ShenYuan-sean/Underwater-AprilTag-Board/check/0.png

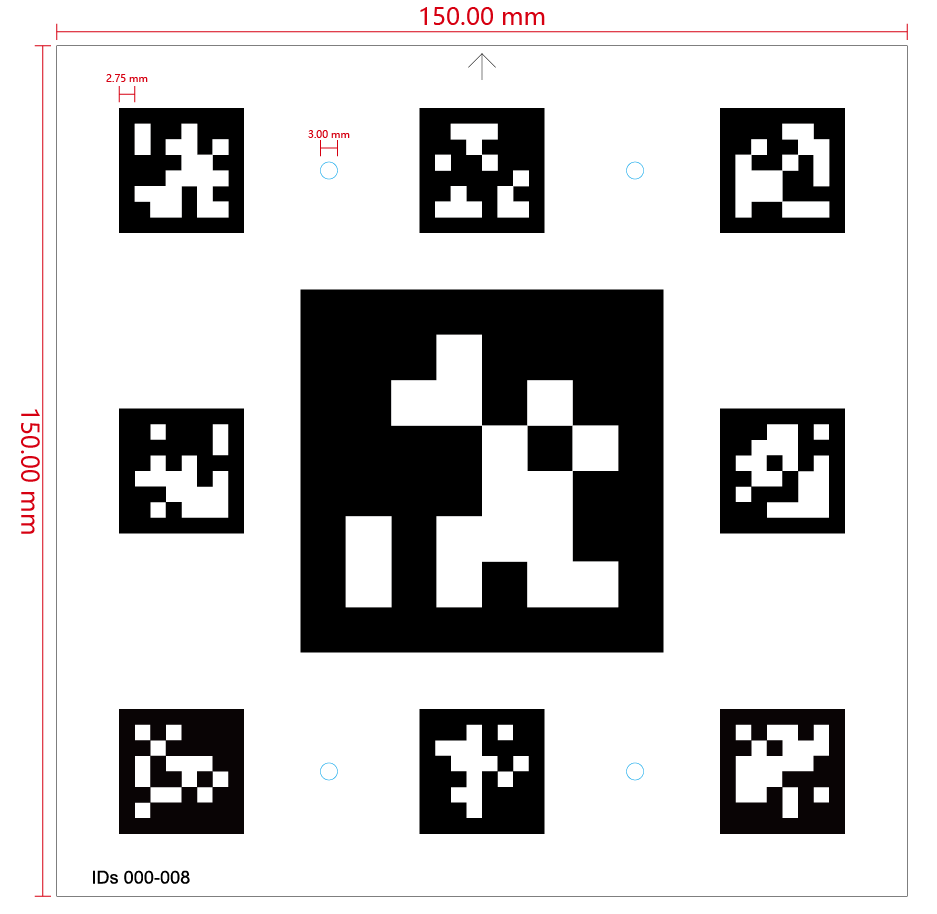
check/0.png
