ShenYuan-sean/Underwater-AprilTag-Board/check/1.png

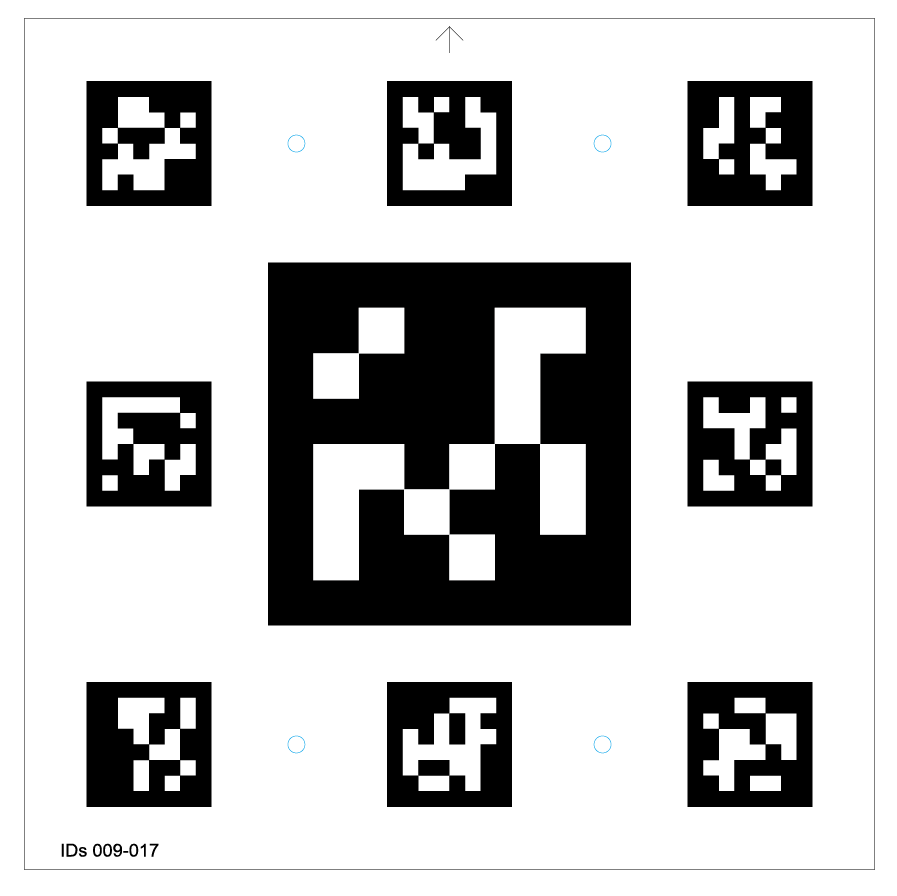
check/1.png
