ShenYuan-sean/Underwater-AprilTag-Board/check/2.png

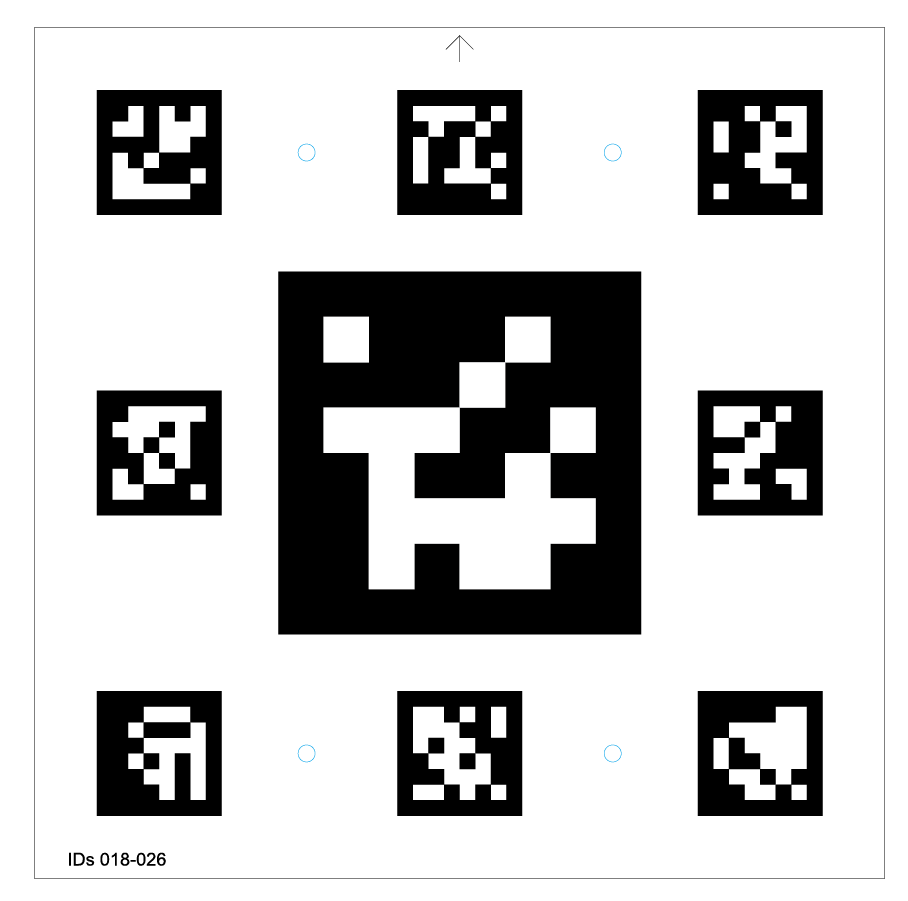
check/2.png
