ShenYuan-sean/Underwater-AprilTag-Board/check/3.png

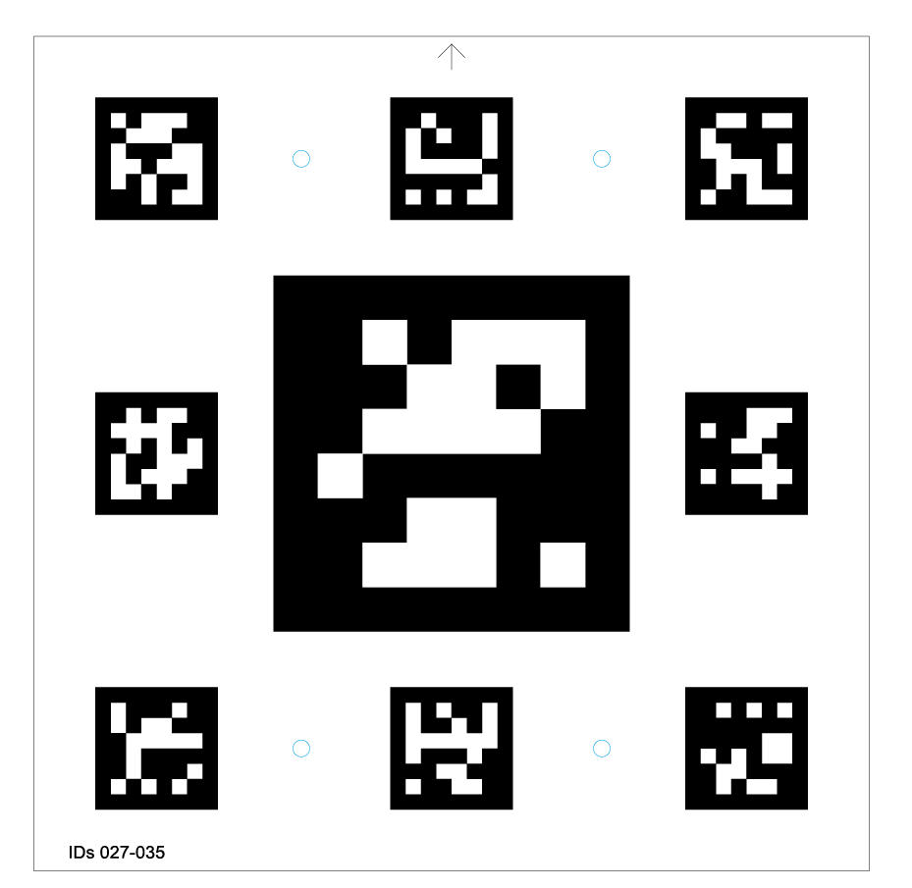
check/3.png
