ShenYuan-sean/Underwater-AprilTag-Board/check/4.png

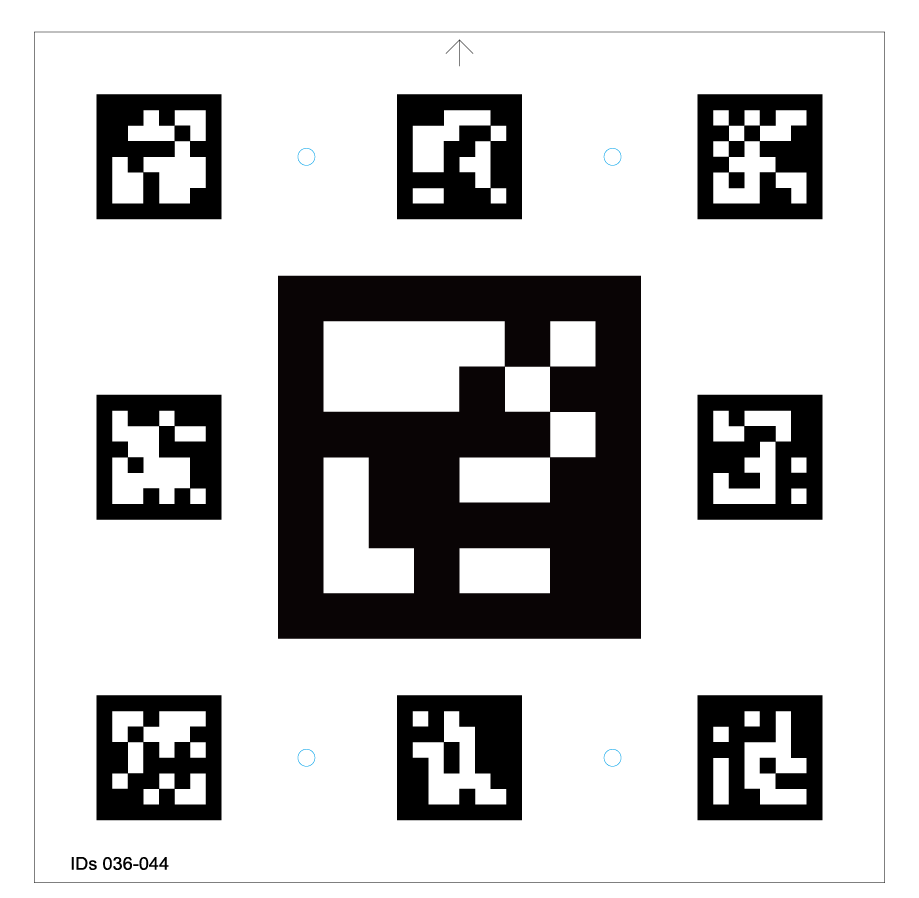
check/4.png
