ShenYuan-sean/Underwater-AprilTag-Board/check/5.png

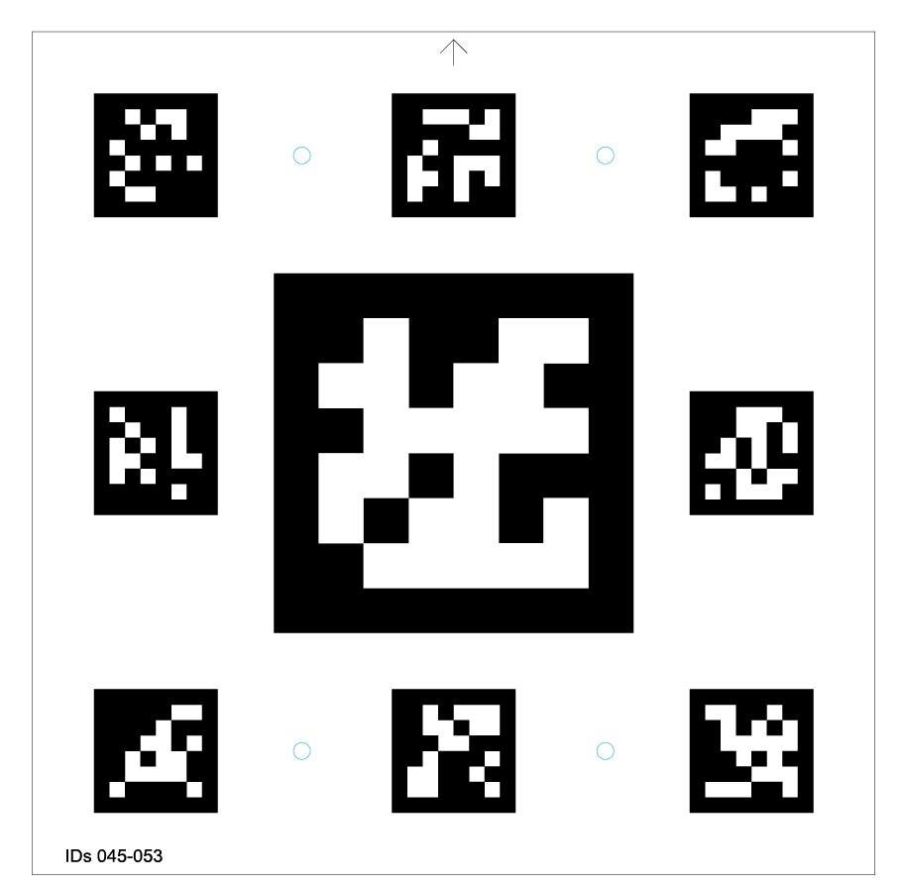
check/5.png
