ShenYuan-sean/Underwater-AprilTag-Board/Reservoir-AprilTag-Boards-20/加工厂复核/微信图片_20260824111517_369_489.png

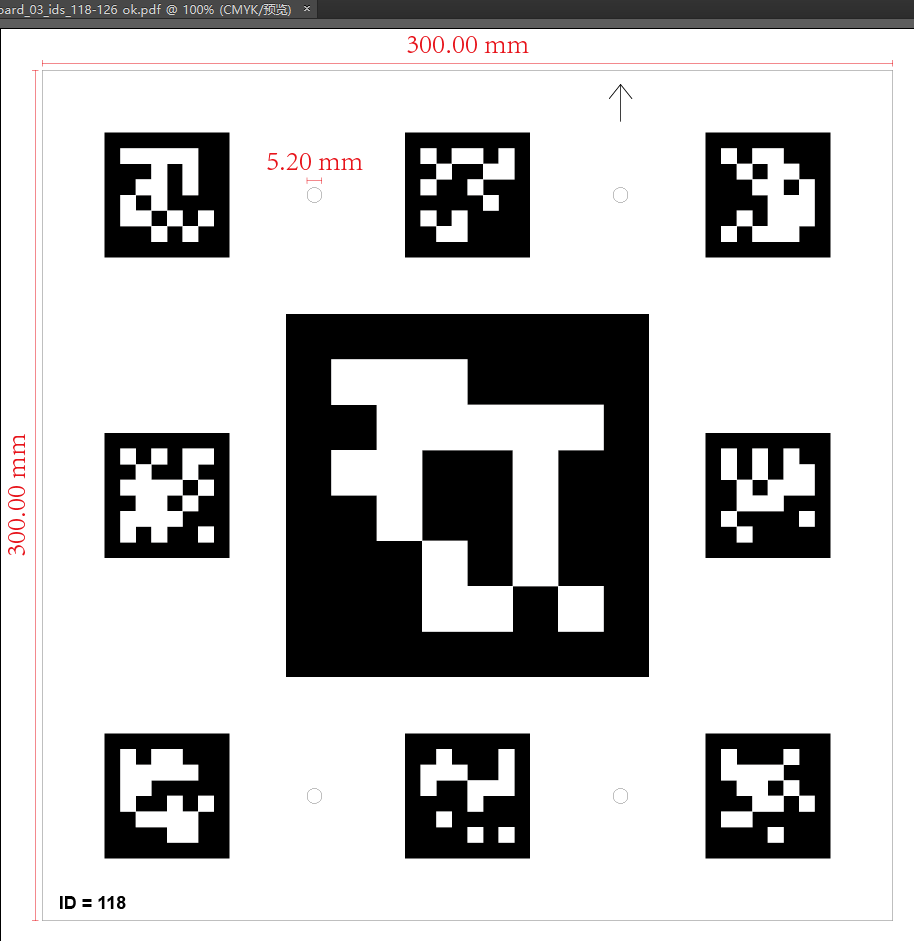
Reservoir-AprilTag-Boards-20/加工厂复核/微信图片_20260824111517_369_489.png
