ShenYuan-sean/Underwater-AprilTag-Board/Reservoir-AprilTag-Boards-20/加工厂复核/微信图片_20260824111823_383_489.png

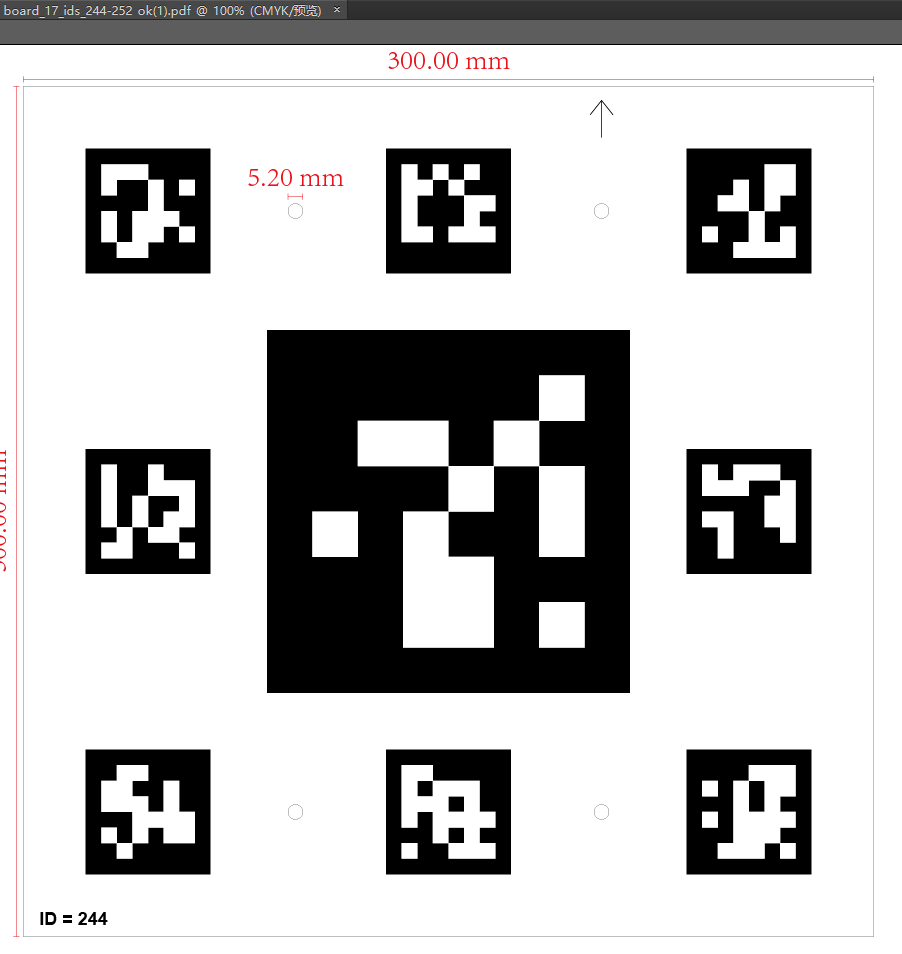
Reservoir-AprilTag-Boards-20/加工厂复核/微信图片_20260824111823_383_489.png
