ShenYuan-sean/Underwater-AprilTag-Board/Reservoir-AprilTag-Boards-20/generated/boards/board_13_ids_208-216.dxf

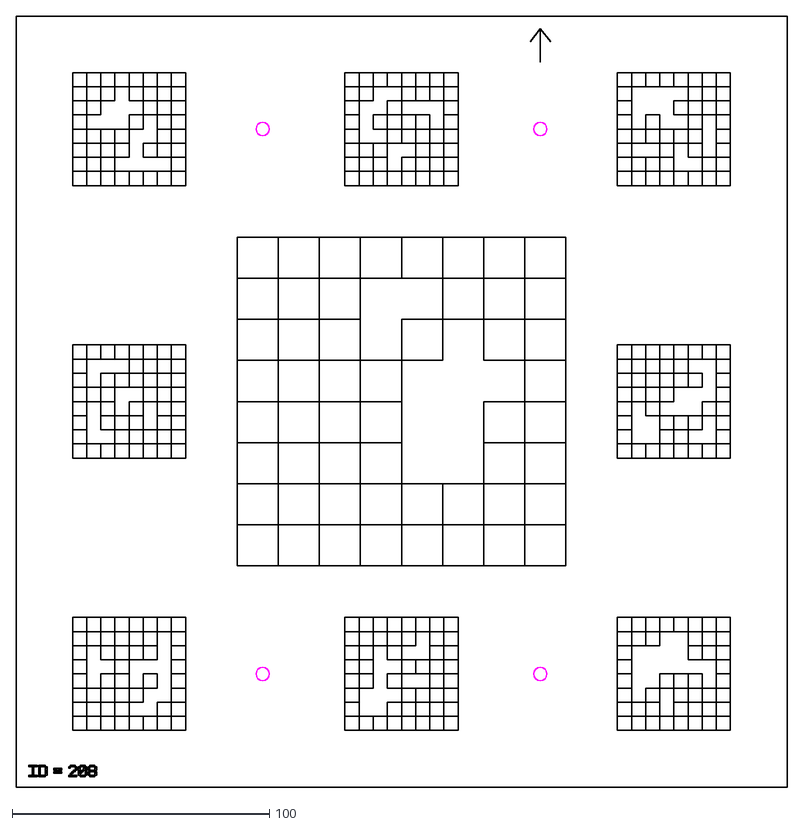
[picture p74: CAD file, 2026-08-25]
Reservoir-AprilTag-Boards-20/generated/boards/board_13_ids_208-216.dxf
300.0 x 300.0
