ShenYuan-sean/Underwater-AprilTag-Board/generated/face_02_guide.dxf

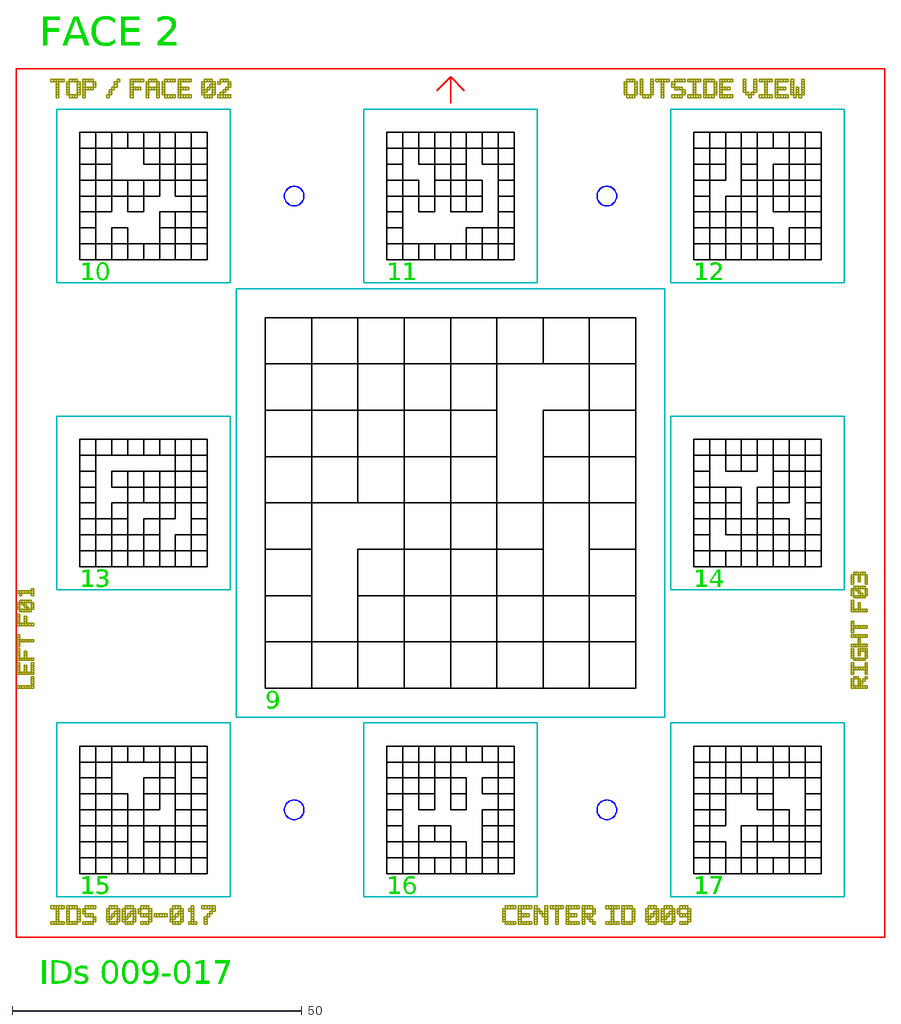
[picture p75: CAD file, 2026-08-11]
generated/face_02_guide.dxf
FACE 2
IDs 009-017
9
10
11
12
13
14
15
16
17
