ShenYuan-sean/Underwater-AprilTag-Board/Reservoir-AprilTag-Boards-20/batch_02/manufacturing/board_26_ids_325-333.dxf

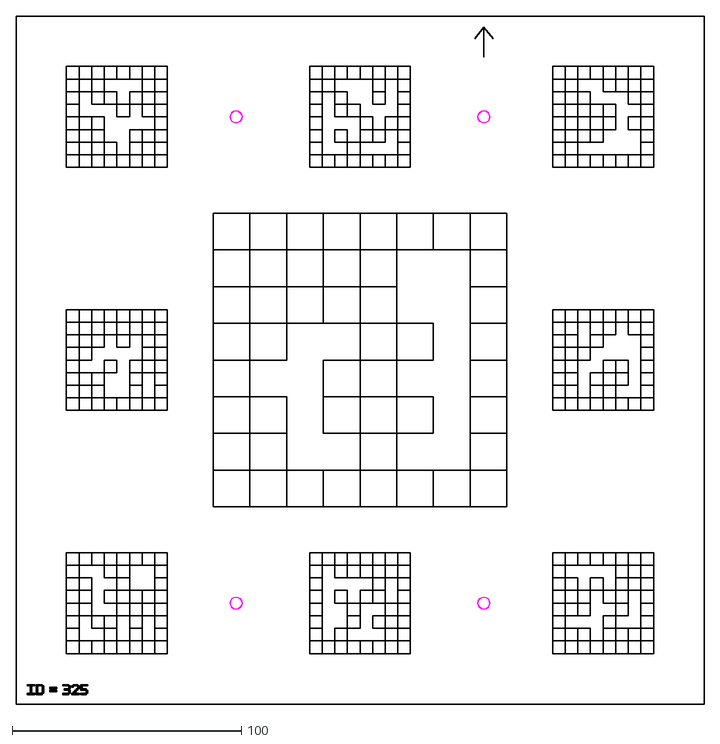
[picture p76: CAD file, 2026-10-02]
Reservoir-AprilTag-Boards-20/batch_02/manufacturing/board_26_ids_325-333.dxf
300.0 x 300.0
