ShenYuan-sean/Underwater-AprilTag-Board/Reservoir-AprilTag-Boards-20/generated/board_11_ids_190-198_guide.dxf

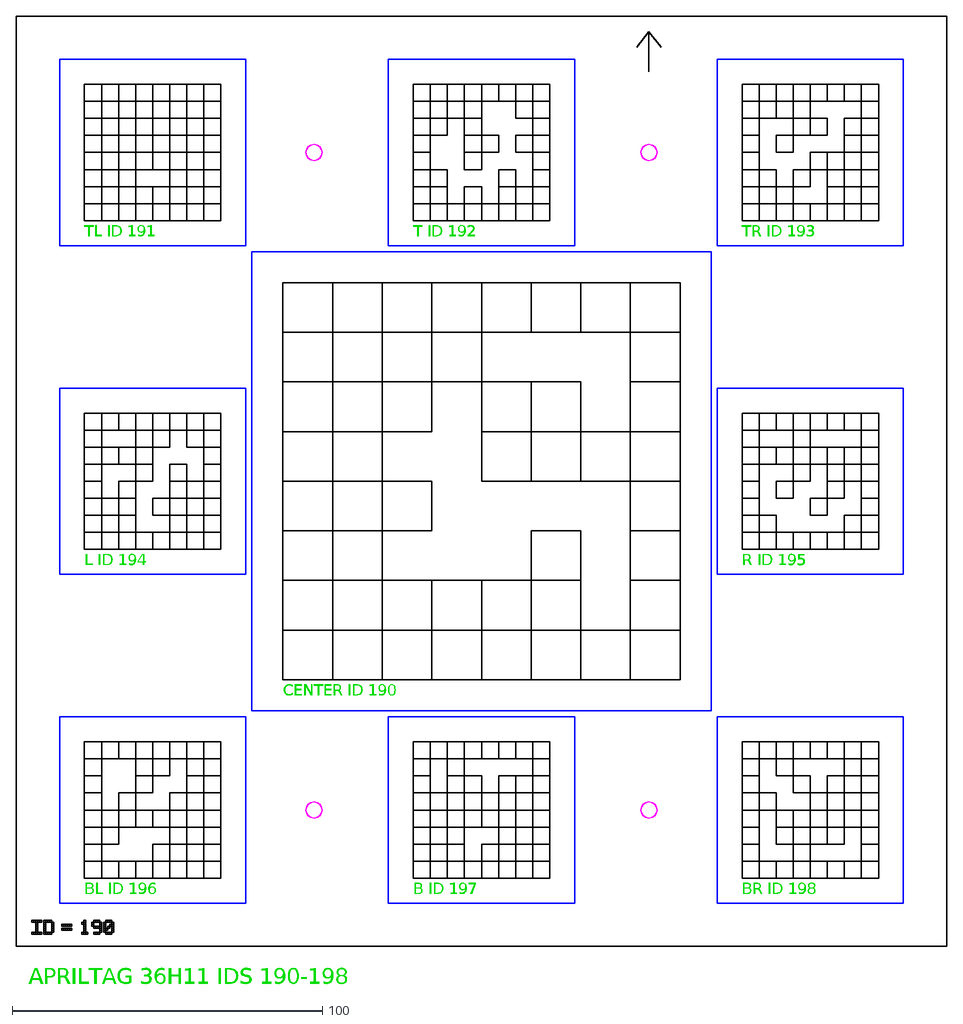
[picture p77: CAD file, 2026-08-25]
Reservoir-AprilTag-Boards-20/generated/board_11_ids_190-198_guide.dxf
CENTER ID 190
TL ID 191
T ID 192
TR ID 193
L ID 194
R ID 195
BL ID 196
B ID 197
BR ID 198
APRILTAG 36H11 IDS 190-198
