ShenYuan-sean/Underwater-AprilTag-Board/Reservoir-AprilTag-Boards-20/generated/boards/board_11_ids_190-198.dxf

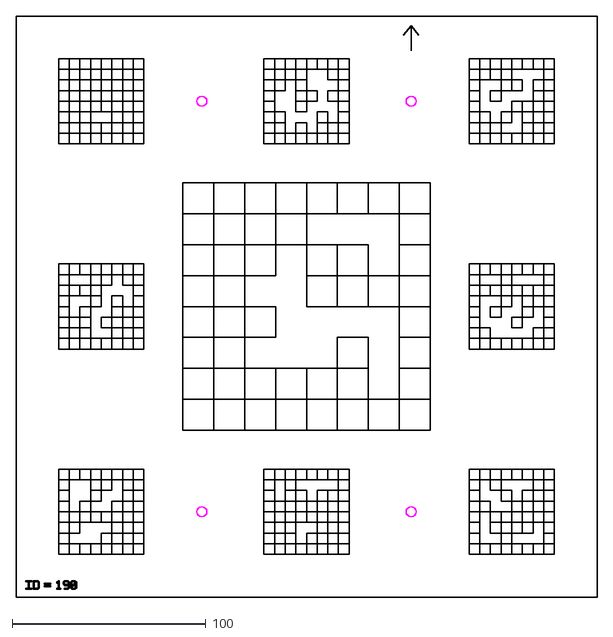
[picture p78: CAD file, 2026-08-25]
Reservoir-AprilTag-Boards-20/generated/boards/board_11_ids_190-198.dxf
300.0 x 300.0
