ShenYuan-sean/Underwater-AprilTag-Board/generated/hex_fixture_top_view.dxf

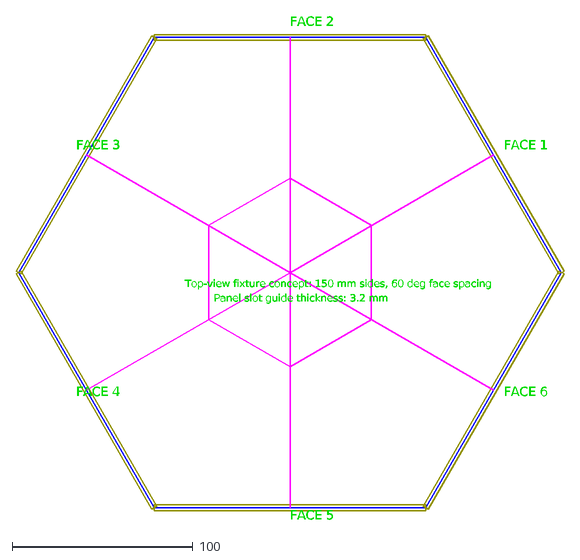
[picture p79: CAD file, 2026-08-11]
generated/hex_fixture_top_view.dxf
FACE 1
FACE 2
FACE 3
FACE 4
FACE 5
FACE 6
Top-view fixture concept: 150 mm sides, 60 deg face spacing
Panel slot guide thickness: 3.2 mm
