ShenYuan-sean/Underwater-AprilTag-Board/Reservoir-AprilTag-Boards-20/batch_02/generated/board_34_ids_397-405_guide.dxf

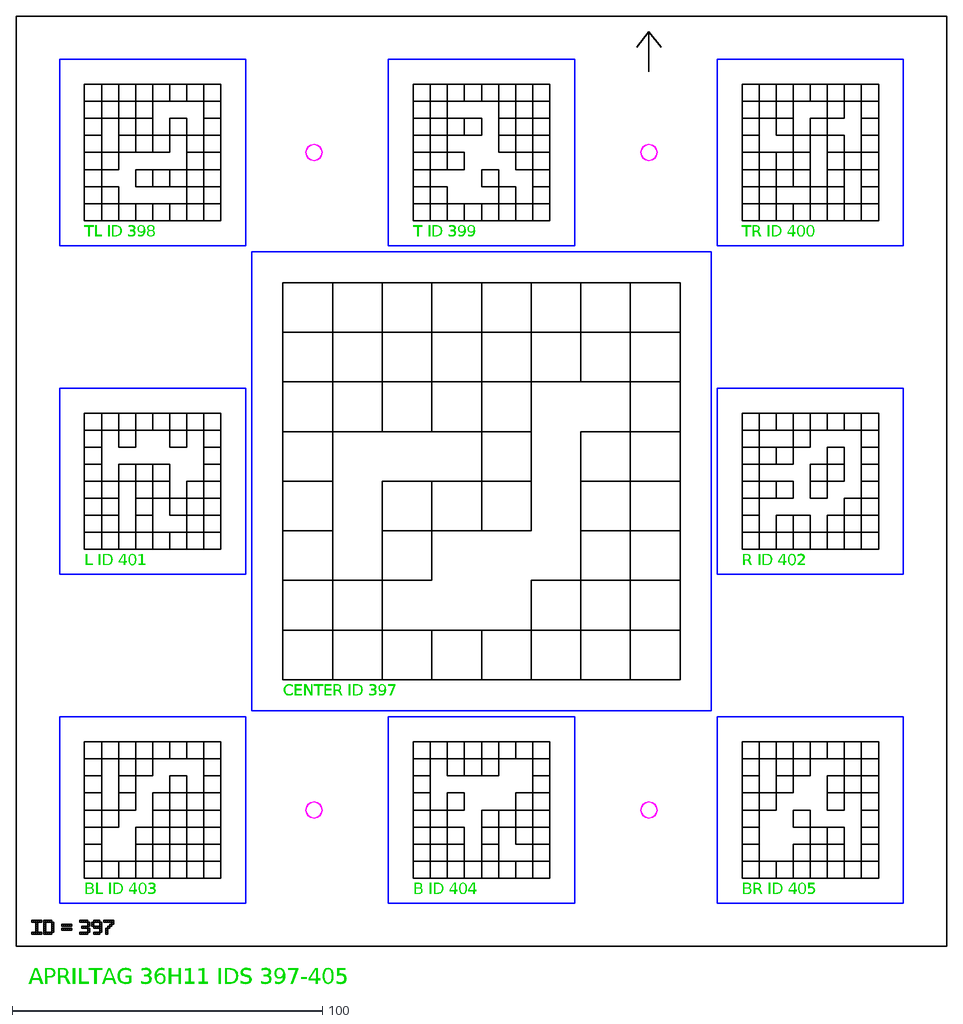
[picture p80: CAD file, 2026-10-02]
Reservoir-AprilTag-Boards-20/batch_02/generated/board_34_ids_397-405_guide.dxf
CENTER ID 397
TL ID 398
T ID 399
TR ID 400
L ID 401
R ID 402
BL ID 403
B ID 404
BR ID 405
APRILTAG 36H11 IDS 397-405
