ShenYuan-sean/Underwater-AprilTag-Board/Reservoir-AprilTag-Boards-20/batch_02/manufacturing/board_40_ids_451-459.dxf

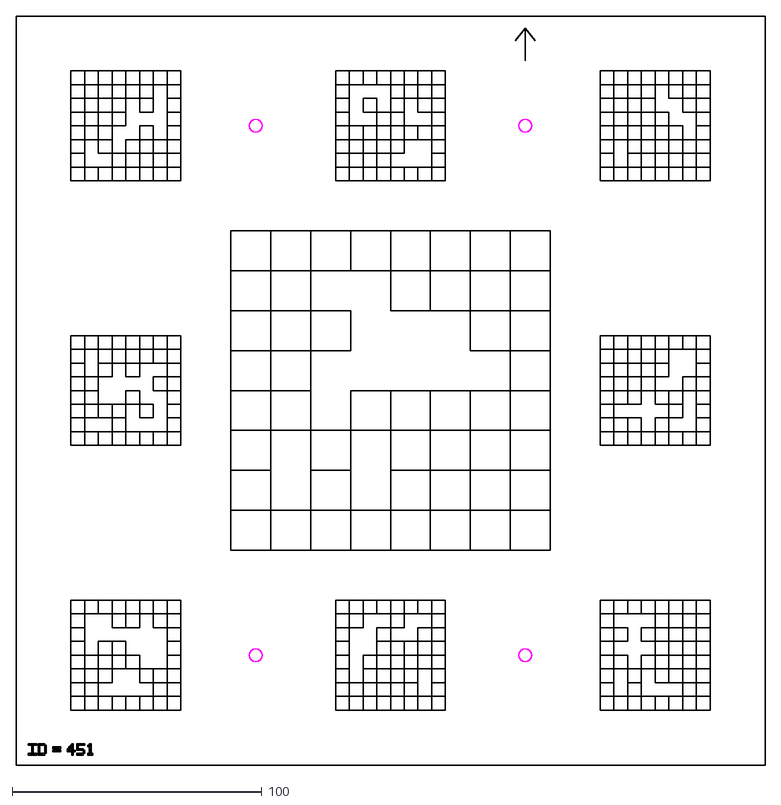
[picture p81: CAD file, 2026-10-02]
Reservoir-AprilTag-Boards-20/batch_02/manufacturing/board_40_ids_451-459.dxf
300.0 x 300.0
