ShenYuan-sean/Underwater-AprilTag-Board/Reservoir-AprilTag-Boards-20/generated/board_20_ids_271-279_guide.dxf

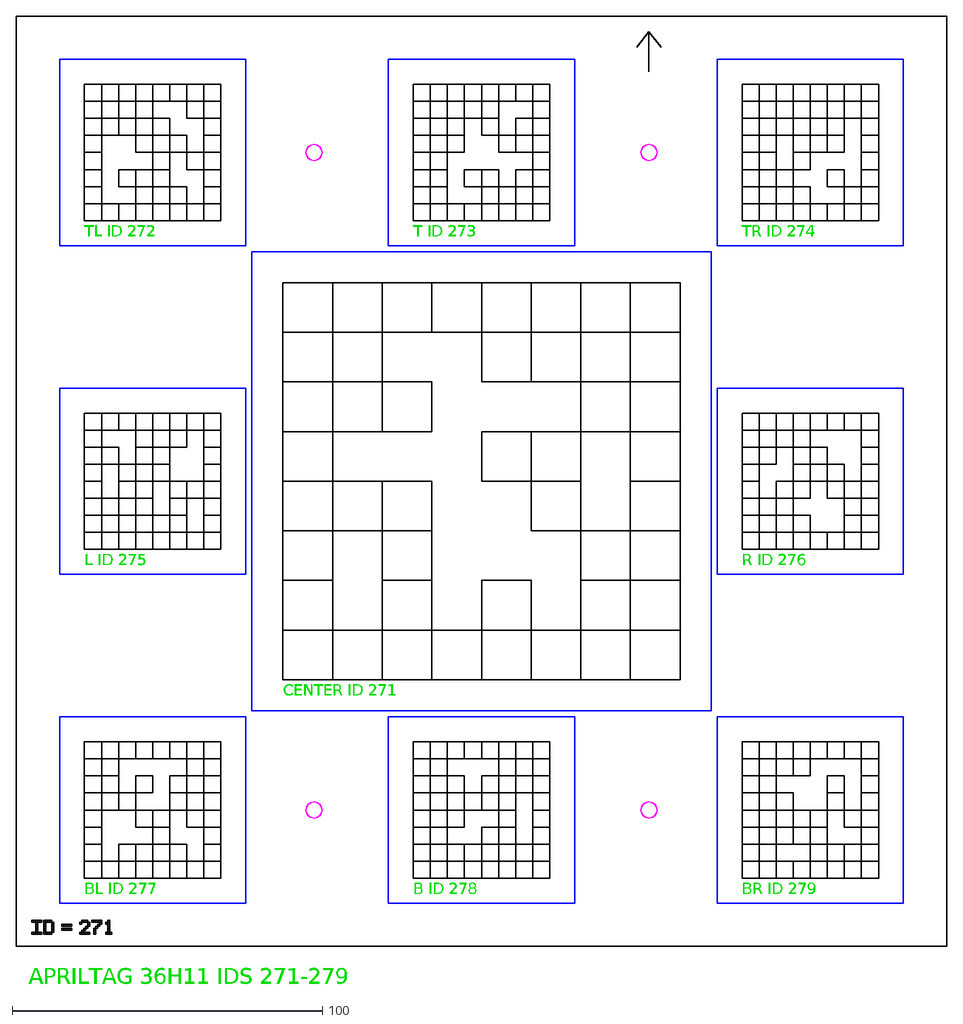
[picture p82: CAD file, 2026-08-25]
Reservoir-AprilTag-Boards-20/generated/board_20_ids_271-279_guide.dxf
CENTER ID 271
TL ID 272
T ID 273
TR ID 274
L ID 275
R ID 276
BL ID 277
B ID 278
BR ID 279
APRILTAG 36H11 IDS 271-279
