ShenYuan-sean/Underwater-AprilTag-Board/Reservoir-AprilTag-Boards-20/generated/boards/board_16_ids_235-243.dxf

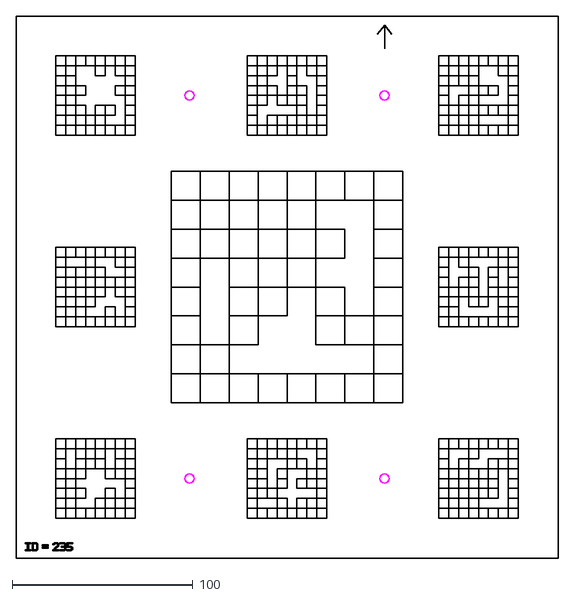
[picture p83: CAD file, 2026-08-25]
Reservoir-AprilTag-Boards-20/generated/boards/board_16_ids_235-243.dxf
300.0 x 300.0
