ShenYuan-sean/Underwater-AprilTag-Board/generated/all_faces_sheet_guide.dxf

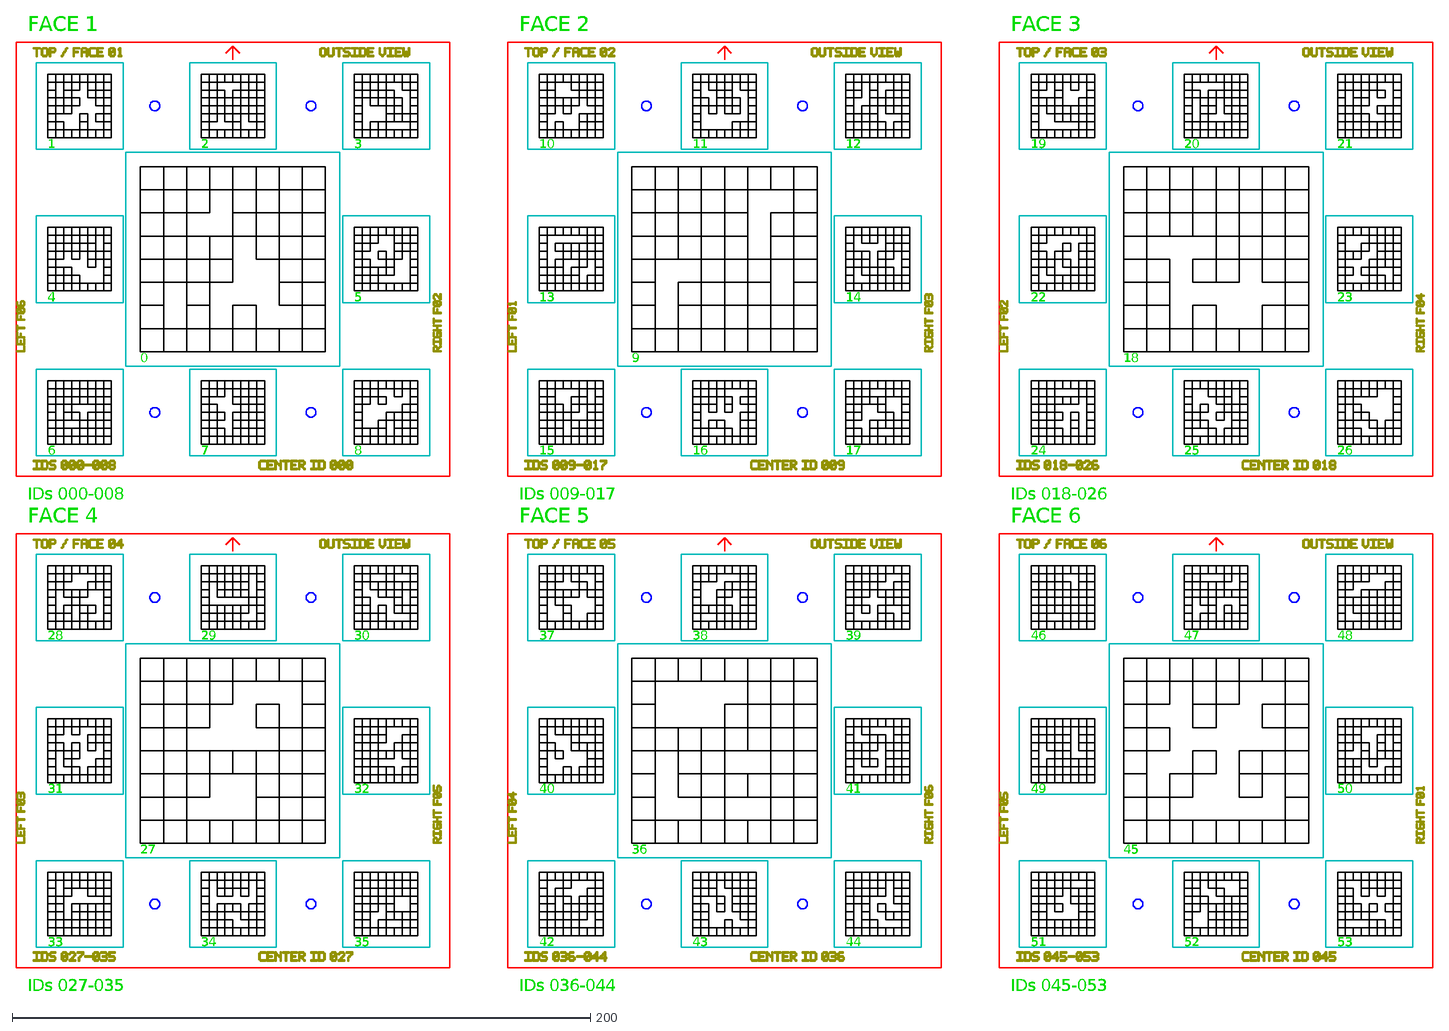
[picture p84: CAD file, 2026-08-11]
generated/all_faces_sheet_guide.dxf
FACE 1
IDs 000-008
0
1
2
3
4
5
6
7
8
FACE 2
IDs 009-017
9
10
11
12
13
14
15
16
17
FACE 3
IDs 018-026
18
19
20
21
22
23
24
25
26
FACE 4
IDs 027-035
27
28
29
30
31
32
33
34
35
FACE 5
IDs 036-044
36
37
38
39
40
41
42
43
44
FACE 6
IDs 045-053
45
46
47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
