ShenYuan-sean/Underwater-AprilTag-Board/Reservoir-AprilTag-Boards-20/batch_02/generated/board_36_ids_415-423.dxf

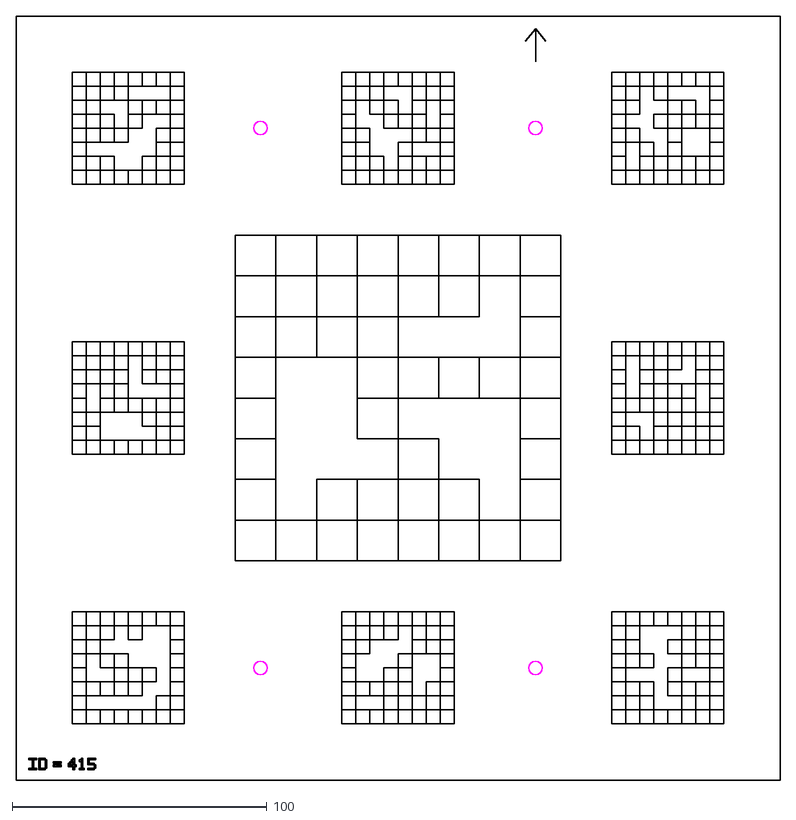
[picture p85: CAD file, 2026-10-02]
Reservoir-AprilTag-Boards-20/batch_02/generated/board_36_ids_415-423.dxf
300.0 x 300.0
