ShenYuan-sean/Underwater-AprilTag-Board/Reservoir-AprilTag-Boards-20/generated/board_05_ids_136-144.dxf

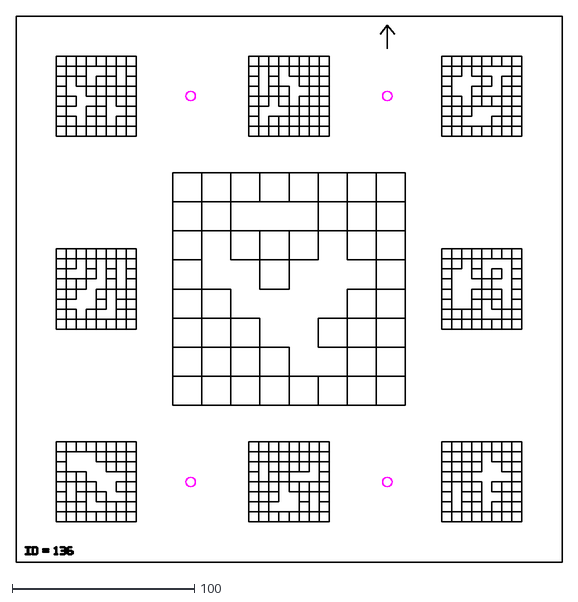
[picture p86: CAD file, 2026-08-25]
Reservoir-AprilTag-Boards-20/generated/board_05_ids_136-144.dxf
300.0 x 300.0
