ShenYuan-sean/Underwater-AprilTag-Board/Reservoir-AprilTag-Boards-20/generated/boards/board_20_ids_271-279.dxf

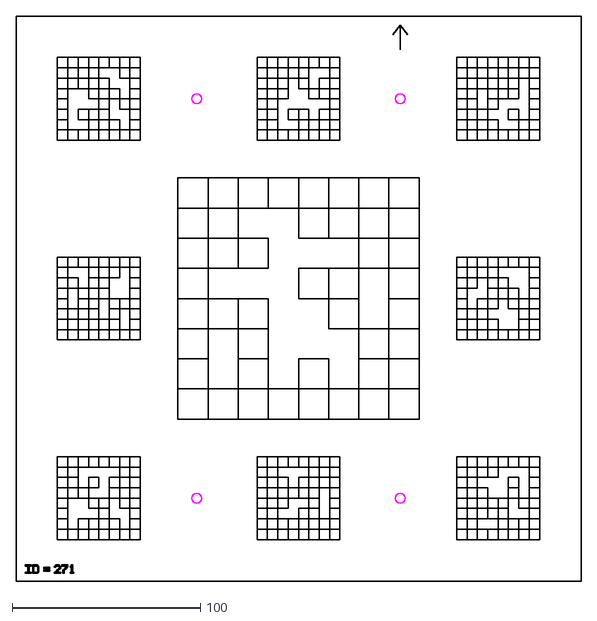
[picture p87: CAD file, 2026-08-25]
Reservoir-AprilTag-Boards-20/generated/boards/board_20_ids_271-279.dxf
300.0 x 300.0
