ShenYuan-sean/Underwater-AprilTag-Board/generated/face_04_guide.dxf

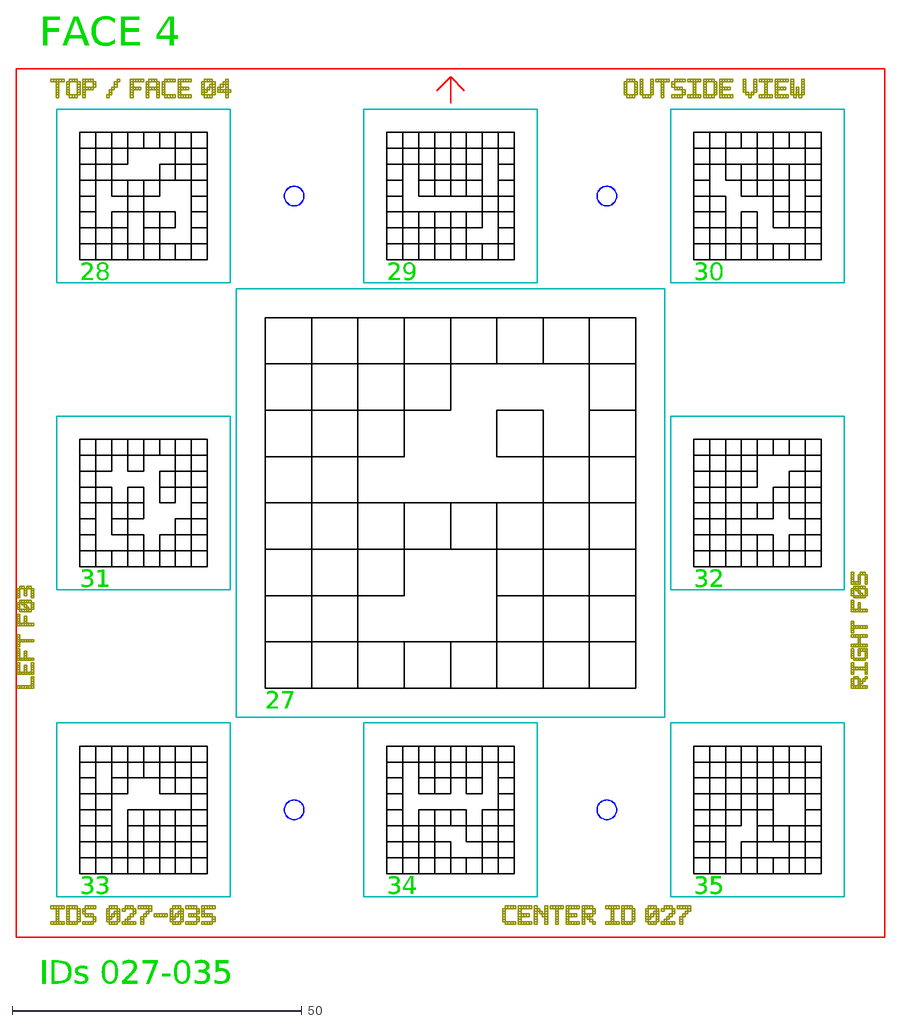
[picture p88: CAD file, 2026-08-11]
generated/face_04_guide.dxf
FACE 4
IDs 027-035
27
28
29
30
31
32
33
34
35
