ShenYuan-sean/Underwater-AprilTag-Board/Reservoir-AprilTag-Boards-20/batch_02/manufacturing/board_38_ids_433-441.dxf

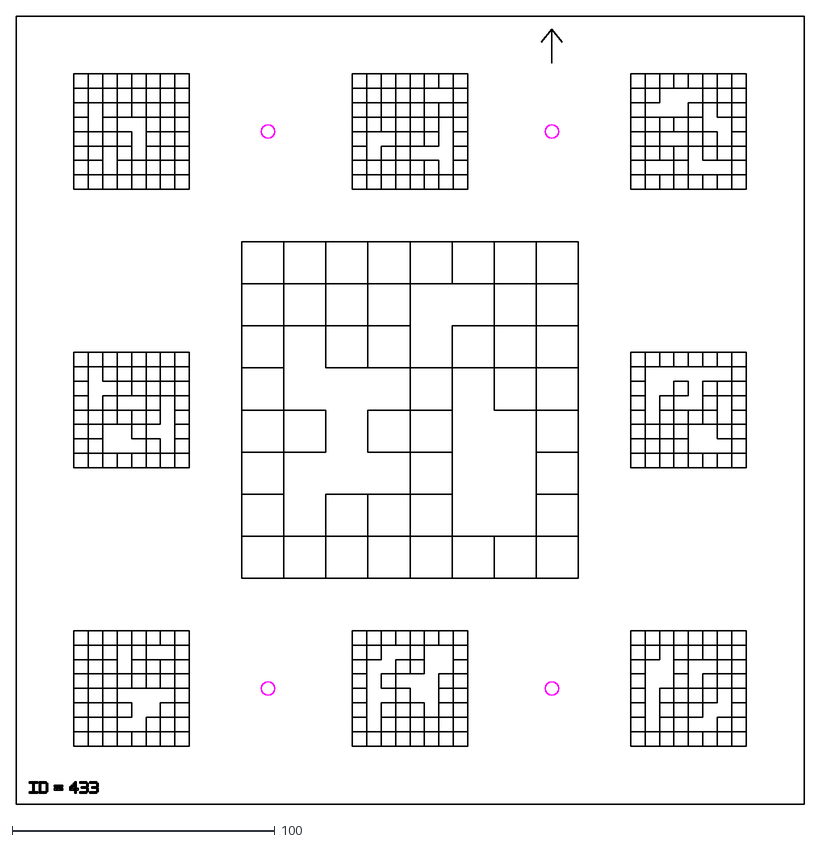
[picture p89: CAD file, 2026-10-02]
Reservoir-AprilTag-Boards-20/batch_02/manufacturing/board_38_ids_433-441.dxf
300.0 x 300.0
