ShenYuan-sean/Underwater-AprilTag-Board/Reservoir-AprilTag-Boards-20/generated/board_15_ids_226-234.dxf

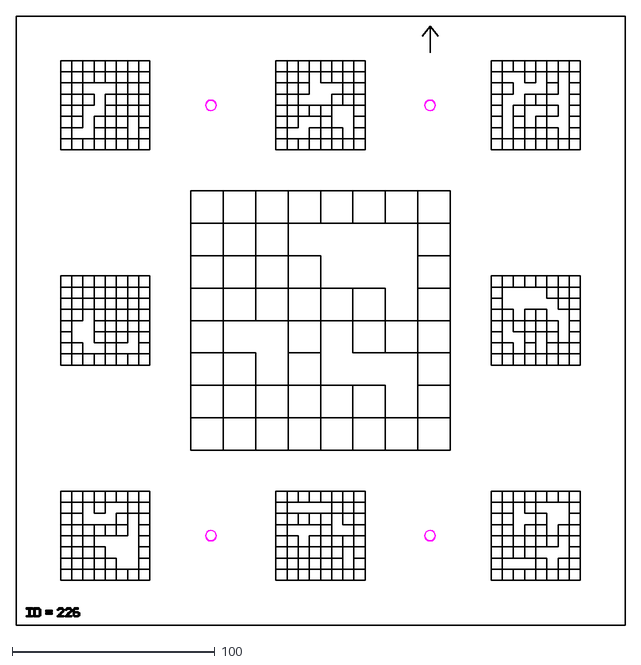
[picture p90: CAD file, 2026-08-25]
Reservoir-AprilTag-Boards-20/generated/board_15_ids_226-234.dxf
300.0 x 300.0
