ShenYuan-sean/Underwater-AprilTag-Board/generated/face_06.dxf

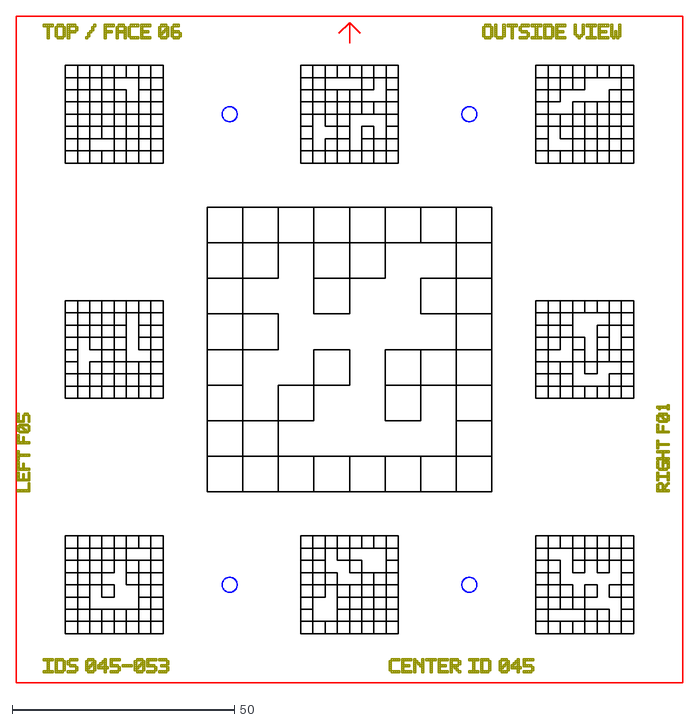
[picture p91: CAD file, 2026-08-11]
generated/face_06.dxf
150.0 x 150.0
