ShenYuan-sean/Underwater-AprilTag-Board/Reservoir-AprilTag-Boards-20/batch_02/generated/board_21_ids_280-288_guide.dxf

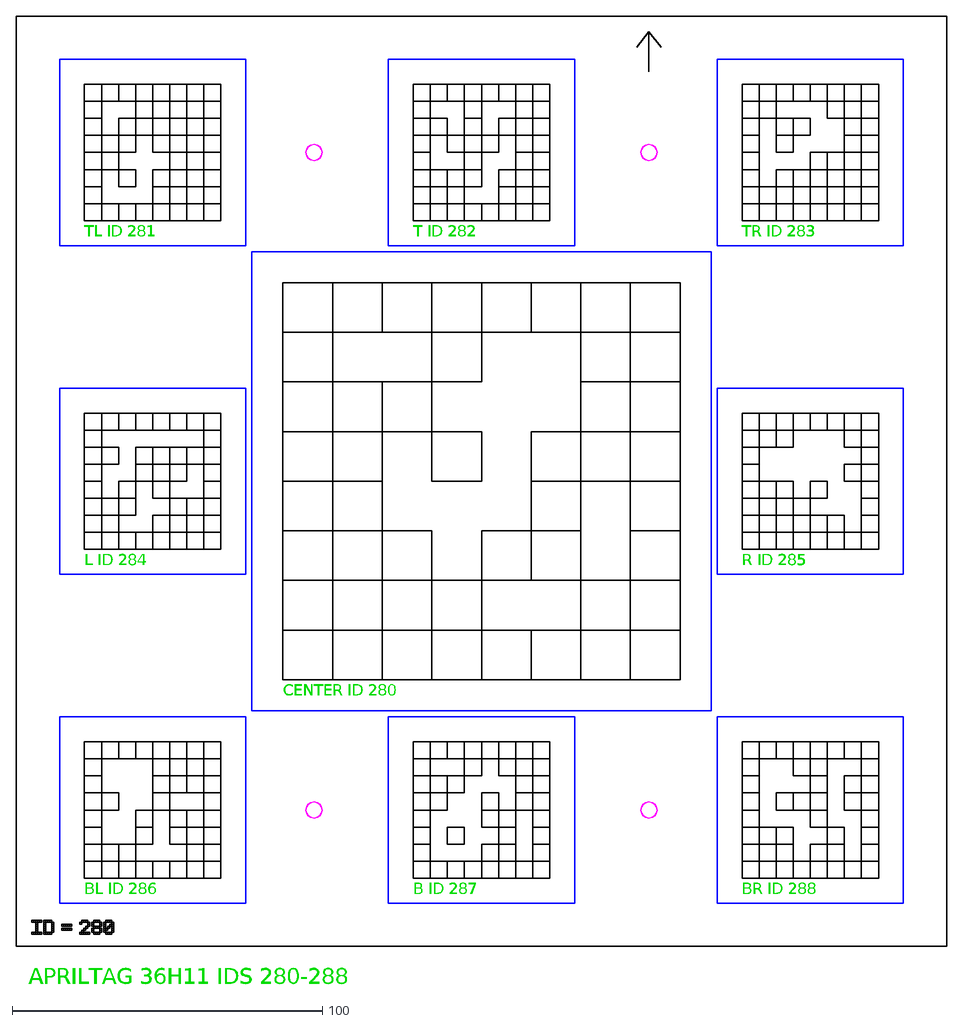
[picture p92: CAD file, 2026-10-02]
Reservoir-AprilTag-Boards-20/batch_02/generated/board_21_ids_280-288_guide.dxf
CENTER ID 280
TL ID 281
T ID 282
TR ID 283
L ID 284
R ID 285
BL ID 286
B ID 287
BR ID 288
APRILTAG 36H11 IDS 280-288
