ShenYuan-sean/Underwater-AprilTag-Board/Reservoir-AprilTag-Boards-20/batch_02/manufacturing/board_37_ids_424-432.dxf

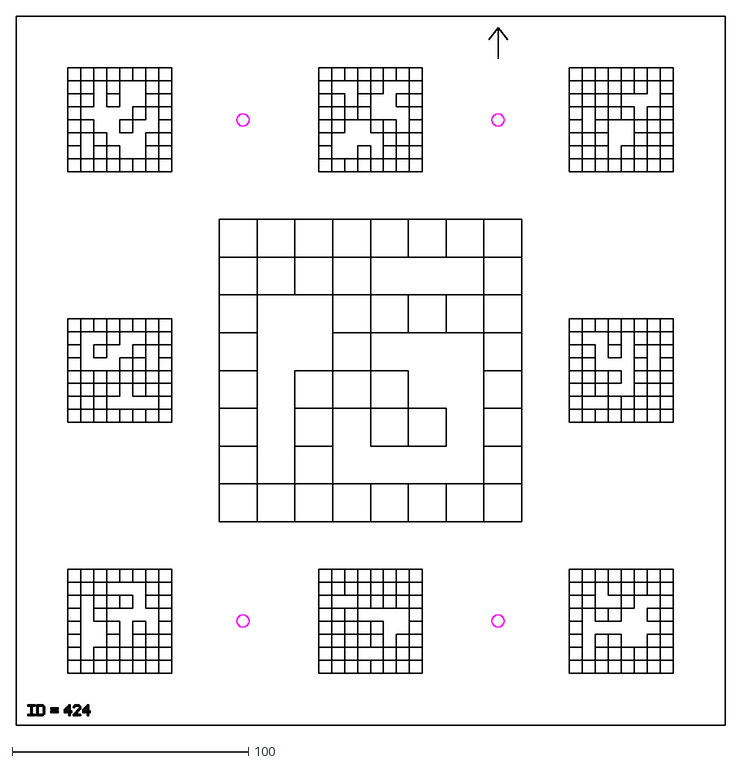
[picture p93: CAD file, 2026-10-02]
Reservoir-AprilTag-Boards-20/batch_02/manufacturing/board_37_ids_424-432.dxf
300.0 x 300.0
