ShenYuan-sean/Underwater-AprilTag-Board/Reservoir-AprilTag-Boards-20/generated/board_05_ids_136-144_guide.dxf

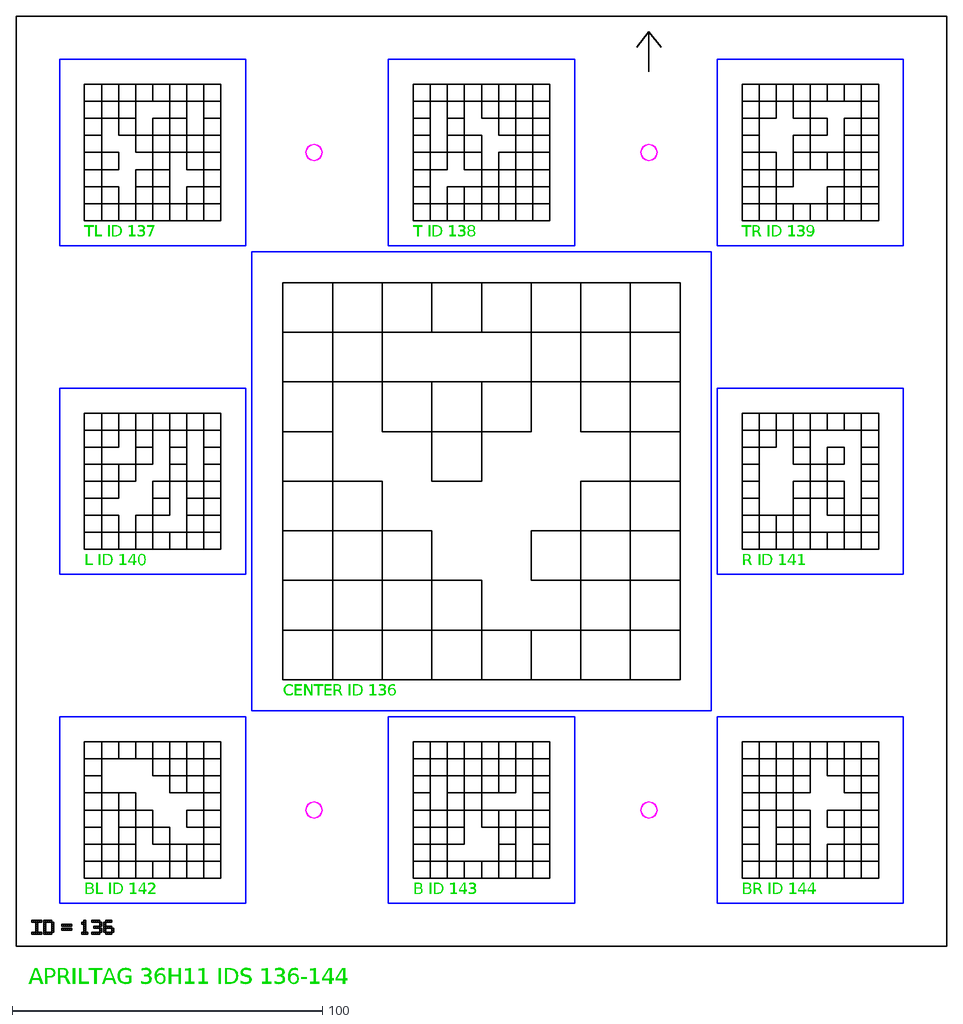
[picture p94: CAD file, 2026-08-25]
Reservoir-AprilTag-Boards-20/generated/board_05_ids_136-144_guide.dxf
CENTER ID 136
TL ID 137
T ID 138
TR ID 139
L ID 140
R ID 141
BL ID 142
B ID 143
BR ID 144
APRILTAG 36H11 IDS 136-144
