ShenYuan-sean/Underwater-AprilTag-Board/Reservoir-AprilTag-Boards-20/generated/boards/board_01_ids_100-108.dxf

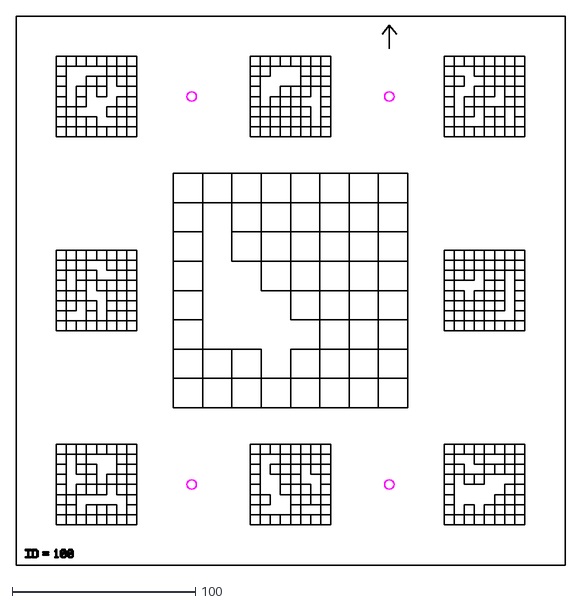
[picture p95: CAD file, 2026-08-25]
Reservoir-AprilTag-Boards-20/generated/boards/board_01_ids_100-108.dxf
300.0 x 300.0
