ShenYuan-sean/Underwater-AprilTag-Board/generated/all_faces_sheet.dxf

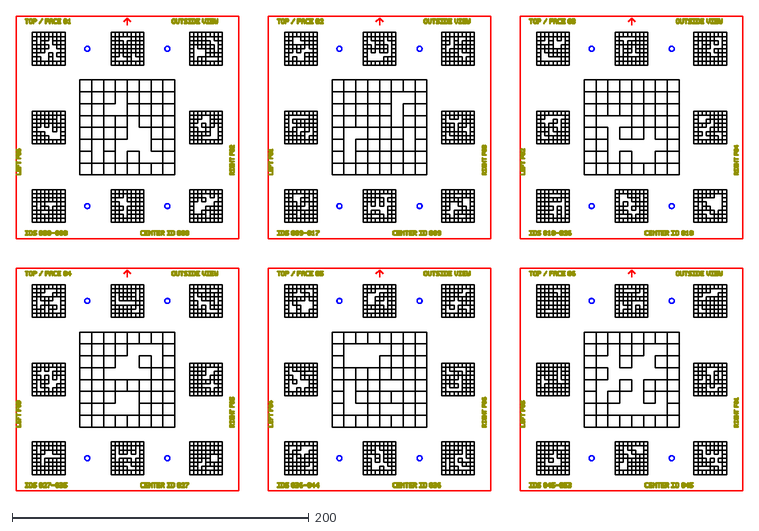
[picture p96: CAD file, 2026-08-11]
generated/all_faces_sheet.dxf
490.0 x 320.0
