ShenYuan-sean/Underwater-AprilTag-Board/Reservoir-AprilTag-Boards-20/batch_02/generated/board_24_ids_307-315_guide.dxf

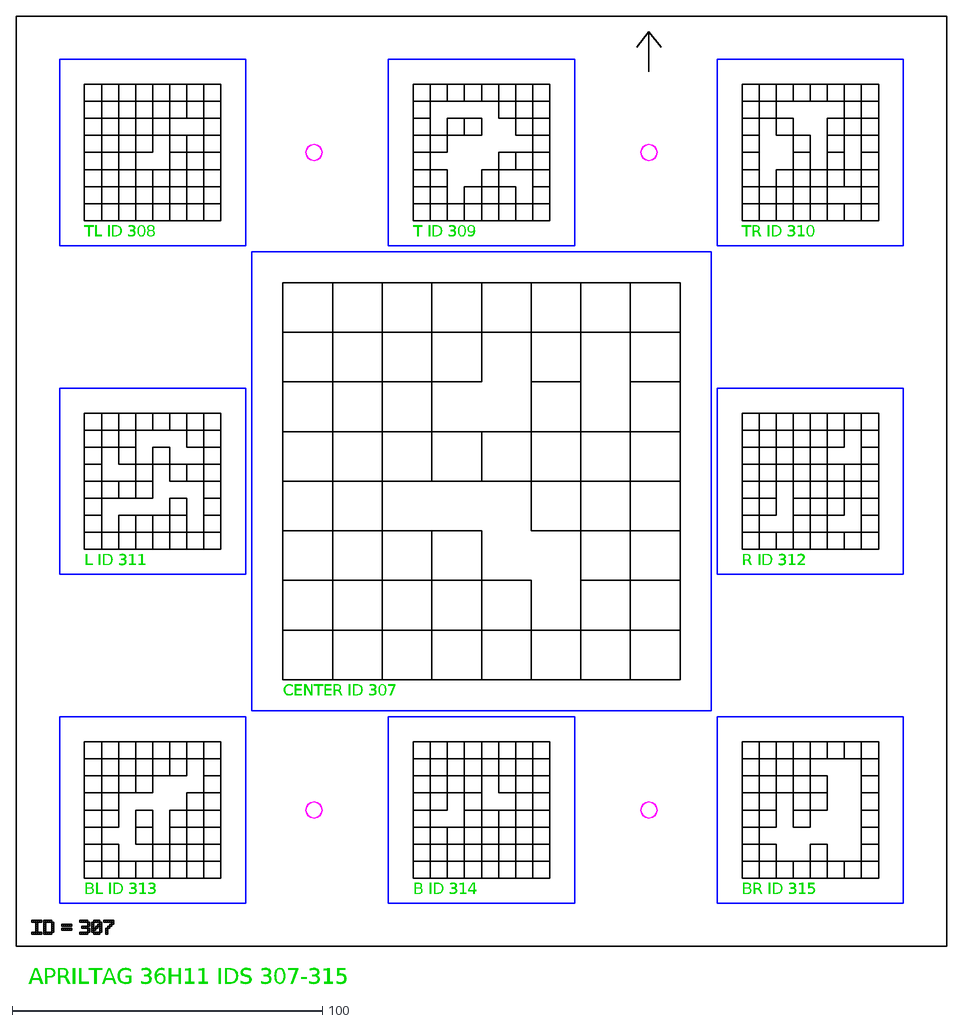
[picture p97: CAD file, 2026-10-02]
Reservoir-AprilTag-Boards-20/batch_02/generated/board_24_ids_307-315_guide.dxf
CENTER ID 307
TL ID 308
T ID 309
TR ID 310
L ID 311
R ID 312
BL ID 313
B ID 314
BR ID 315
APRILTAG 36H11 IDS 307-315
