ShenYuan-sean/Underwater-AprilTag-Board/Reservoir-AprilTag-Boards-20/batch_02/manufacturing/board_25_ids_316-324.dxf

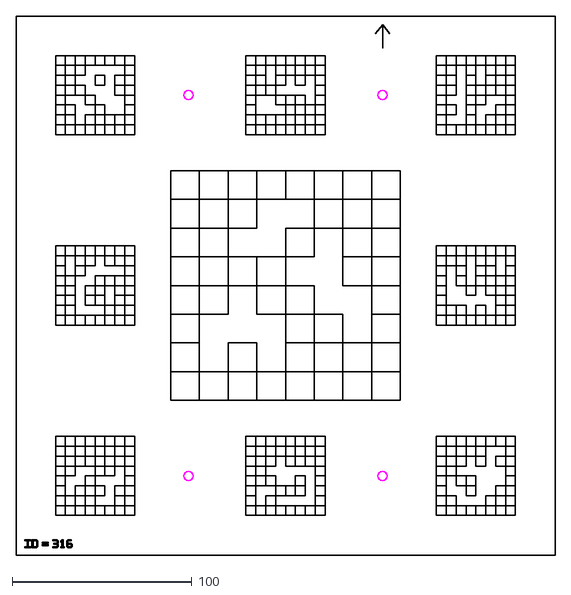
[picture p98: CAD file, 2026-10-02]
Reservoir-AprilTag-Boards-20/batch_02/manufacturing/board_25_ids_316-324.dxf
300.0 x 300.0
