ShenYuan-sean/Underwater-AprilTag-Board/Reservoir-AprilTag-Boards-20/generated/boards/board_04_ids_127-135.dxf

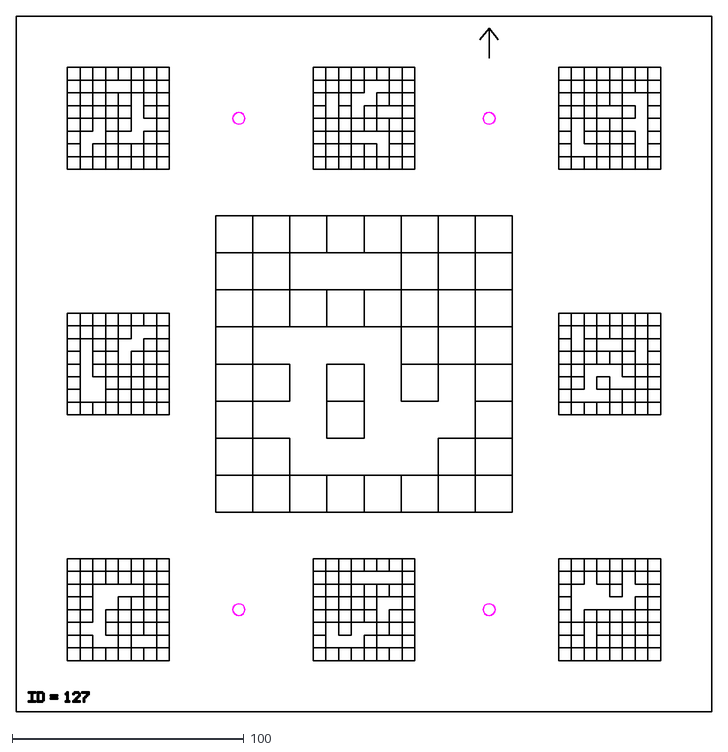
[picture p99: CAD file, 2026-08-25]
Reservoir-AprilTag-Boards-20/generated/boards/board_04_ids_127-135.dxf
300.0 x 300.0
