ShenYuan-sean/Underwater-AprilTag-Board/generated/face_04.dxf

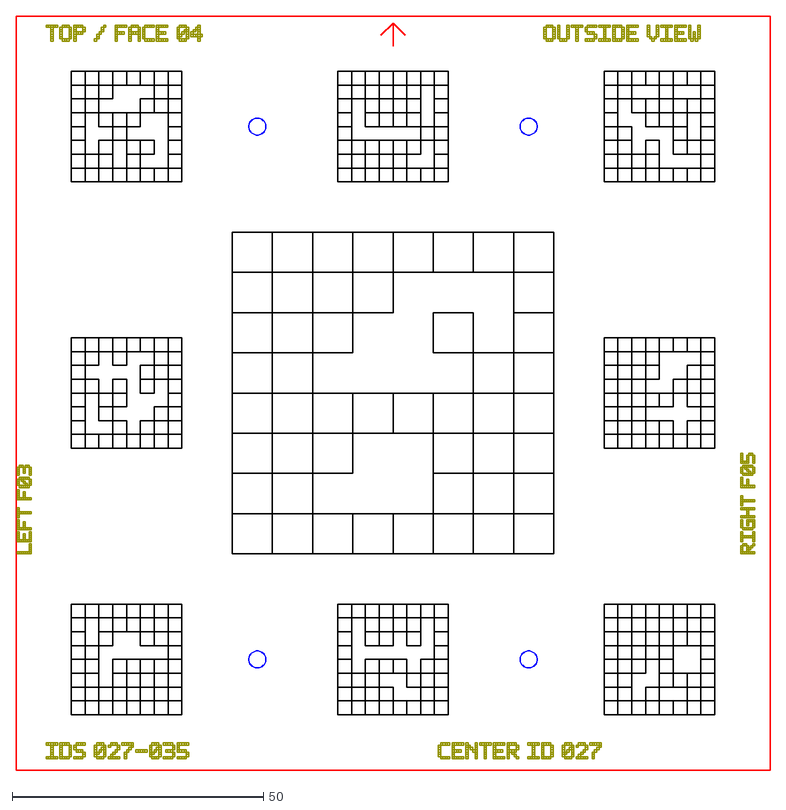
[picture p100: CAD file, 2026-08-11]
generated/face_04.dxf
150.0 x 150.0
