ShenYuan-sean/Underwater-AprilTag-Board/Reservoir-AprilTag-Boards-20/generated/board_06_ids_145-153_guide.dxf

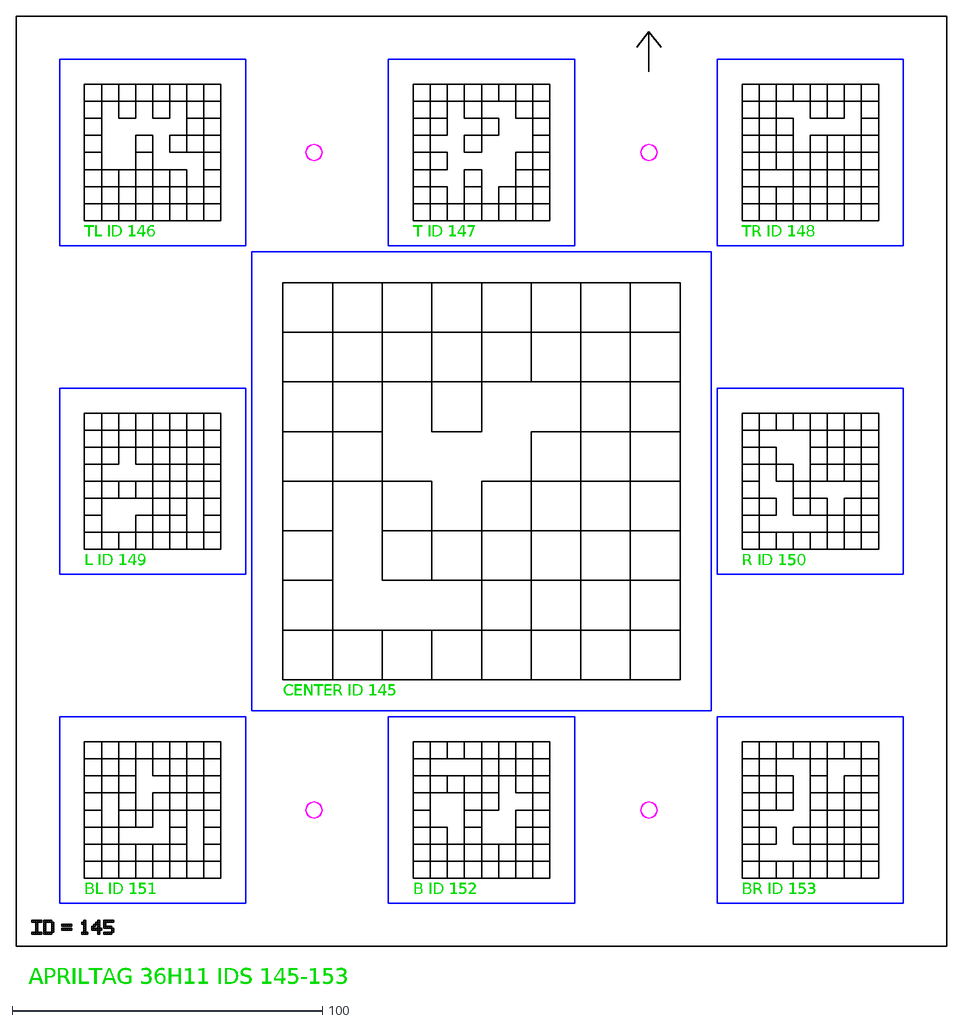
[picture p102: CAD file, 2026-08-25]
Reservoir-AprilTag-Boards-20/generated/board_06_ids_145-153_guide.dxf
CENTER ID 145
TL ID 146
T ID 147
TR ID 148
L ID 149
R ID 150
BL ID 151
B ID 152
BR ID 153
APRILTAG 36H11 IDS 145-153
