ShenYuan-sean/Underwater-AprilTag-Board/generated/face_01_guide.dxf

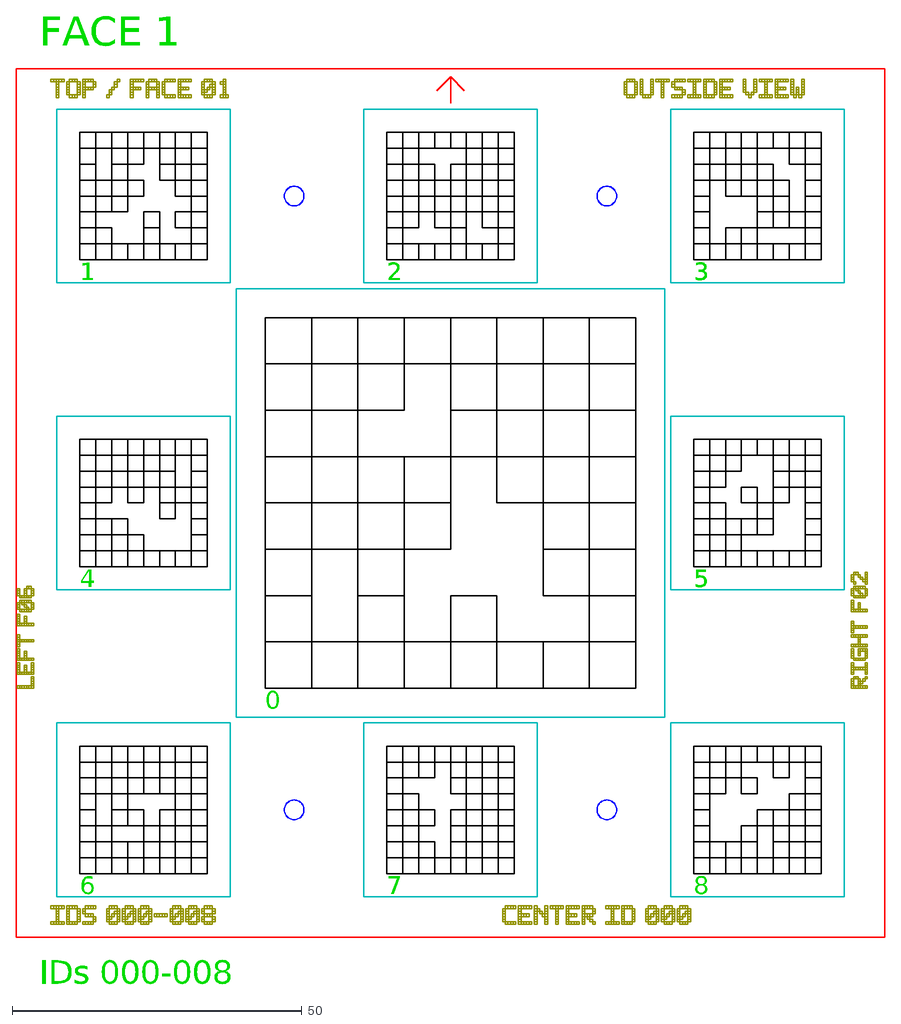
[picture p103: CAD file, 2026-08-11]
generated/face_01_guide.dxf
FACE 1
IDs 000-008
0
1
2
3
4
5
6
7
8
