ShenYuan-sean/Underwater-AprilTag-Board/Reservoir-AprilTag-Boards-20/batch_02/generated/board_32_ids_379-387.dxf

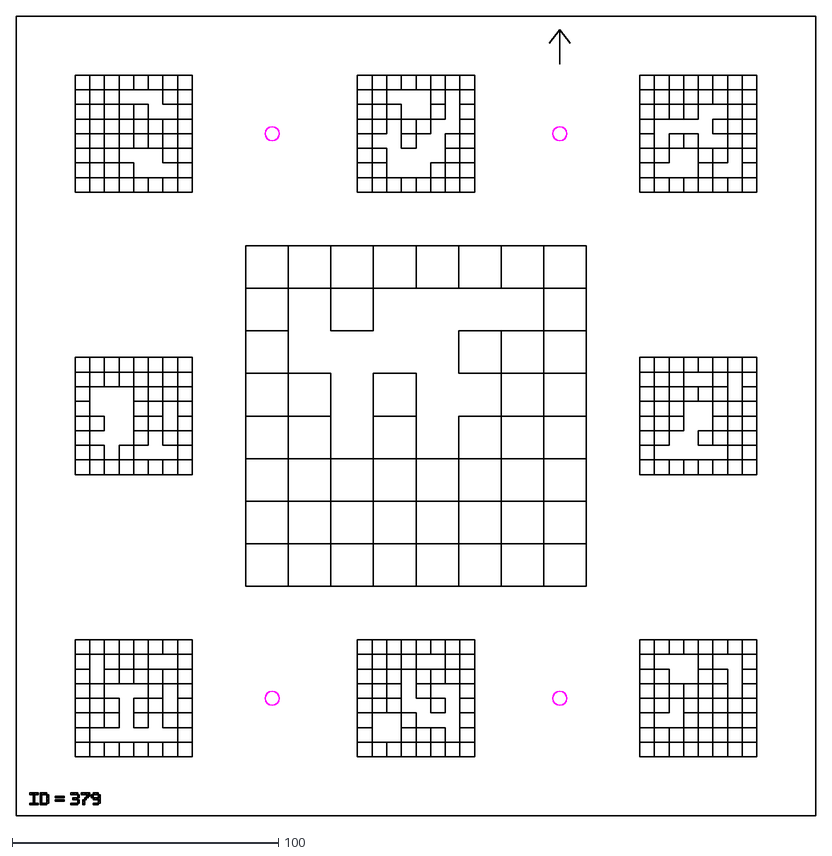
[picture p104: CAD file, 2026-10-02]
Reservoir-AprilTag-Boards-20/batch_02/generated/board_32_ids_379-387.dxf
300.0 x 300.0
