ShenYuan-sean/Underwater-AprilTag-Board/Reservoir-AprilTag-Boards-20/generated/board_08_ids_163-171_guide.dxf

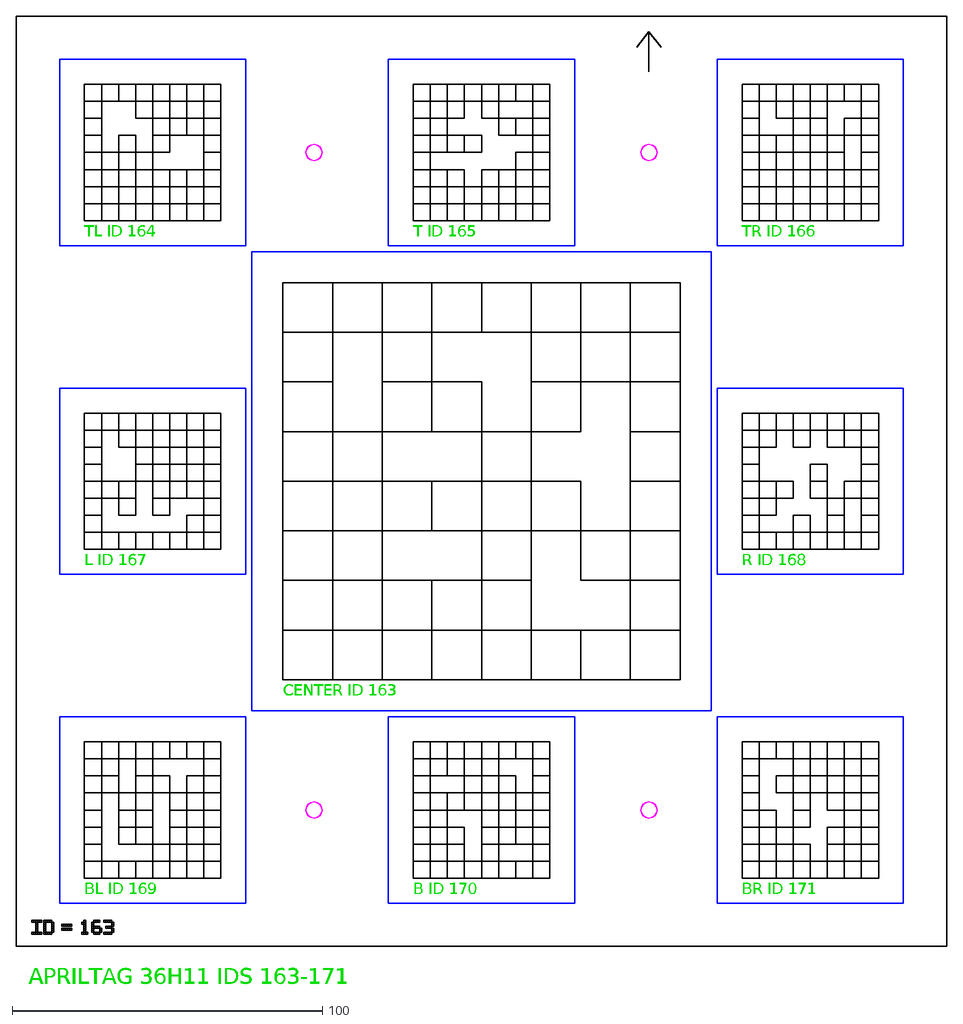
[picture p105: CAD file, 2026-08-25]
Reservoir-AprilTag-Boards-20/generated/board_08_ids_163-171_guide.dxf
CENTER ID 163
TL ID 164
T ID 165
TR ID 166
L ID 167
R ID 168
BL ID 169
B ID 170
BR ID 171
APRILTAG 36H11 IDS 163-171
