ShenYuan-sean/Underwater-AprilTag-Board/Reservoir-AprilTag-Boards-20/generated/boards/board_07_ids_154-162.dxf

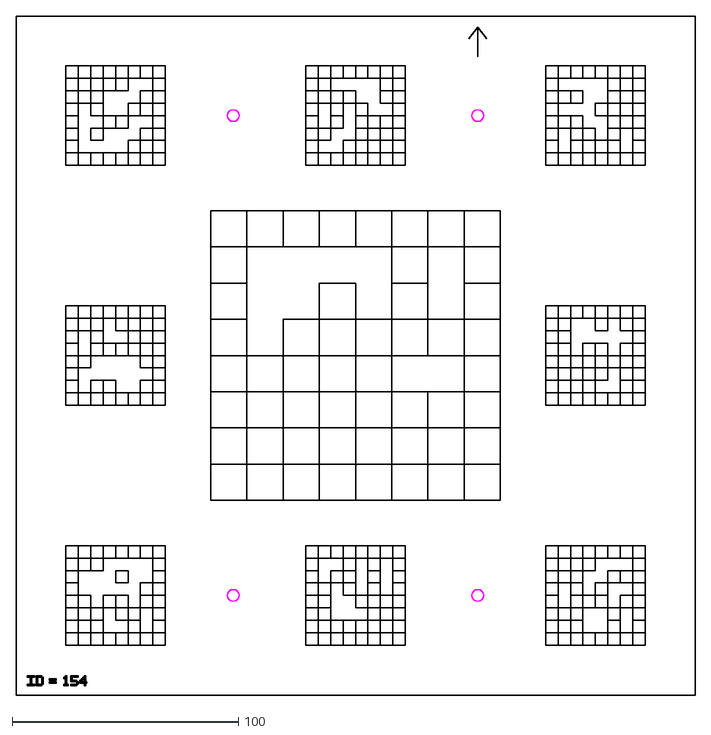
[picture p106: CAD file, 2026-08-25]
Reservoir-AprilTag-Boards-20/generated/boards/board_07_ids_154-162.dxf
300.0 x 300.0
