ShenYuan-sean/Underwater-AprilTag-Board/generated/face_06_guide.dxf

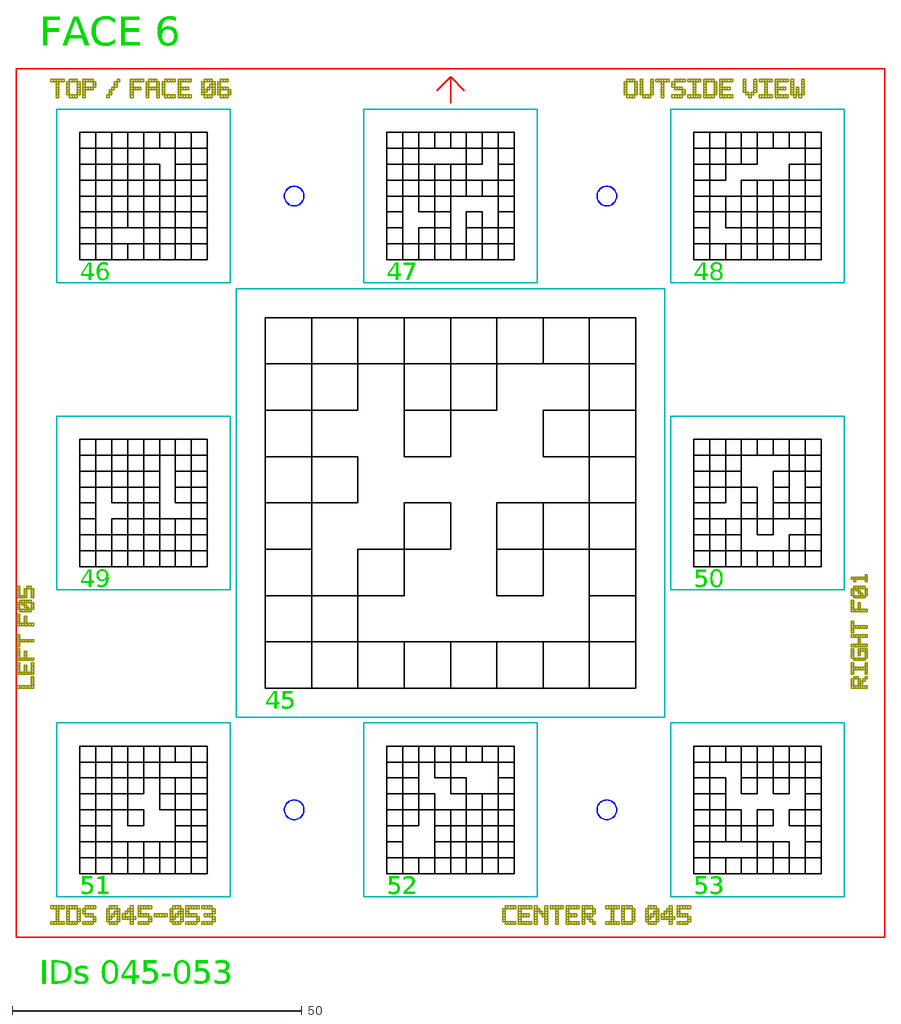
[picture p107: CAD file, 2026-08-11]
generated/face_06_guide.dxf
FACE 6
IDs 045-053
45
46
47
48
49
50
51
52
53
