ShenYuan-sean/Underwater-AprilTag-Board/Reservoir-AprilTag-Boards-20/batch_02/generated/board_33_ids_388-396.dxf

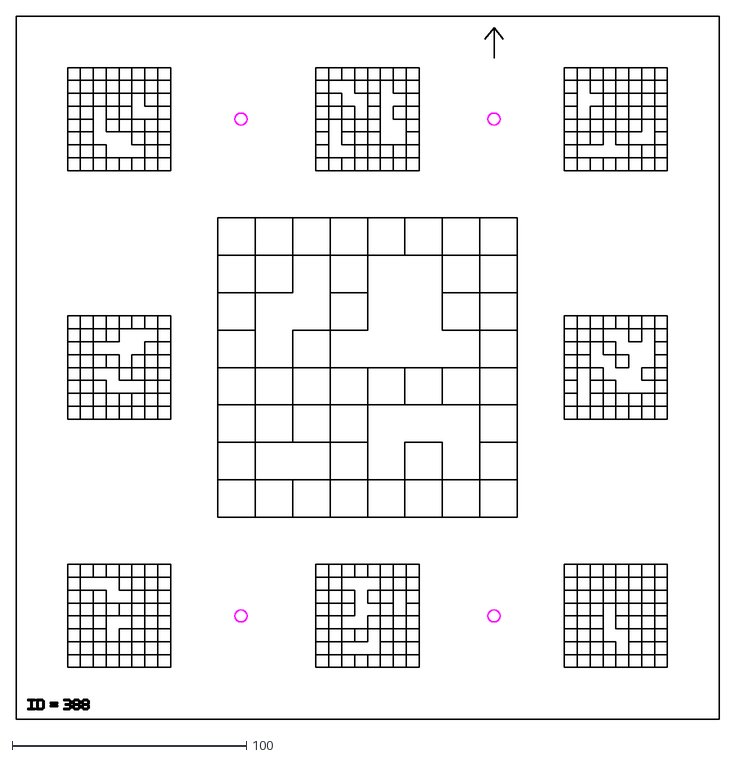
[picture p108: CAD file, 2026-10-02]
Reservoir-AprilTag-Boards-20/batch_02/generated/board_33_ids_388-396.dxf
300.0 x 300.0
