ShenYuan-sean/Underwater-AprilTag-Board/Reservoir-AprilTag-Boards-20/generated/board_16_ids_235-243_guide.dxf

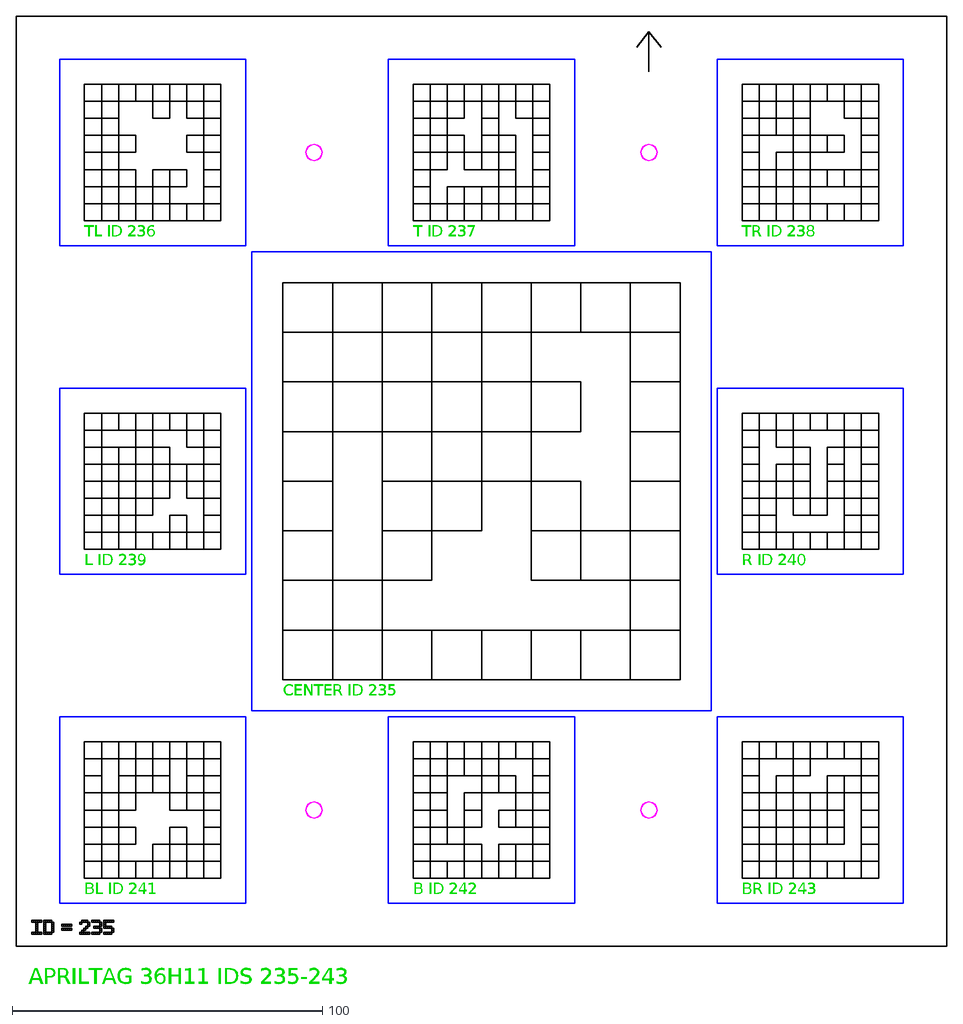
[picture p110: CAD file, 2026-08-25]
Reservoir-AprilTag-Boards-20/generated/board_16_ids_235-243_guide.dxf
CENTER ID 235
TL ID 236
T ID 237
TR ID 238
L ID 239
R ID 240
BL ID 241
B ID 242
BR ID 243
APRILTAG 36H11 IDS 235-243
