ShenYuan-sean/Underwater-AprilTag-Board/generated/face_03.dxf

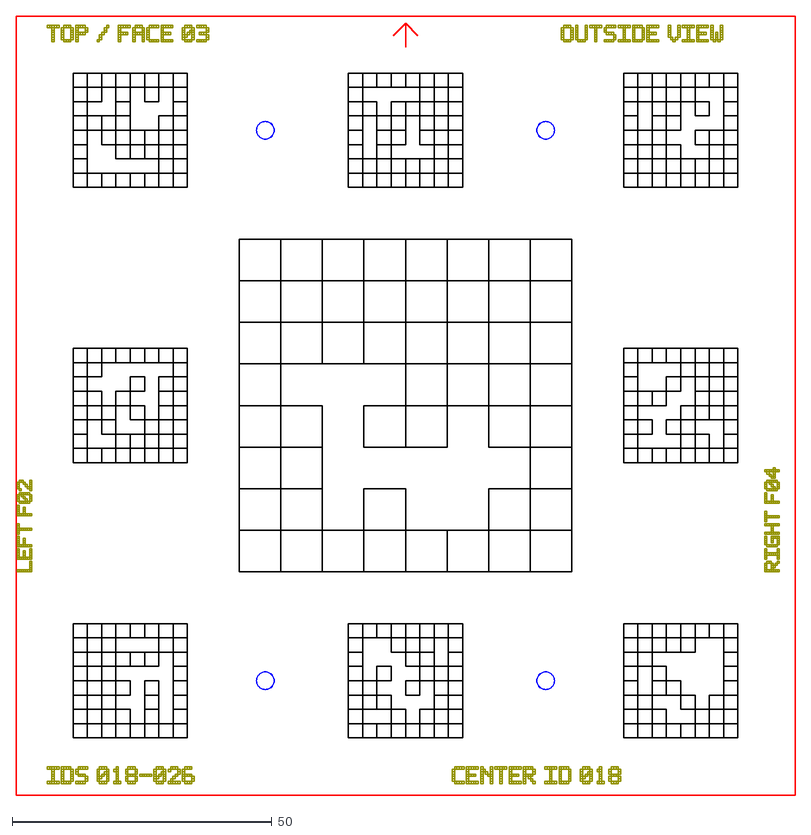
[picture p111: CAD file, 2026-08-11]
generated/face_03.dxf
150.0 x 150.0
