ShenYuan-sean/Underwater-AprilTag-Board/Reservoir-AprilTag-Boards-20/batch_02/generated/board_33_ids_388-396_guide.dxf

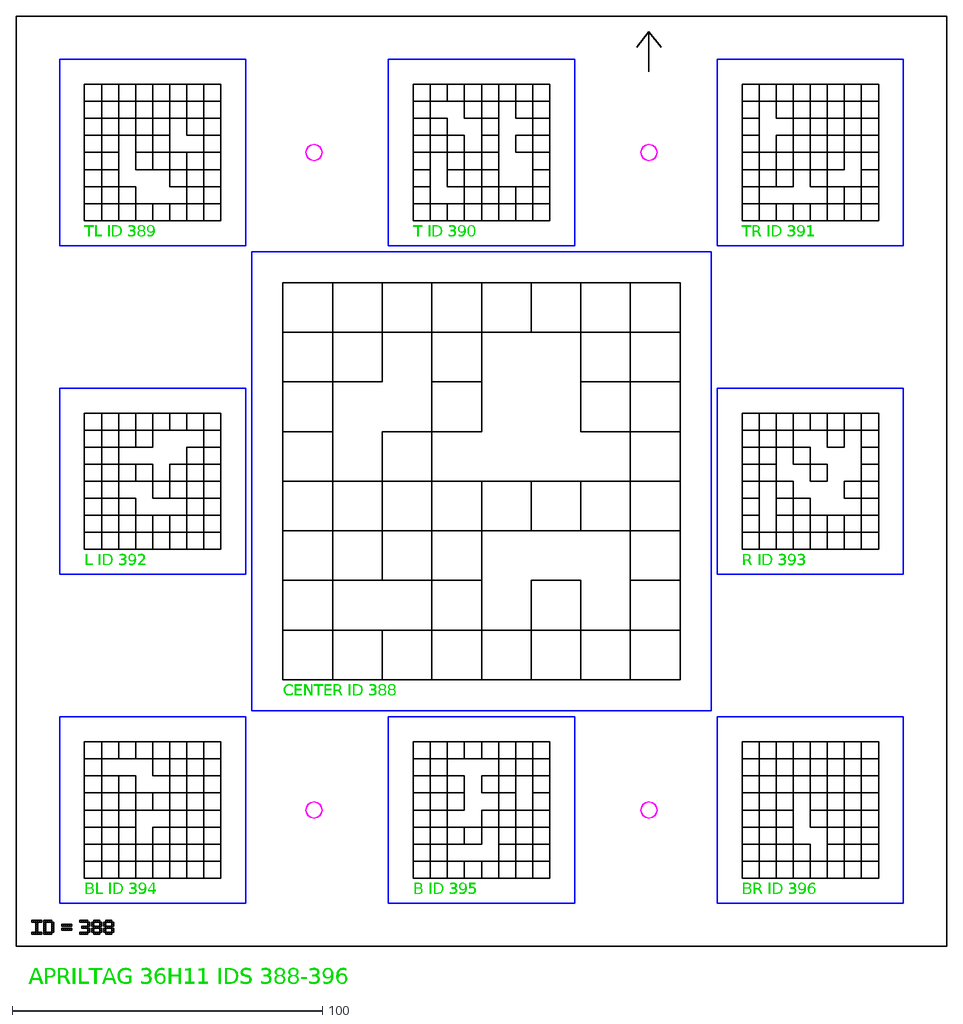
[picture p112: CAD file, 2026-10-02]
Reservoir-AprilTag-Boards-20/batch_02/generated/board_33_ids_388-396_guide.dxf
CENTER ID 388
TL ID 389
T ID 390
TR ID 391
L ID 392
R ID 393
BL ID 394
B ID 395
BR ID 396
APRILTAG 36H11 IDS 388-396
