ShenYuan-sean/Underwater-AprilTag-Board/Reservoir-AprilTag-Boards-20/generated/board_02_ids_109-117_guide.dxf

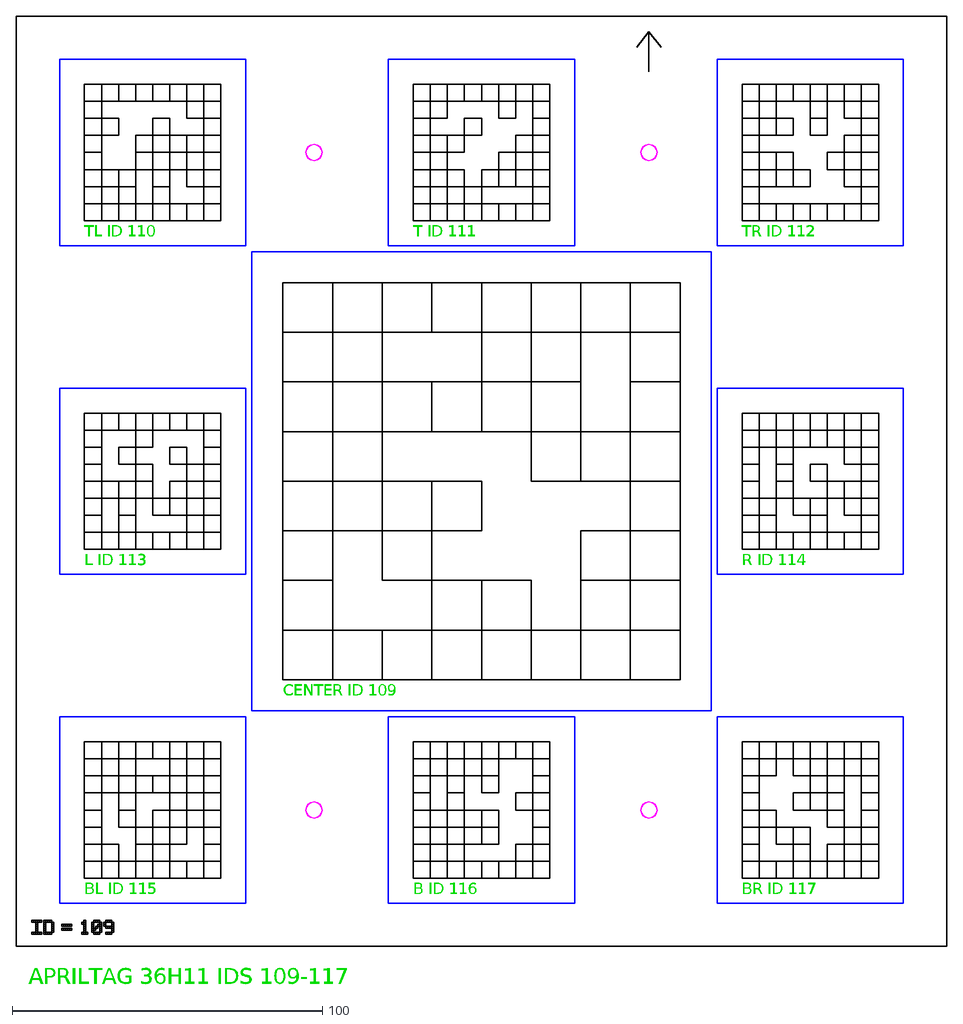
[picture p114: CAD file, 2026-08-25]
Reservoir-AprilTag-Boards-20/generated/board_02_ids_109-117_guide.dxf
CENTER ID 109
TL ID 110
T ID 111
TR ID 112
L ID 113
R ID 114
BL ID 115
B ID 116
BR ID 117
APRILTAG 36H11 IDS 109-117
