ShenYuan-sean/Underwater-AprilTag-Board/Reservoir-AprilTag-Boards-20/generated/boards/board_09_ids_172-180.dxf

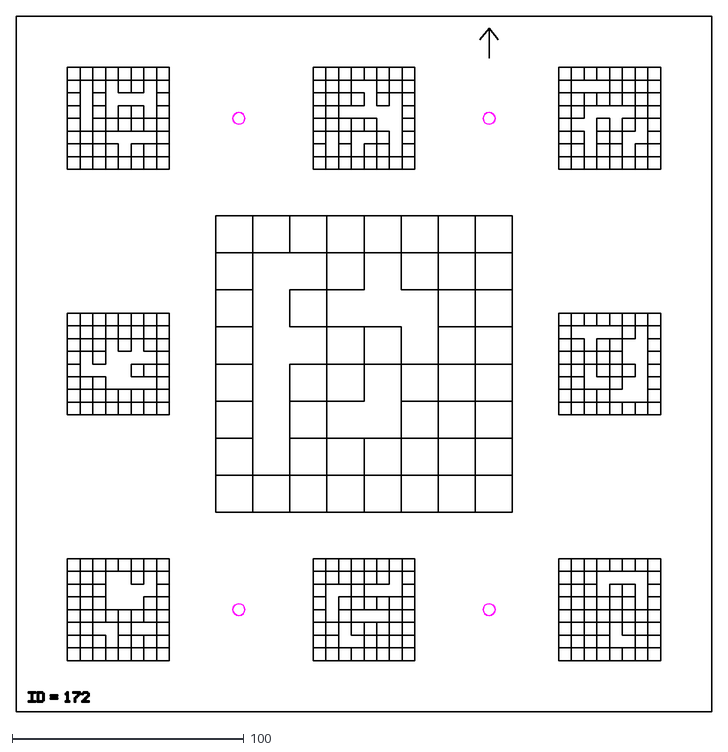
[picture p115: CAD file, 2026-08-25]
Reservoir-AprilTag-Boards-20/generated/boards/board_09_ids_172-180.dxf
300.0 x 300.0
