ShenYuan-sean/Underwater-AprilTag-Board/generated/face_05.dxf

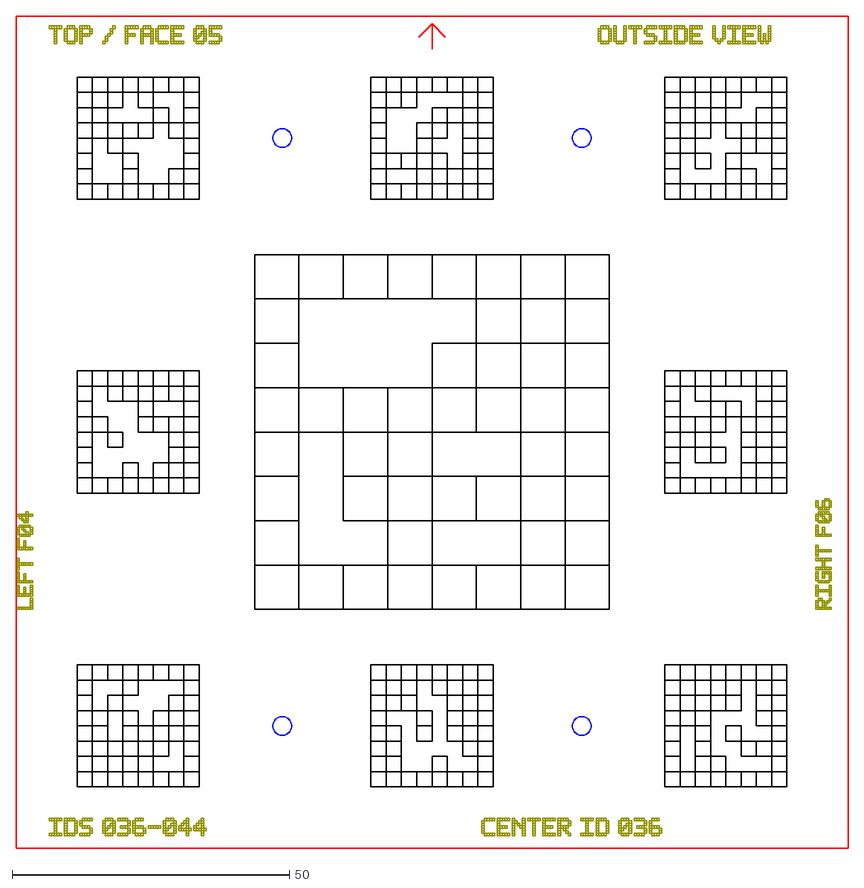
[picture p116: CAD file, 2026-08-11]
generated/face_05.dxf
150.0 x 150.0
