ShenYuan-sean/Underwater-AprilTag-Board/Reservoir-AprilTag-Boards-20/batch_02/generated/board_28_ids_343-351_guide.dxf

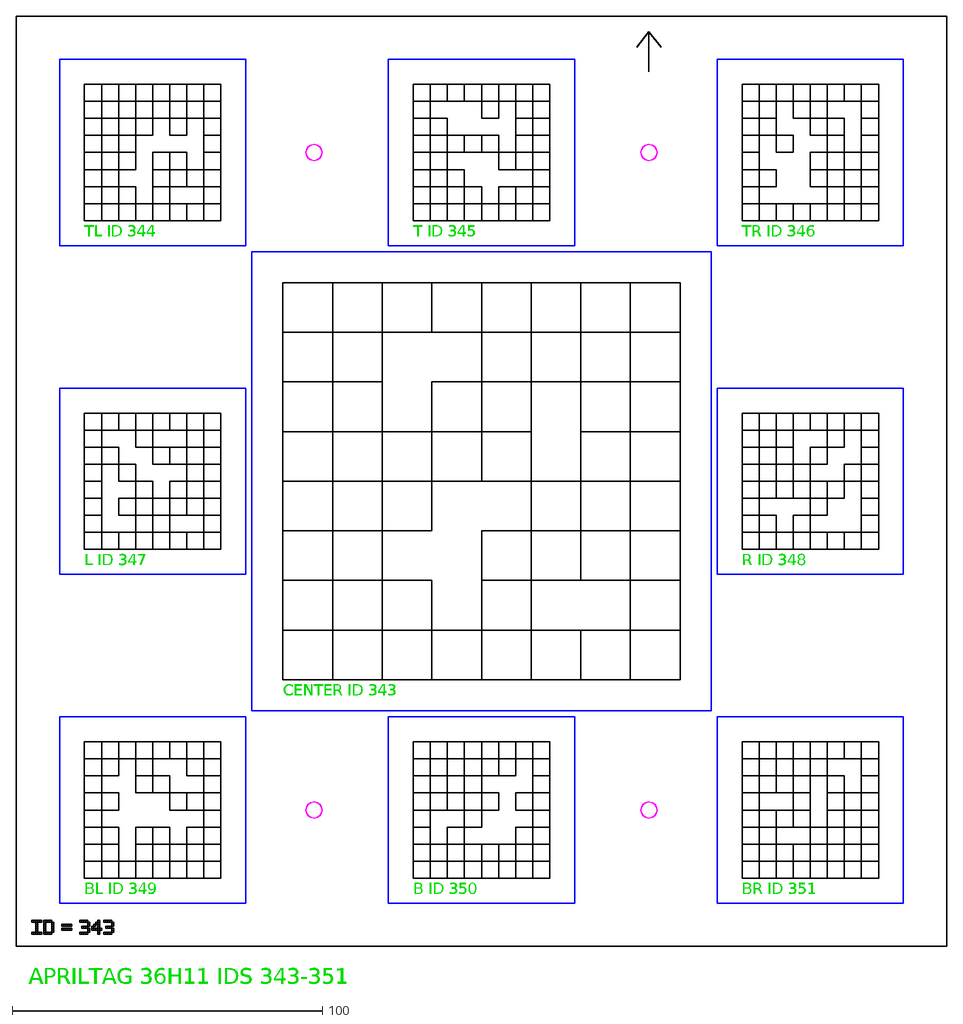
[picture p117: CAD file, 2026-10-02]
Reservoir-AprilTag-Boards-20/batch_02/generated/board_28_ids_343-351_guide.dxf
CENTER ID 343
TL ID 344
T ID 345
TR ID 346
L ID 347
R ID 348
BL ID 349
B ID 350
BR ID 351
APRILTAG 36H11 IDS 343-351
