ShenYuan-sean/Underwater-AprilTag-Board/Reservoir-AprilTag-Boards-20/generated/boards/board_14_ids_217-225.dxf

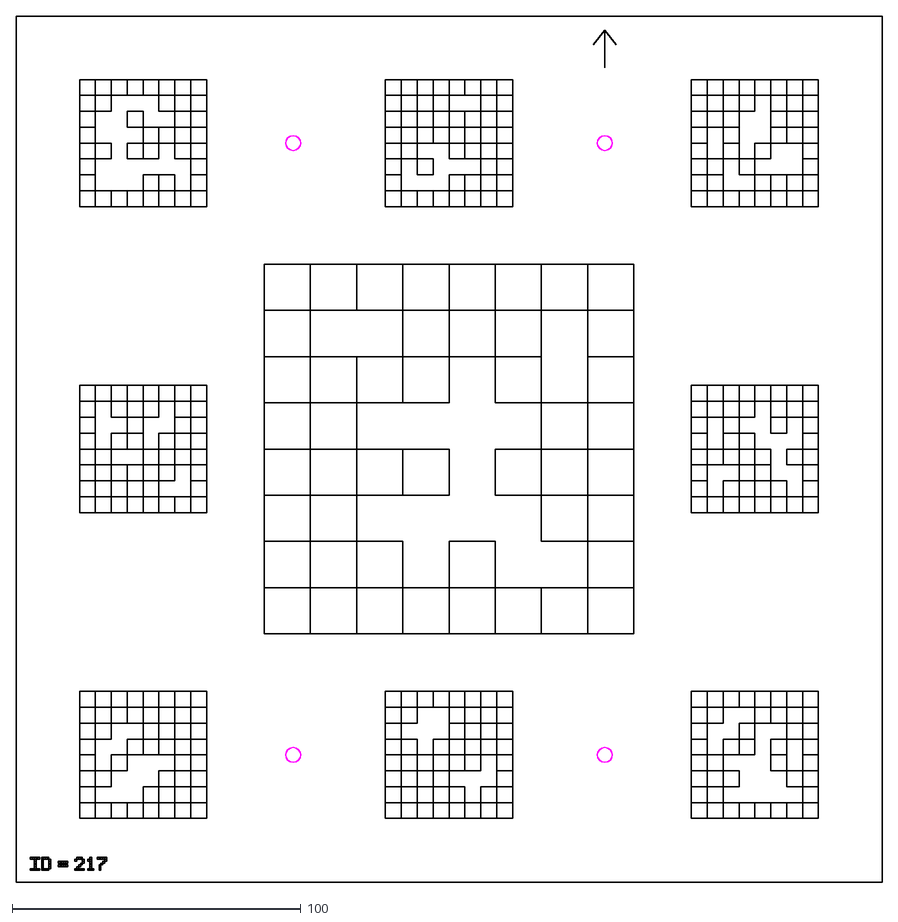
[picture p119: CAD file, 2026-08-25]
Reservoir-AprilTag-Boards-20/generated/boards/board_14_ids_217-225.dxf
300.0 x 300.0
