ShenYuan-sean/Underwater-AprilTag-Board/generated/face_02.dxf

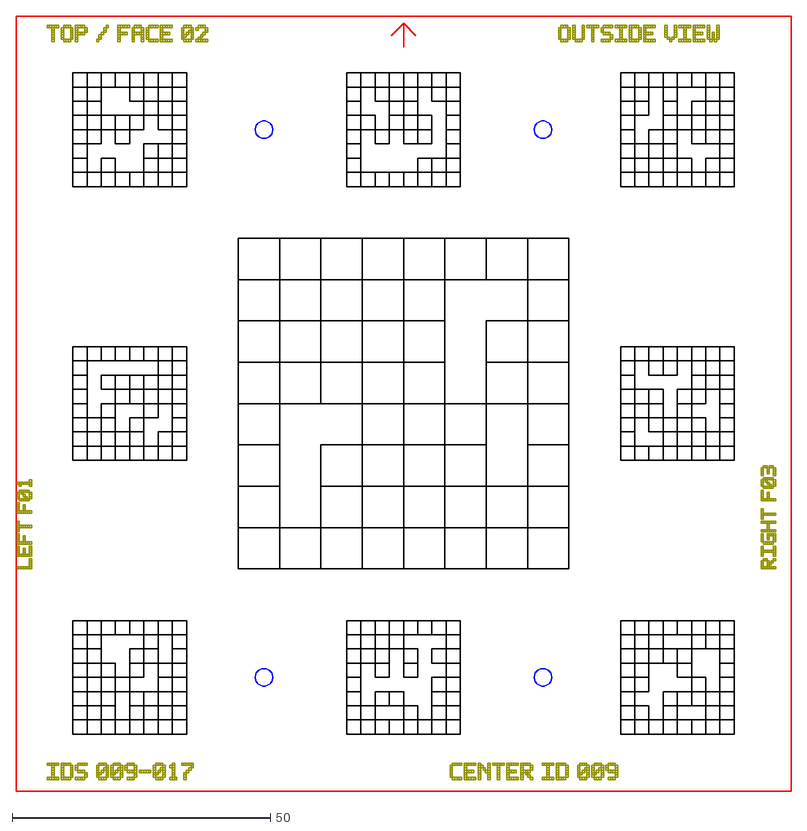
[picture p120: CAD file, 2026-08-11]
generated/face_02.dxf
150.0 x 150.0
