ShenYuan-sean/Underwater-AprilTag-Board/Reservoir-AprilTag-Boards-20/batch_02/generated/board_25_ids_316-324_guide.dxf

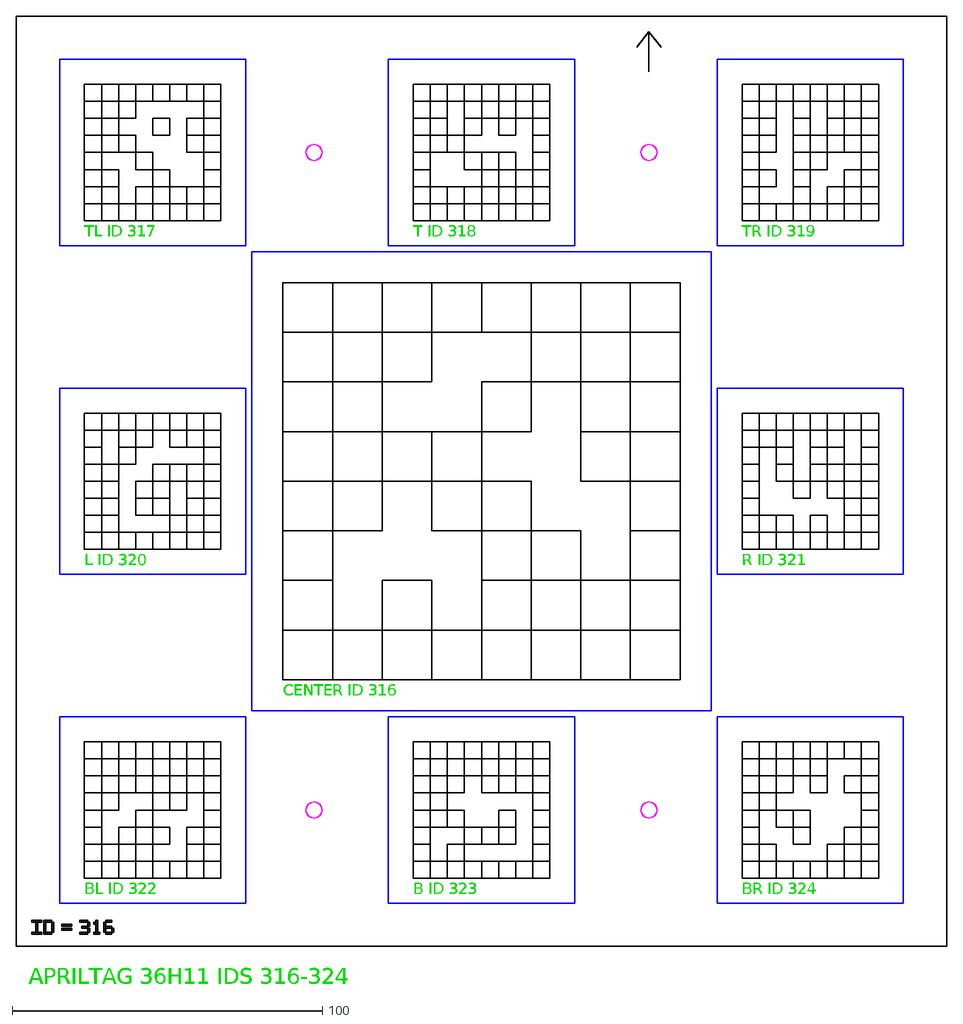
[picture p121: CAD file, 2026-10-02]
Reservoir-AprilTag-Boards-20/batch_02/generated/board_25_ids_316-324_guide.dxf
CENTER ID 316
TL ID 317
T ID 318
TR ID 319
L ID 320
R ID 321
BL ID 322
B ID 323
BR ID 324
APRILTAG 36H11 IDS 316-324
