ShenYuan-sean/Underwater-AprilTag-Board/Reservoir-AprilTag-Boards-20/generated/board_15_ids_226-234_guide.dxf

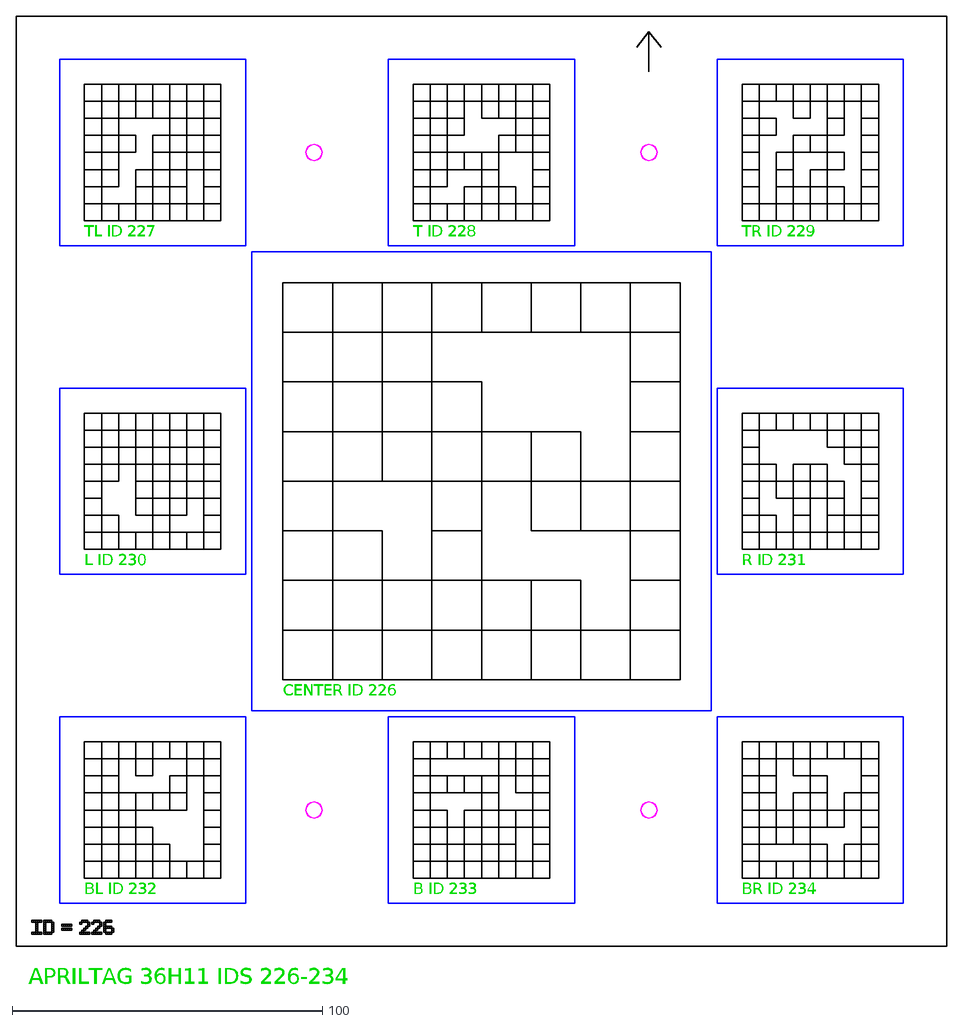
[picture p122: CAD file, 2026-08-25]
Reservoir-AprilTag-Boards-20/generated/board_15_ids_226-234_guide.dxf
CENTER ID 226
TL ID 227
T ID 228
TR ID 229
L ID 230
R ID 231
BL ID 232
B ID 233
BR ID 234
APRILTAG 36H11 IDS 226-234
