ShenYuan-sean/Underwater-AprilTag-Board/Reservoir-AprilTag-Boards-20/generated/boards/board_08_ids_163-171.dxf

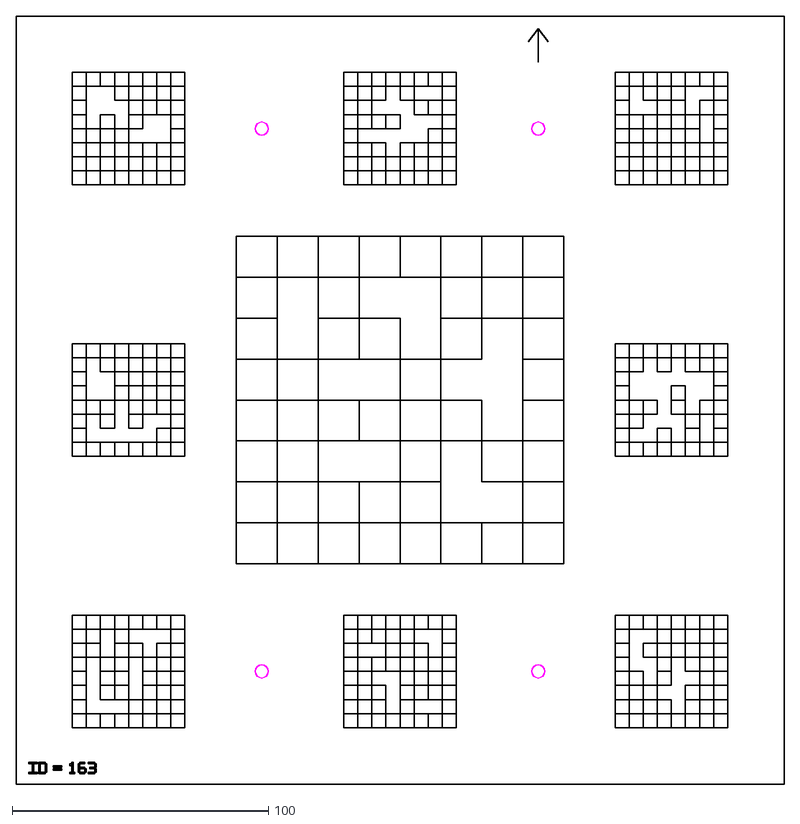
[picture p123: CAD file, 2026-08-25]
Reservoir-AprilTag-Boards-20/generated/boards/board_08_ids_163-171.dxf
300.0 x 300.0
