ShenYuan-sean/Underwater-AprilTag-Board/Reservoir-AprilTag-Boards-20/batch_02/generated/board_29_ids_352-360_guide.dxf

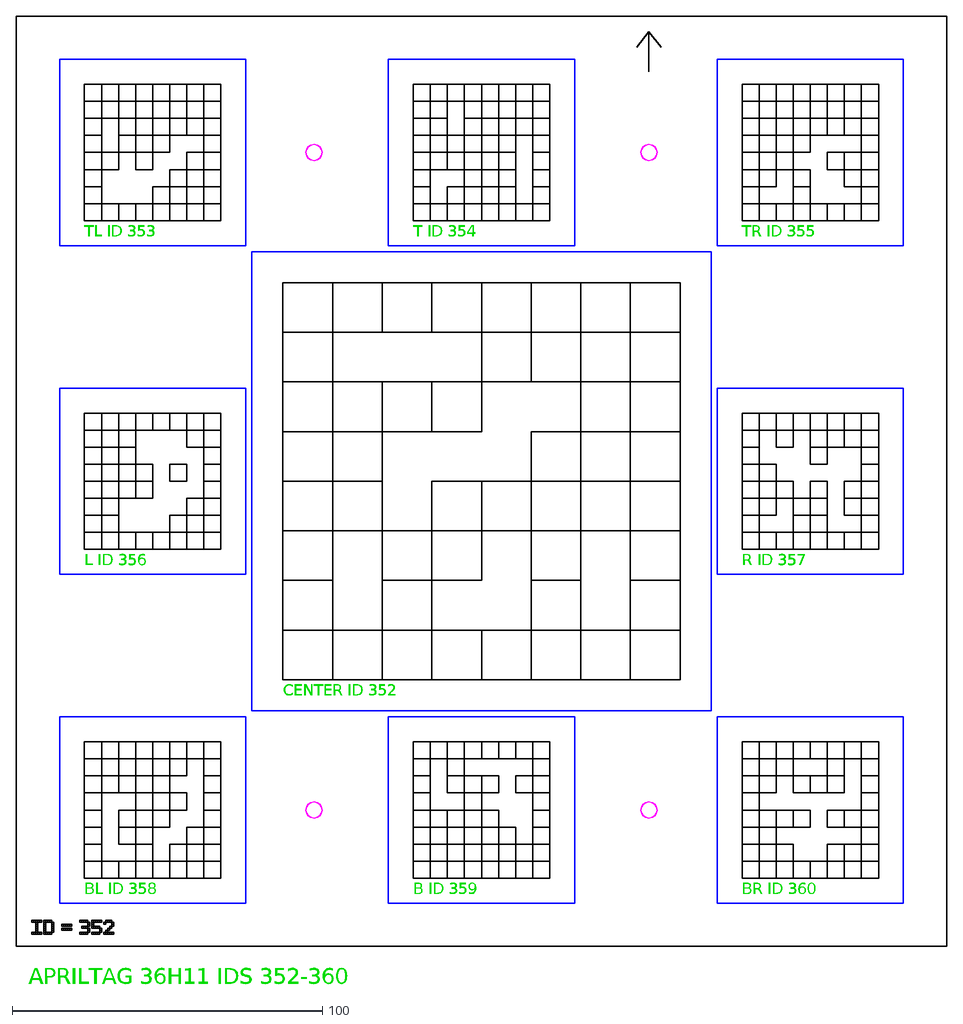
[picture p124: CAD file, 2026-10-02]
Reservoir-AprilTag-Boards-20/batch_02/generated/board_29_ids_352-360_guide.dxf
CENTER ID 352
TL ID 353
T ID 354
TR ID 355
L ID 356
R ID 357
BL ID 358
B ID 359
BR ID 360
APRILTAG 36H11 IDS 352-360
