ShenYuan-sean/Underwater-AprilTag-Board/Reservoir-AprilTag-Boards-20/generated/board_01_ids_100-108_guide.dxf

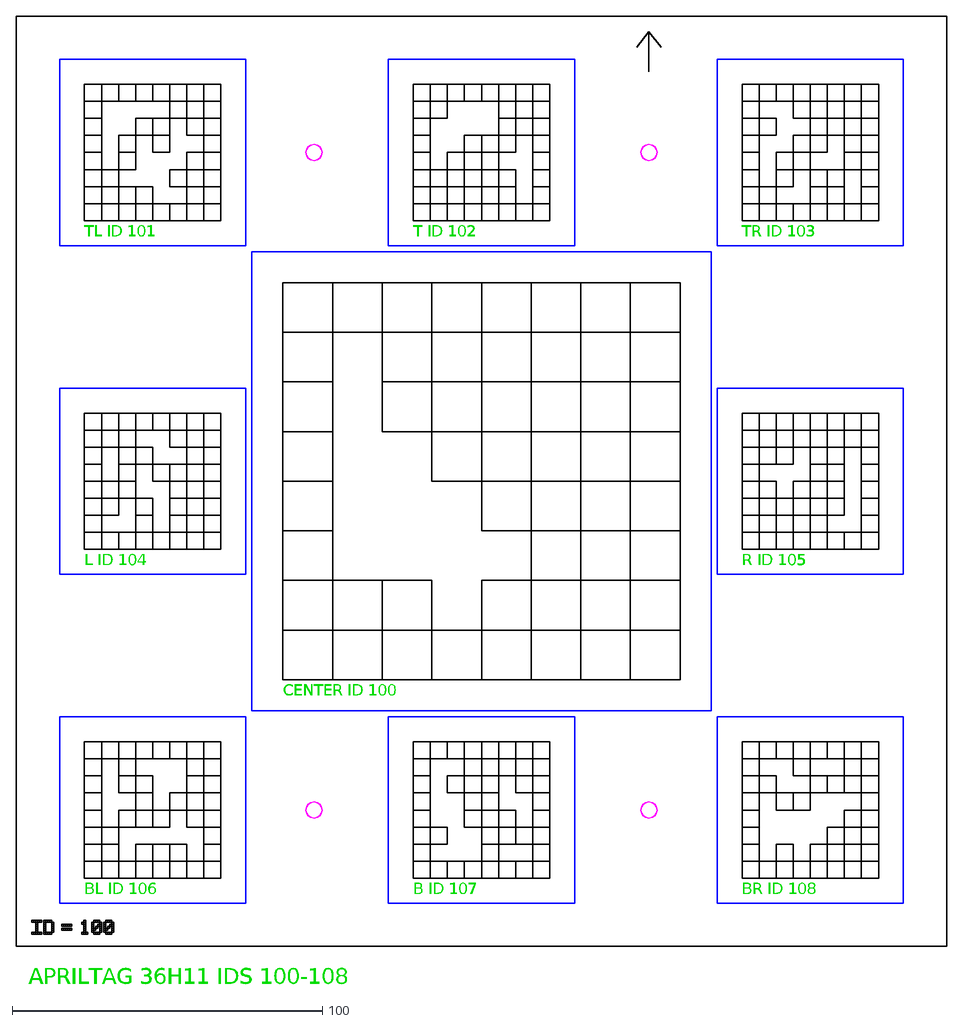
[picture p126: CAD file, 2026-08-25]
Reservoir-AprilTag-Boards-20/generated/board_01_ids_100-108_guide.dxf
CENTER ID 100
TL ID 101
T ID 102
TR ID 103
L ID 104
R ID 105
BL ID 106
B ID 107
BR ID 108
APRILTAG 36H11 IDS 100-108
