ShenYuan-sean/Underwater-AprilTag-Board/Reservoir-AprilTag-Boards-20/generated/boards/board_10_ids_181-189.dxf

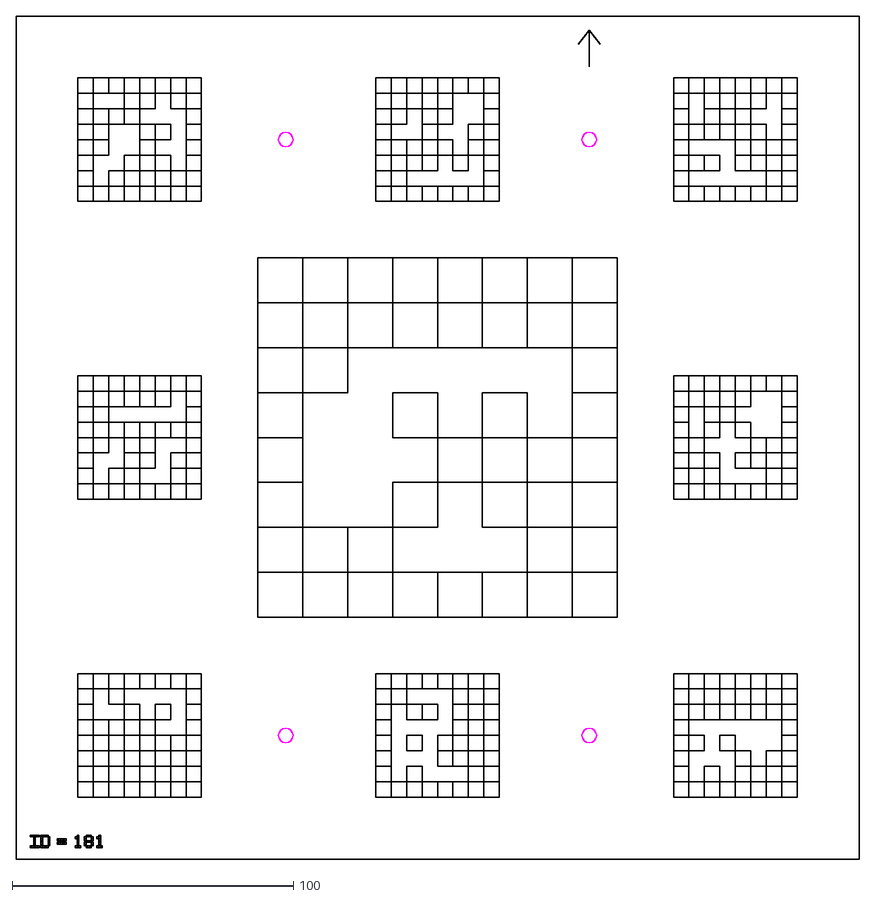
[picture p127: CAD file, 2026-08-25]
Reservoir-AprilTag-Boards-20/generated/boards/board_10_ids_181-189.dxf
300.0 x 300.0
