ShenYuan-sean/Underwater-AprilTag-Board/Reservoir-AprilTag-Boards-20/batch_02/generated/board_37_ids_424-432_guide.dxf

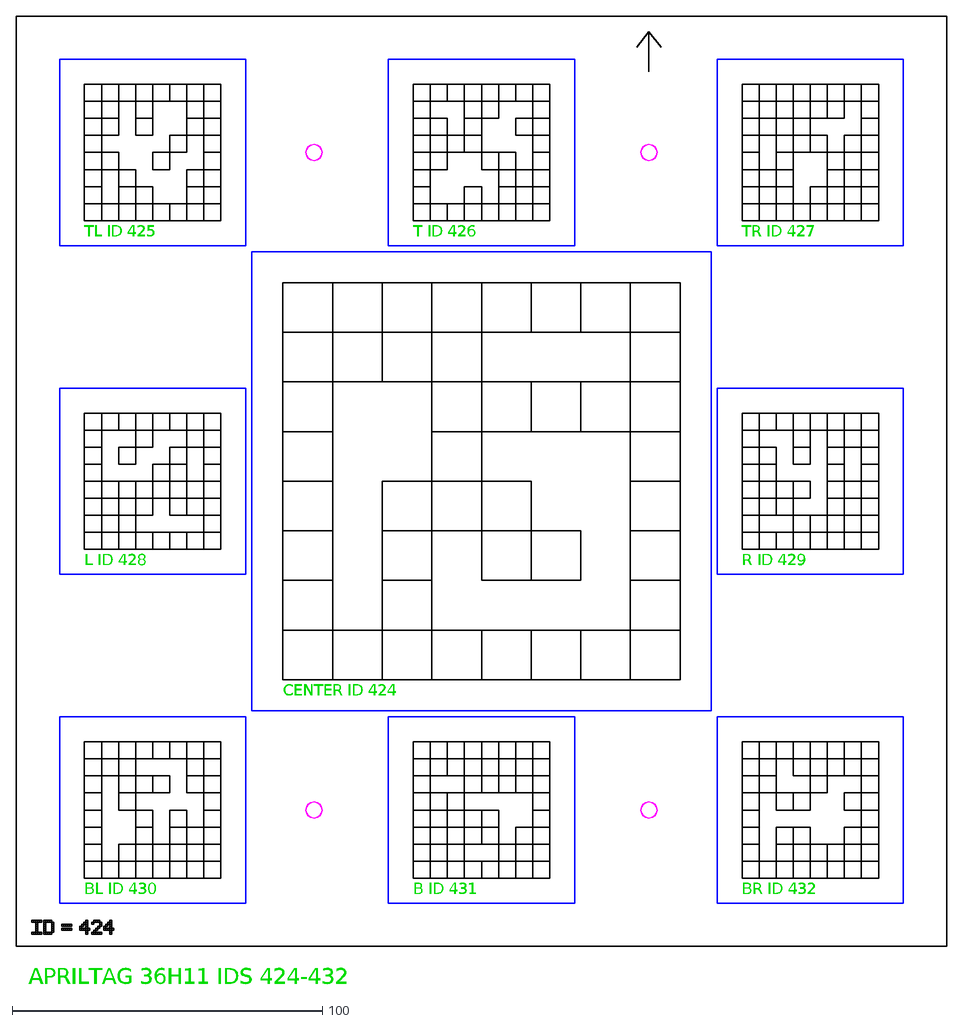
[picture p128: CAD file, 2026-10-02]
Reservoir-AprilTag-Boards-20/batch_02/generated/board_37_ids_424-432_guide.dxf
CENTER ID 424
TL ID 425
T ID 426
TR ID 427
L ID 428
R ID 429
BL ID 430
B ID 431
BR ID 432
APRILTAG 36H11 IDS 424-432
