ShenYuan-sean/Underwater-AprilTag-Board/Reservoir-AprilTag-Boards-20/generated/board_17_ids_244-252.dxf

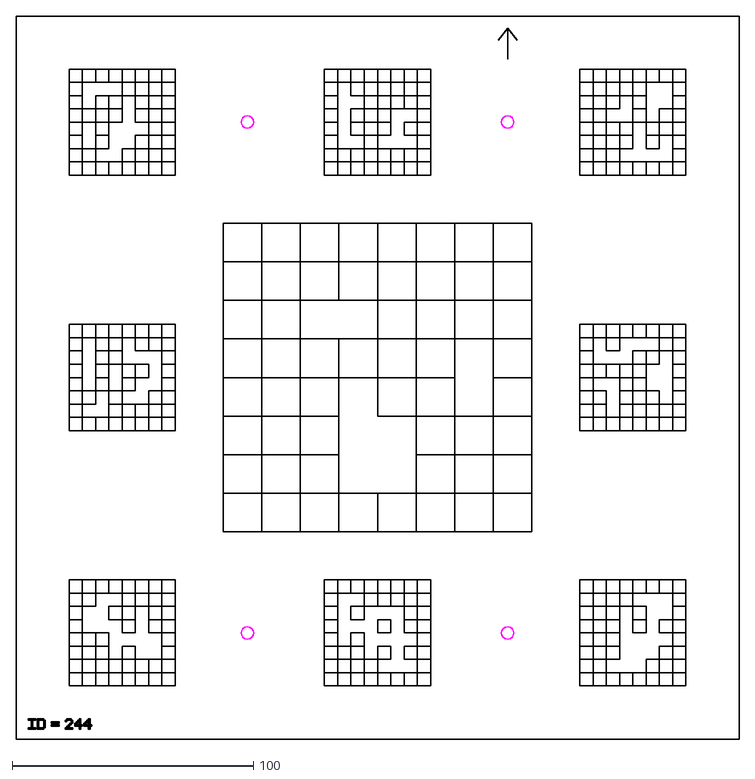
[picture p130: CAD file, 2026-08-25]
Reservoir-AprilTag-Boards-20/generated/board_17_ids_244-252.dxf
300.0 x 300.0
