ShenYuan-sean/Underwater-AprilTag-Board/Reservoir-AprilTag-Boards-20/generated/boards/board_02_ids_109-117.dxf

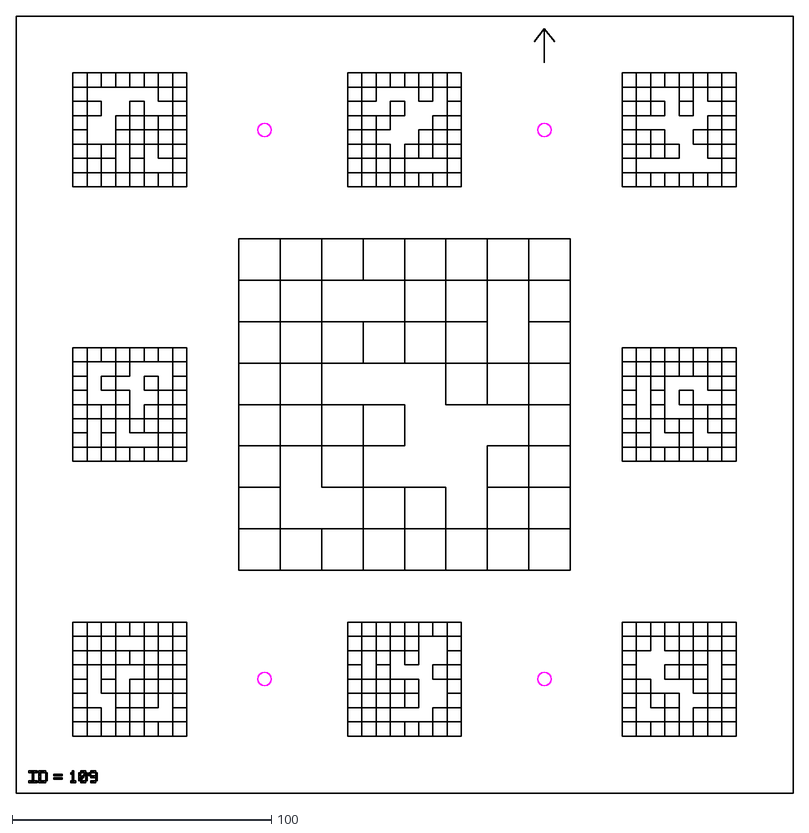
[picture p131: CAD file, 2026-08-25]
Reservoir-AprilTag-Boards-20/generated/boards/board_02_ids_109-117.dxf
300.0 x 300.0
