ShenYuan-sean/Underwater-AprilTag-Board/Reservoir-AprilTag-Boards-20/generated/board_03_ids_118-126_guide.dxf

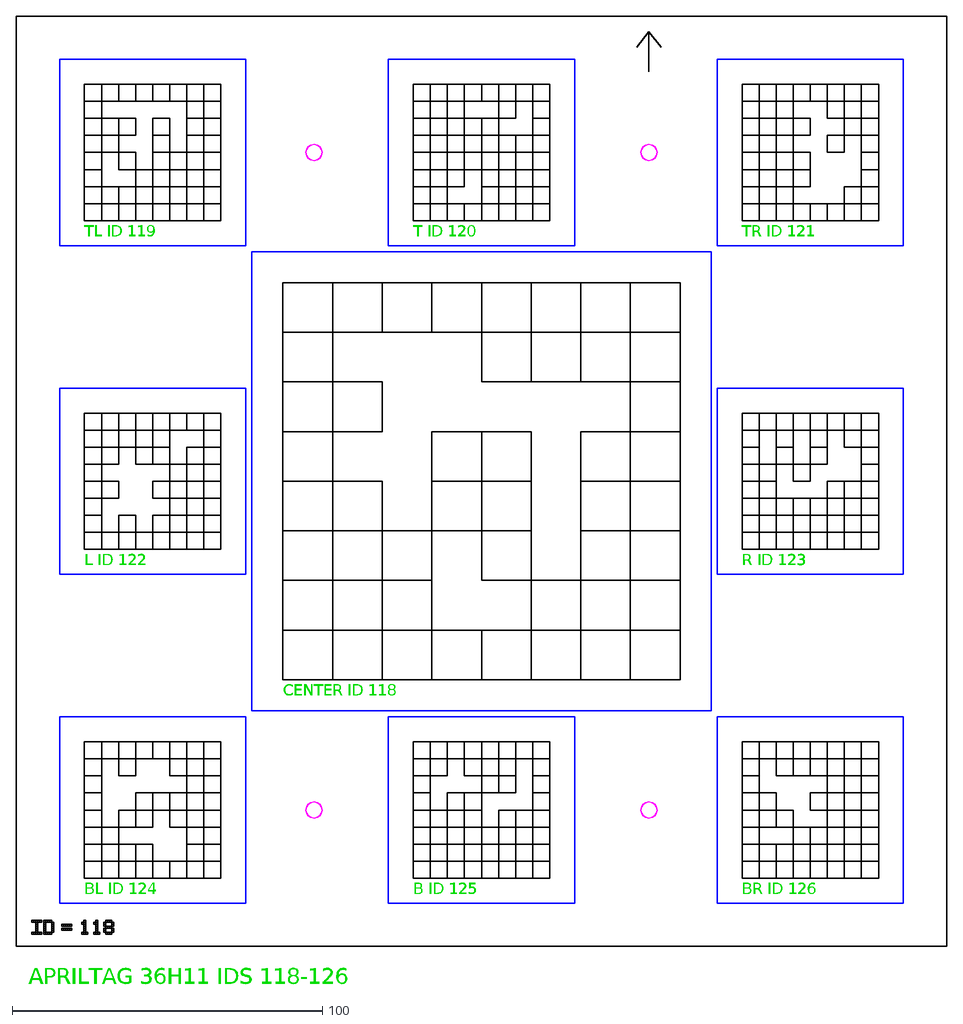
[picture p132: CAD file, 2026-08-25]
Reservoir-AprilTag-Boards-20/generated/board_03_ids_118-126_guide.dxf
CENTER ID 118
TL ID 119
T ID 120
TR ID 121
L ID 122
R ID 123
BL ID 124
B ID 125
BR ID 126
APRILTAG 36H11 IDS 118-126
