ShenYuan-sean/Underwater-AprilTag-Board/Reservoir-AprilTag-Boards-20/batch_02/generated/board_27_ids_334-342_guide.dxf

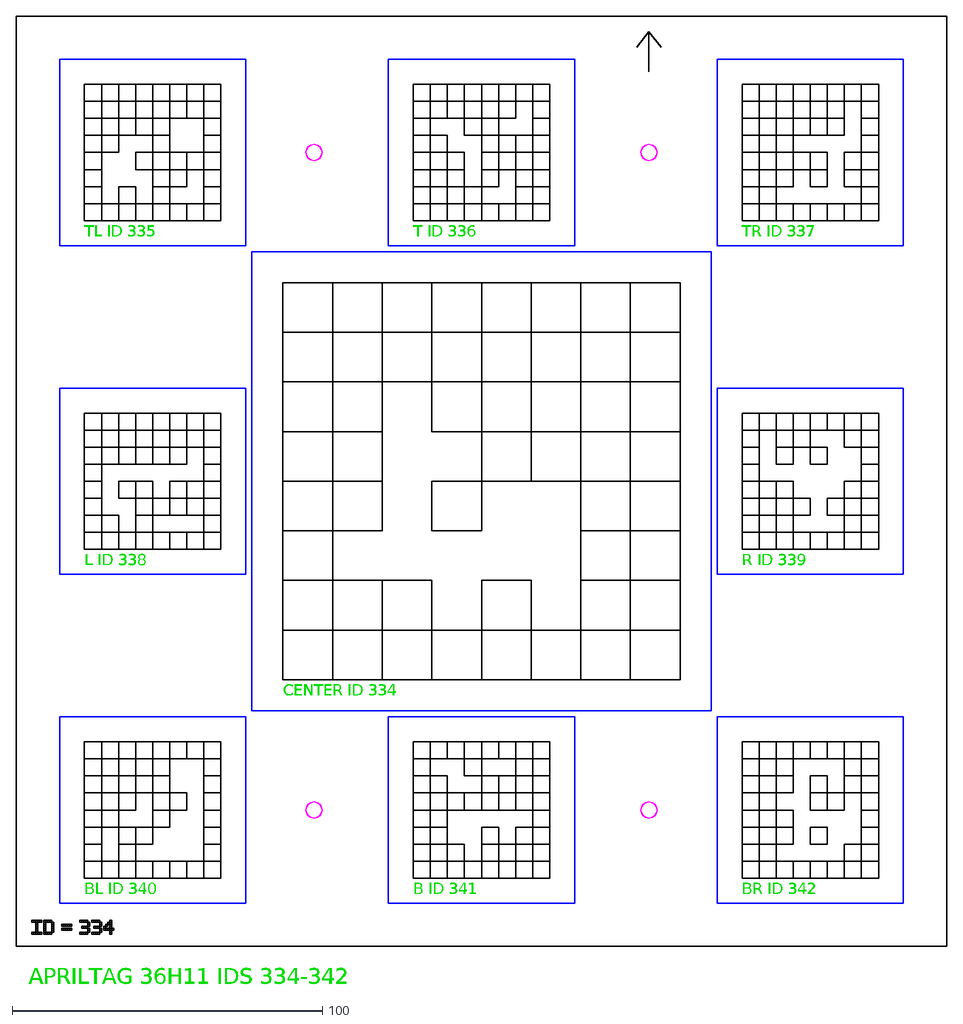
[picture p133: CAD file, 2026-10-02]
Reservoir-AprilTag-Boards-20/batch_02/generated/board_27_ids_334-342_guide.dxf
CENTER ID 334
TL ID 335
T ID 336
TR ID 337
L ID 338
R ID 339
BL ID 340
B ID 341
BR ID 342
APRILTAG 36H11 IDS 334-342
