ShenYuan-sean/Underwater-AprilTag-Board/Reservoir-AprilTag-Boards-20/generated/board_13_ids_208-216_guide.dxf

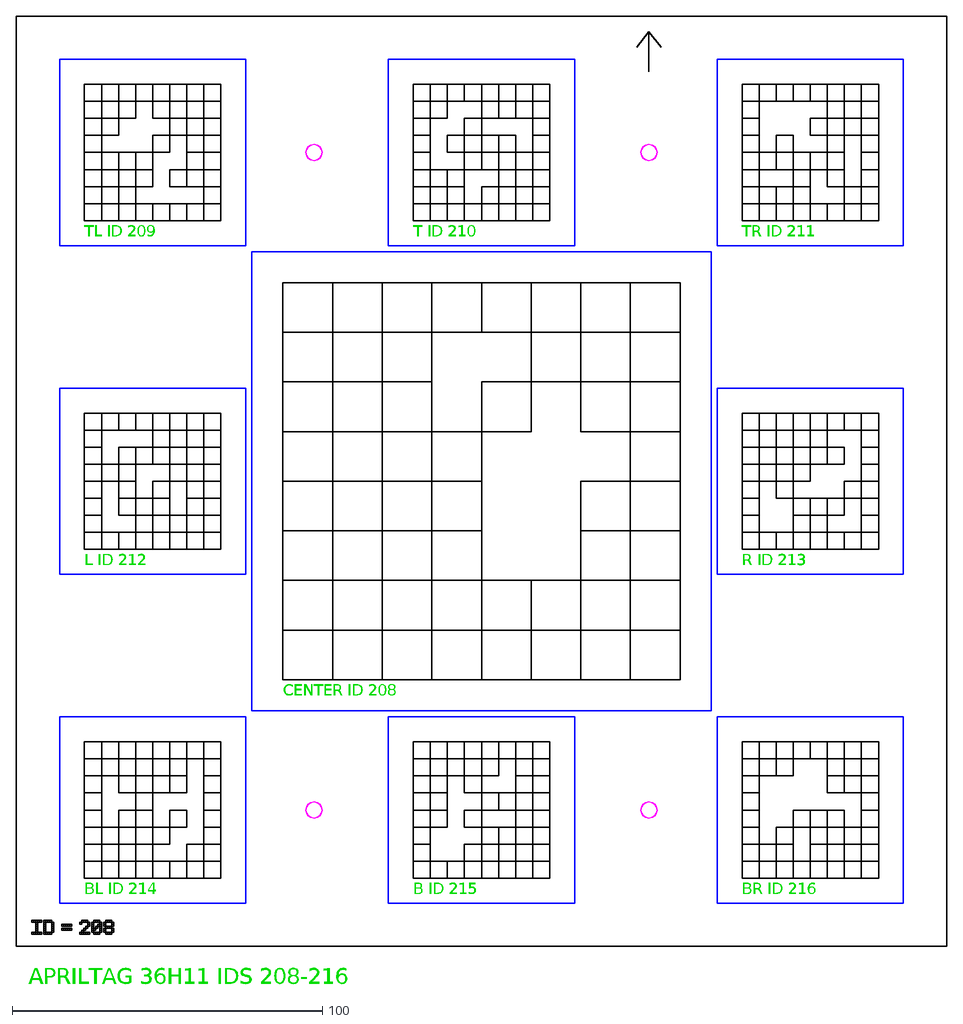
[picture p135: CAD file, 2026-08-25]
Reservoir-AprilTag-Boards-20/generated/board_13_ids_208-216_guide.dxf
CENTER ID 208
TL ID 209
T ID 210
TR ID 211
L ID 212
R ID 213
BL ID 214
B ID 215
BR ID 216
APRILTAG 36H11 IDS 208-216
