ShenYuan-sean/Underwater-AprilTag-Board/Reservoir-AprilTag-Boards-20/generated/boards/board_03_ids_118-126.dxf

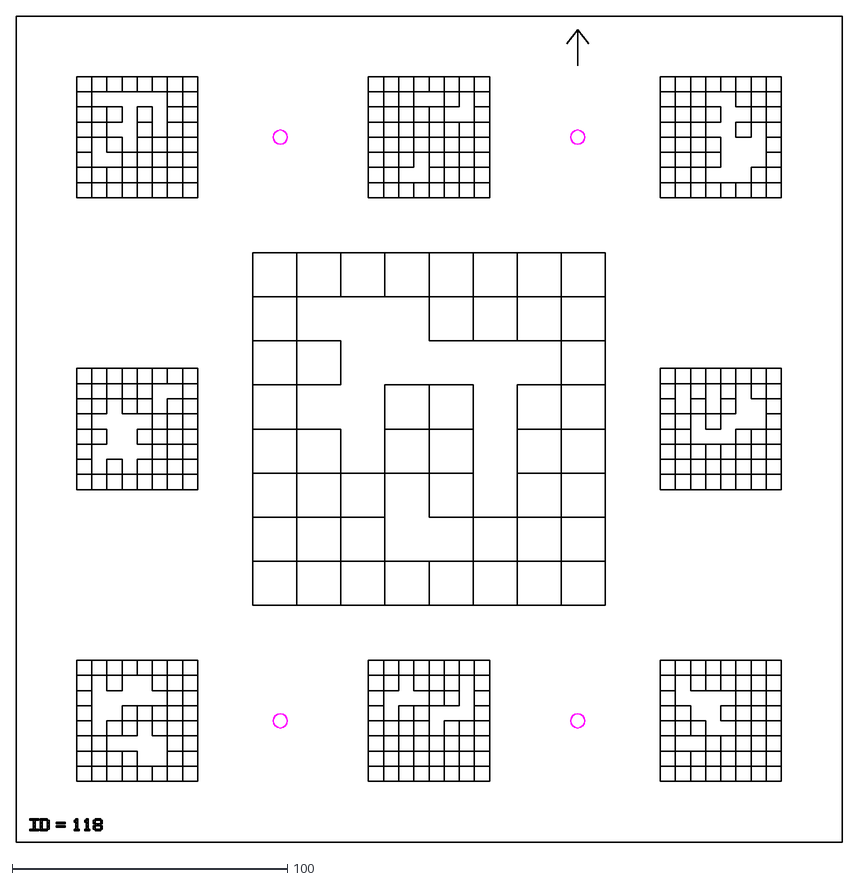
[picture p136: CAD file, 2026-08-25]
Reservoir-AprilTag-Boards-20/generated/boards/board_03_ids_118-126.dxf
300.0 x 300.0
