ShenYuan-sean/Underwater-AprilTag-Board/Reservoir-AprilTag-Boards-20/batch_02/generated/board_35_ids_406-414_guide.dxf

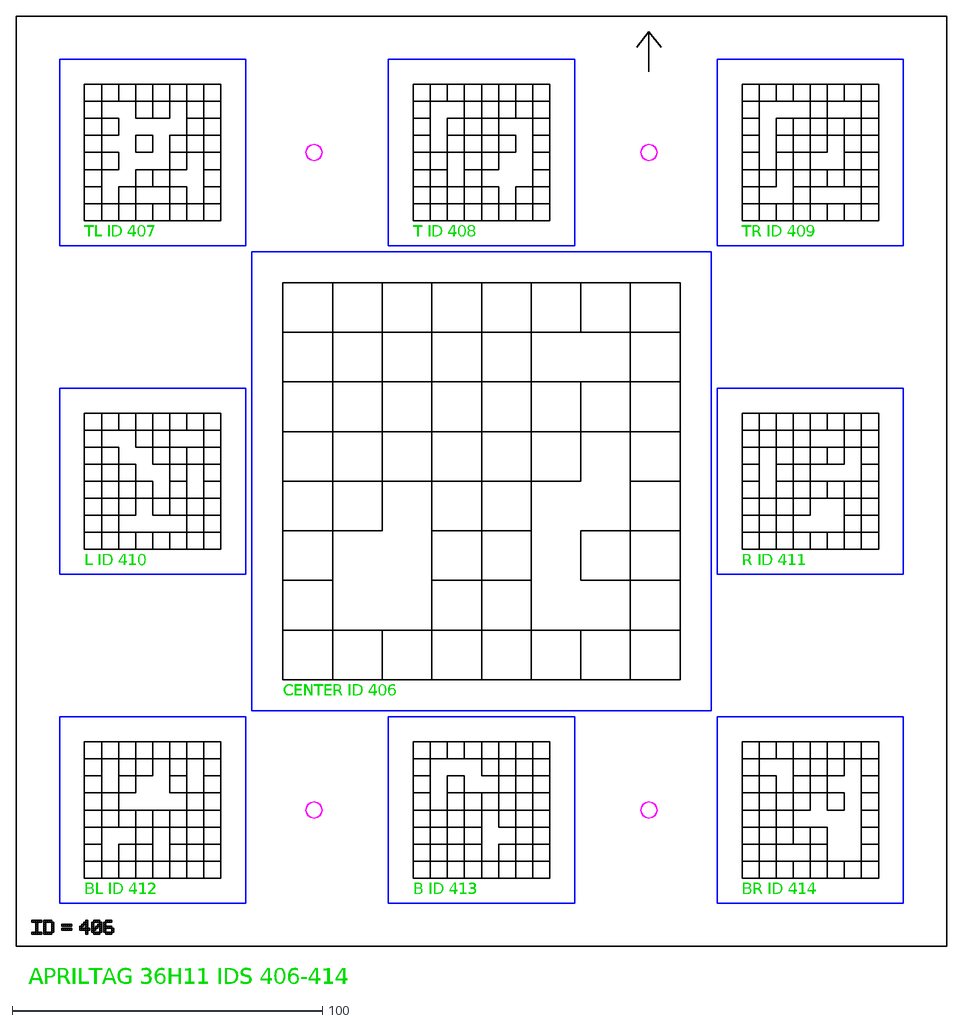
[picture p137: CAD file, 2026-10-02]
Reservoir-AprilTag-Boards-20/batch_02/generated/board_35_ids_406-414_guide.dxf
CENTER ID 406
TL ID 407
T ID 408
TR ID 409
L ID 410
R ID 411
BL ID 412
B ID 413
BR ID 414
APRILTAG 36H11 IDS 406-414
