ShenYuan-sean/Underwater-AprilTag-Board/Reservoir-AprilTag-Boards-20/batch_02/generated/all_boards_sheet.dxf

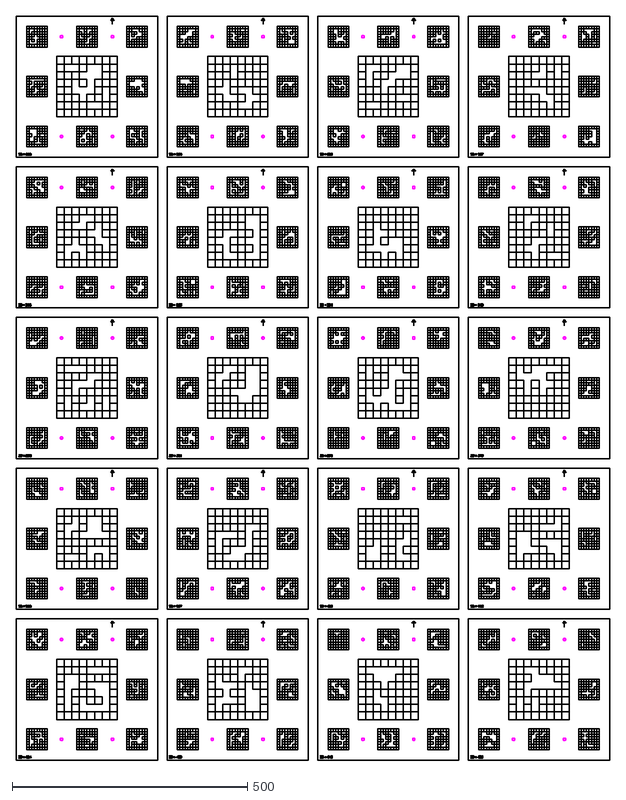
[picture p139: CAD file, 2026-10-02]
Reservoir-AprilTag-Boards-20/batch_02/generated/all_boards_sheet.dxf
1260.0 x 1580.0
