ShenYuan-sean/Underwater-AprilTag-Board/Reservoir-AprilTag-Boards-20/generated/all_boards_sheet.dxf

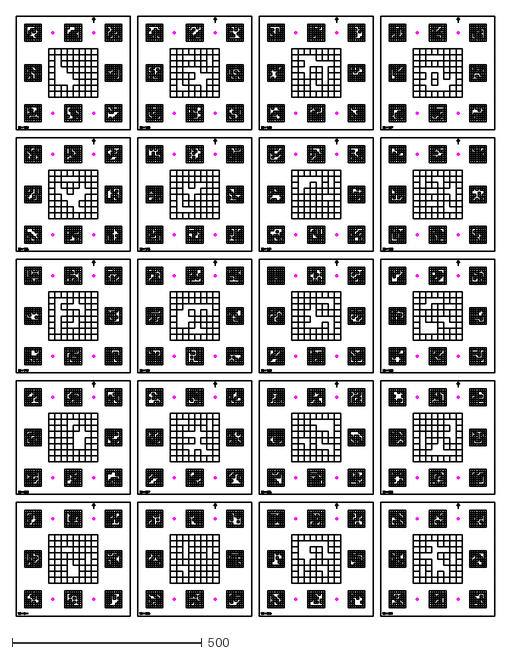
[picture p140: CAD file, 2026-08-25]
Reservoir-AprilTag-Boards-20/generated/all_boards_sheet.dxf
1260.0 x 1580.0
