ShenYuan-sean/Underwater-AprilTag-Board/Reservoir-AprilTag-Boards-20/batch_02/generated/board_30_ids_361-369_guide.dxf

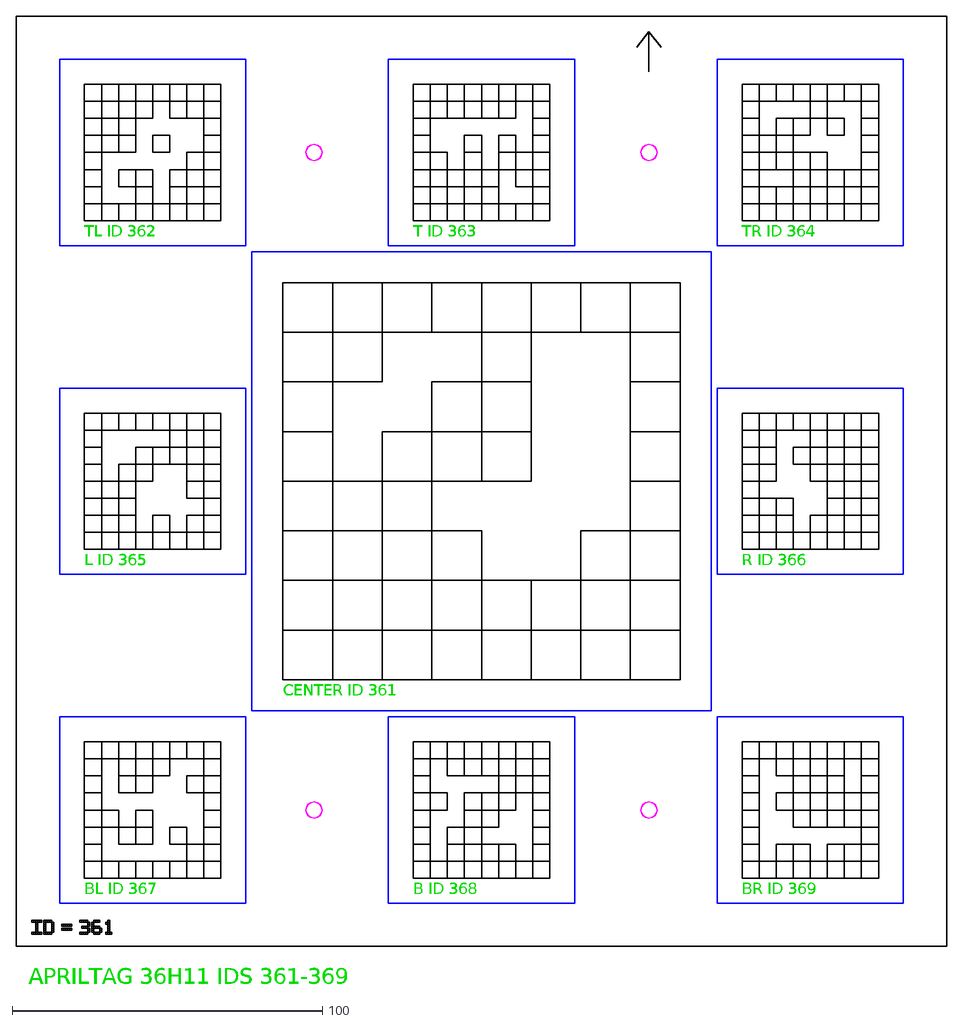
[picture p141: CAD file, 2026-10-02]
Reservoir-AprilTag-Boards-20/batch_02/generated/board_30_ids_361-369_guide.dxf
CENTER ID 361
TL ID 362
T ID 363
TR ID 364
L ID 365
R ID 366
BL ID 367
B ID 368
BR ID 369
APRILTAG 36H11 IDS 361-369
