ShenYuan-sean/Underwater-AprilTag-Board/Reservoir-AprilTag-Boards-20/generated/board_12_ids_199-207_guide.dxf

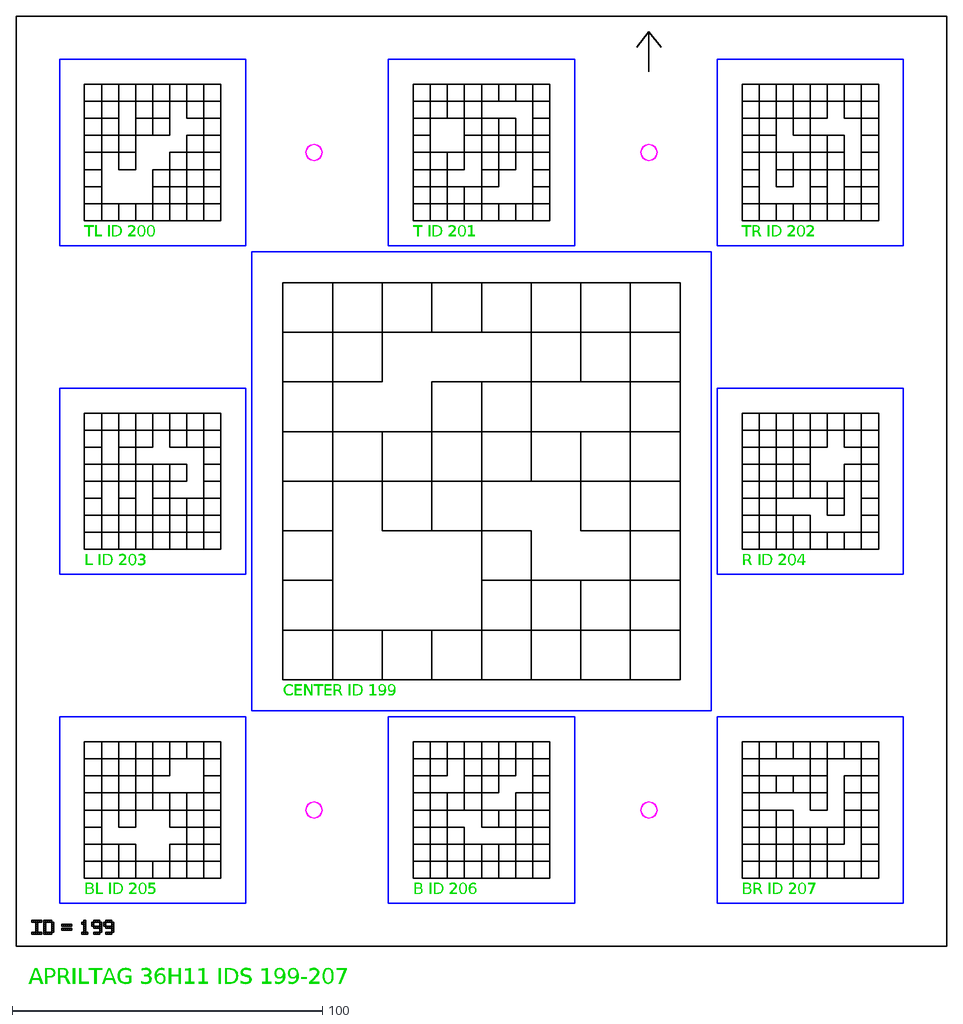
[picture p142: CAD file, 2026-08-25]
Reservoir-AprilTag-Boards-20/generated/board_12_ids_199-207_guide.dxf
CENTER ID 199
TL ID 200
T ID 201
TR ID 202
L ID 203
R ID 204
BL ID 205
B ID 206
BR ID 207
APRILTAG 36H11 IDS 199-207
