ShenYuan-sean/Underwater-AprilTag-Board/Reservoir-AprilTag-Boards-20/generated/board_10_ids_181-189_guide.dxf

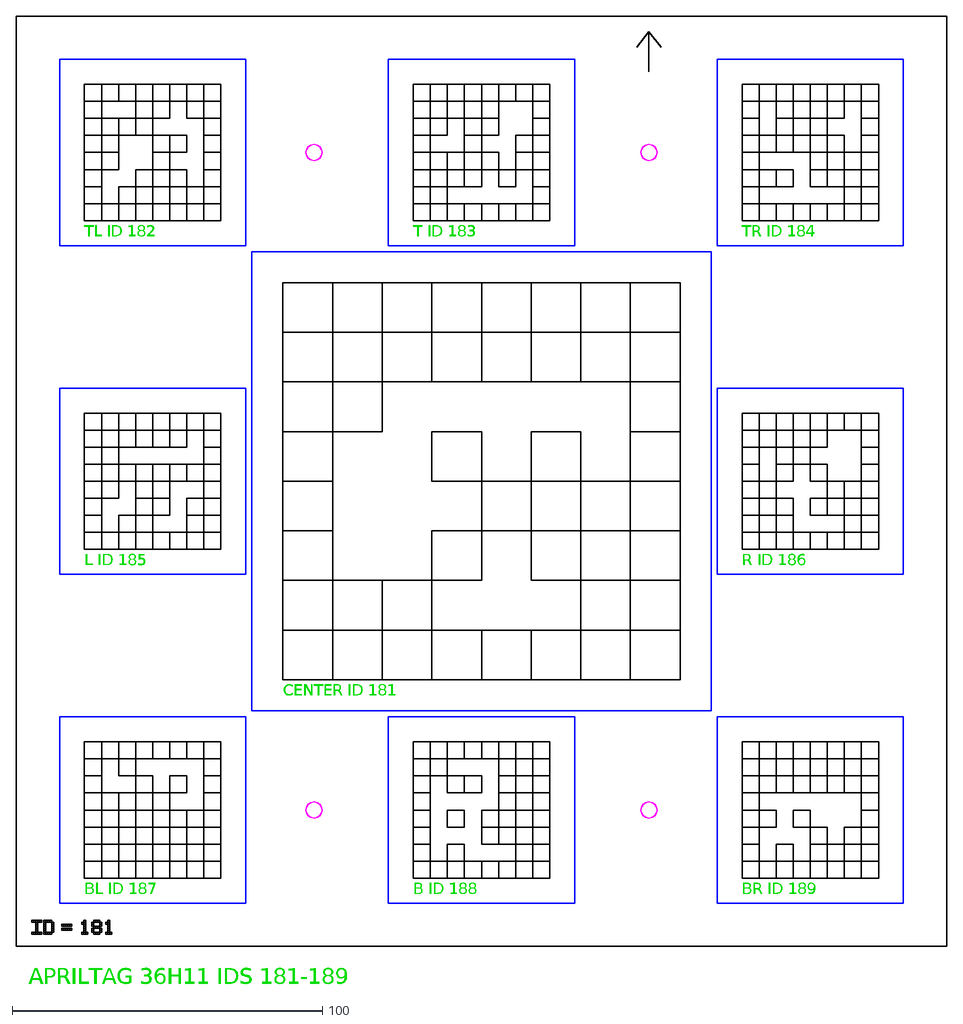
[picture p143: CAD file, 2026-08-25]
Reservoir-AprilTag-Boards-20/generated/board_10_ids_181-189_guide.dxf
CENTER ID 181
TL ID 182
T ID 183
TR ID 184
L ID 185
R ID 186
BL ID 187
B ID 188
BR ID 189
APRILTAG 36H11 IDS 181-189
