ShenYuan-sean/Underwater-AprilTag-Board/Reservoir-AprilTag-Boards-20/generated/board_04_ids_127-135_guide.dxf

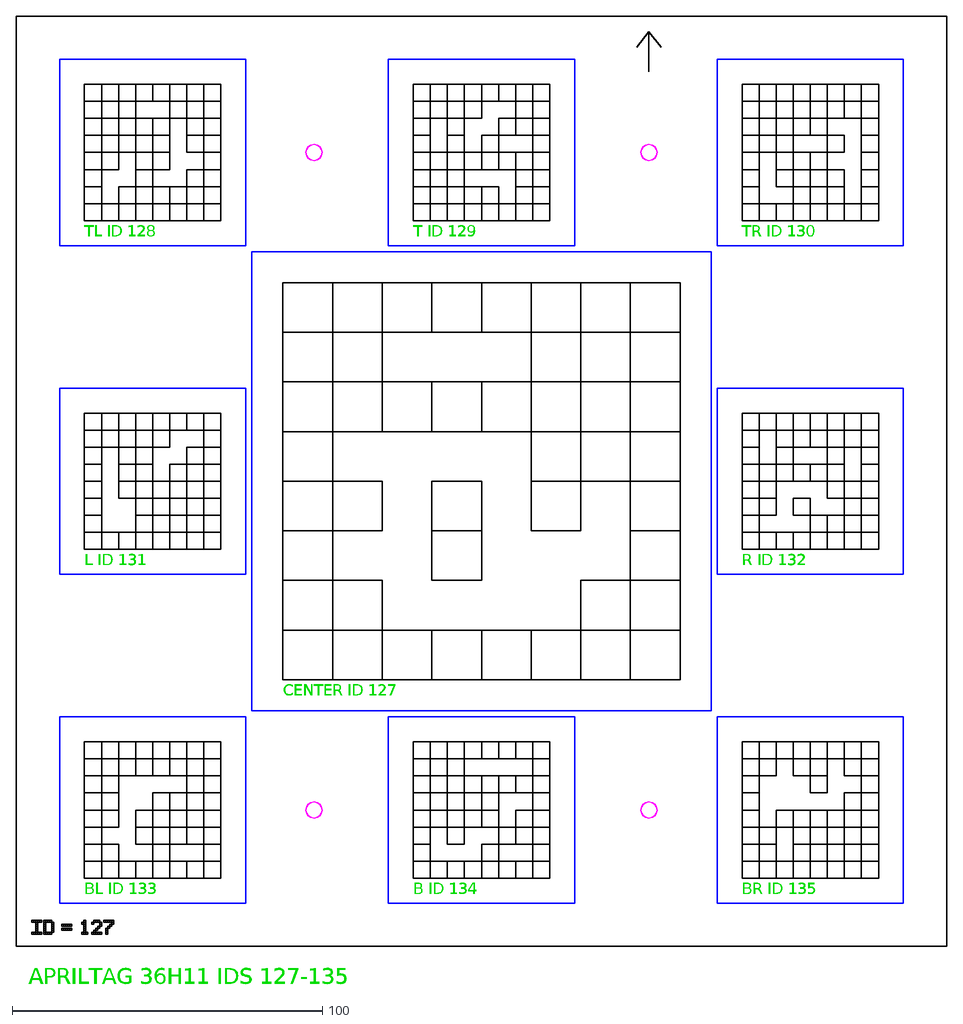
[picture p144: CAD file, 2026-08-25]
Reservoir-AprilTag-Boards-20/generated/board_04_ids_127-135_guide.dxf
CENTER ID 127
TL ID 128
T ID 129
TR ID 130
L ID 131
R ID 132
BL ID 133
B ID 134
BR ID 135
APRILTAG 36H11 IDS 127-135
