ShenYuan-sean/Underwater-AprilTag-Board/Reservoir-AprilTag-Boards-20/batch_02/generated/board_40_ids_451-459_guide.dxf

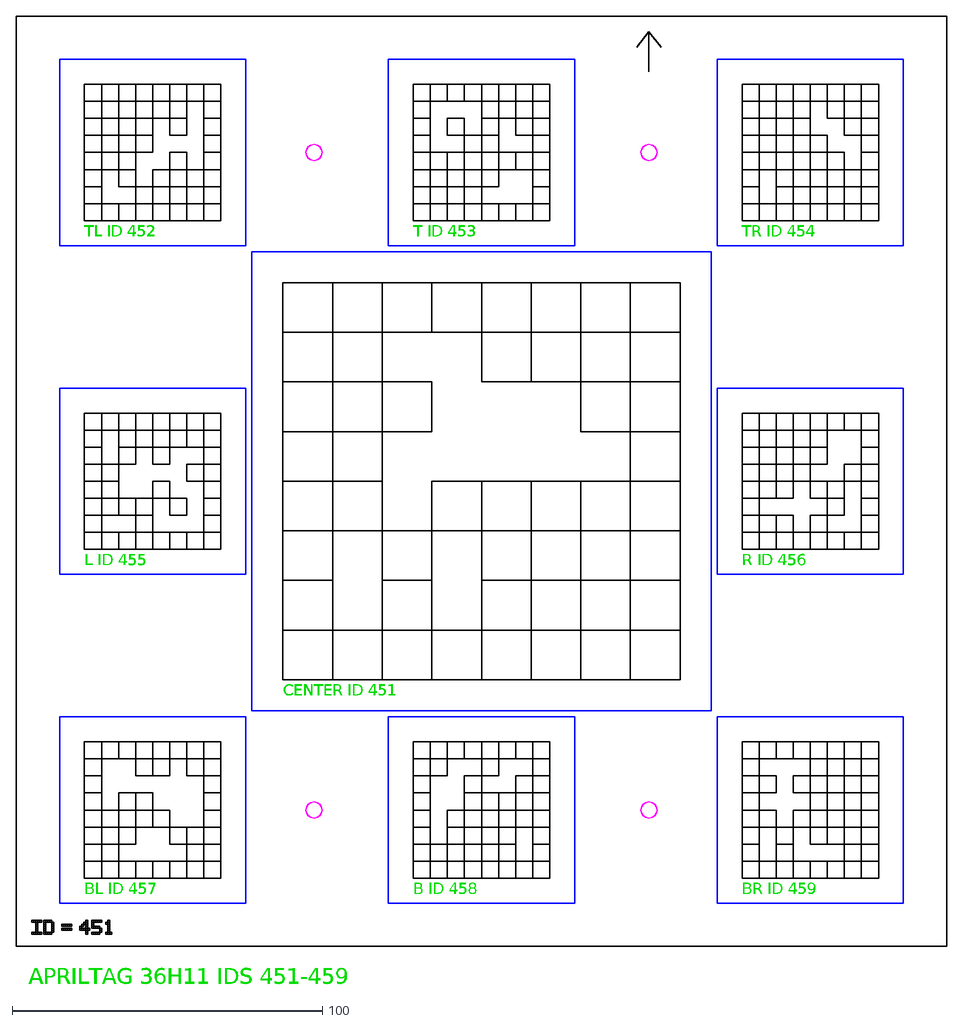
[picture p145: CAD file, 2026-10-02]
Reservoir-AprilTag-Boards-20/batch_02/generated/board_40_ids_451-459_guide.dxf
CENTER ID 451
TL ID 452
T ID 453
TR ID 454
L ID 455
R ID 456
BL ID 457
B ID 458
BR ID 459
APRILTAG 36H11 IDS 451-459
