ShenYuan-sean/Underwater-AprilTag-Board/Reservoir-AprilTag-Boards-20/batch_02/generated/board_36_ids_415-423_guide.dxf

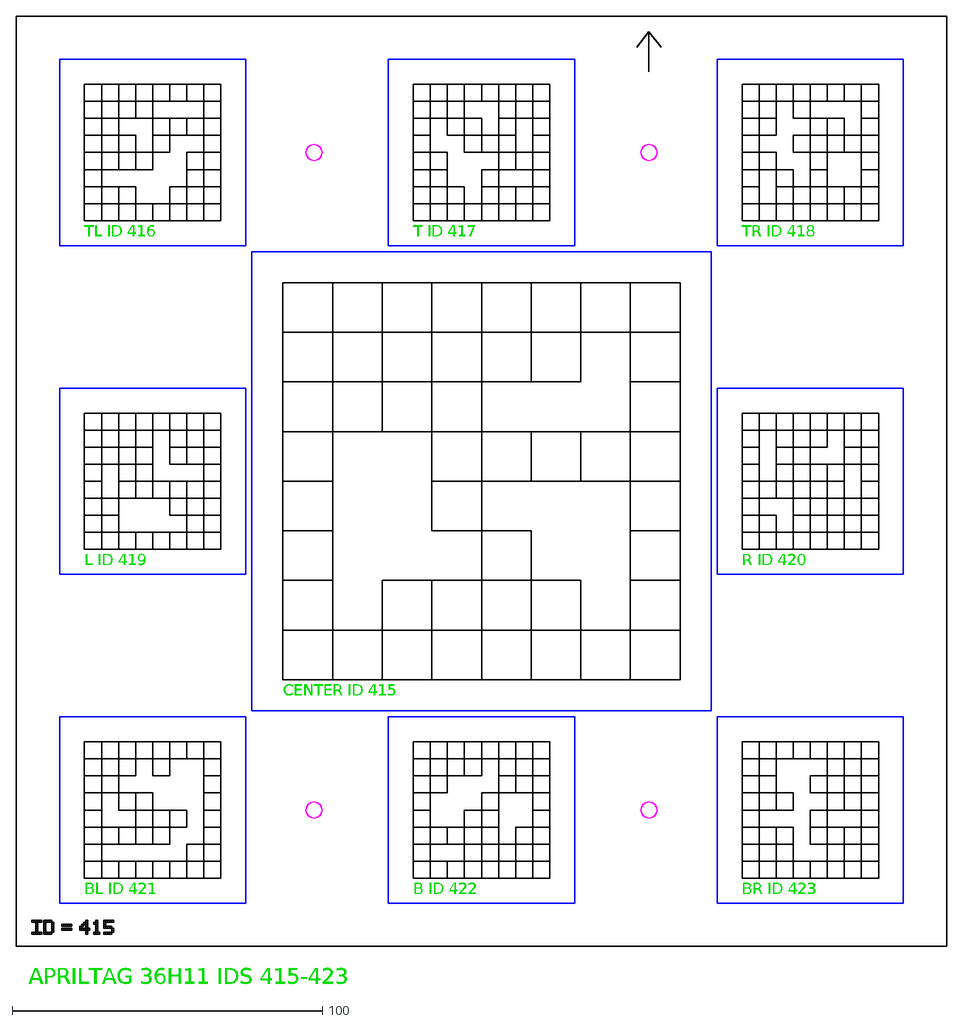
[picture p146: CAD file, 2026-10-02]
Reservoir-AprilTag-Boards-20/batch_02/generated/board_36_ids_415-423_guide.dxf
CENTER ID 415
TL ID 416
T ID 417
TR ID 418
L ID 419
R ID 420
BL ID 421
B ID 422
BR ID 423
APRILTAG 36H11 IDS 415-423
