ShenYuan-sean/Underwater-AprilTag-Board/Reservoir-AprilTag-Boards-20/batch_02/generated/board_23_ids_298-306_guide.dxf

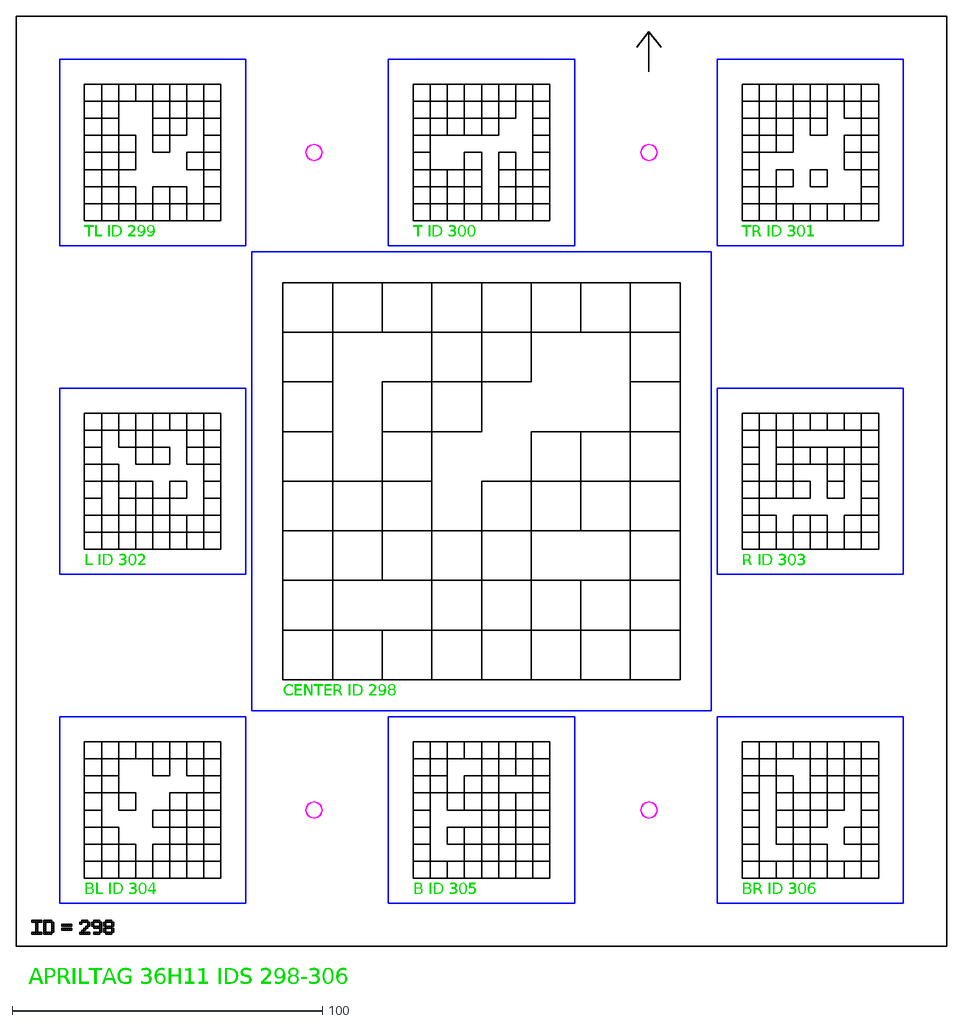
[picture p147: CAD file, 2026-10-02]
Reservoir-AprilTag-Boards-20/batch_02/generated/board_23_ids_298-306_guide.dxf
CENTER ID 298
TL ID 299
T ID 300
TR ID 301
L ID 302
R ID 303
BL ID 304
B ID 305
BR ID 306
APRILTAG 36H11 IDS 298-306
