ShenYuan-sean/Underwater-AprilTag-Board/Reservoir-AprilTag-Boards-20/generated/board_09_ids_172-180_guide.dxf

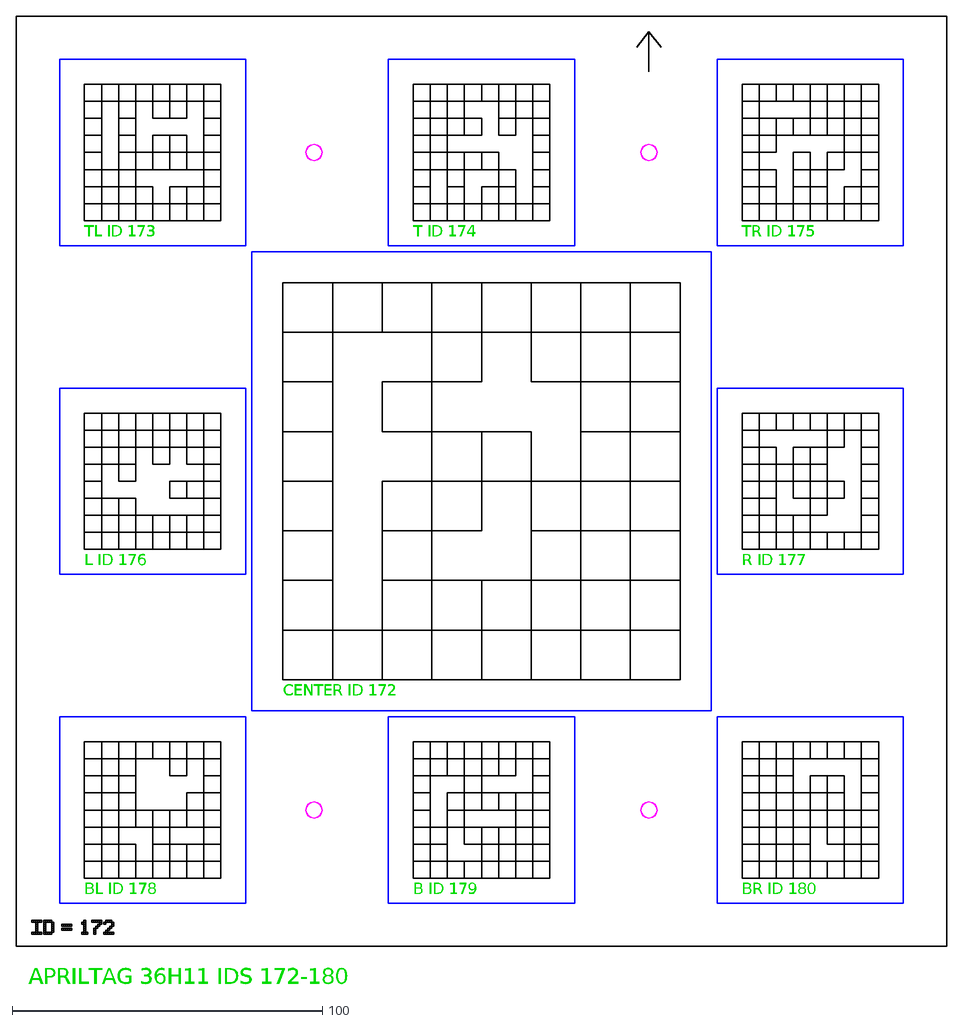
[picture p148: CAD file, 2026-08-25]
Reservoir-AprilTag-Boards-20/generated/board_09_ids_172-180_guide.dxf
CENTER ID 172
TL ID 173
T ID 174
TR ID 175
L ID 176
R ID 177
BL ID 178
B ID 179
BR ID 180
APRILTAG 36H11 IDS 172-180
