ShenYuan-sean/Underwater-AprilTag-Board/Reservoir-AprilTag-Boards-20/batch_02/generated/board_32_ids_379-387_guide.dxf

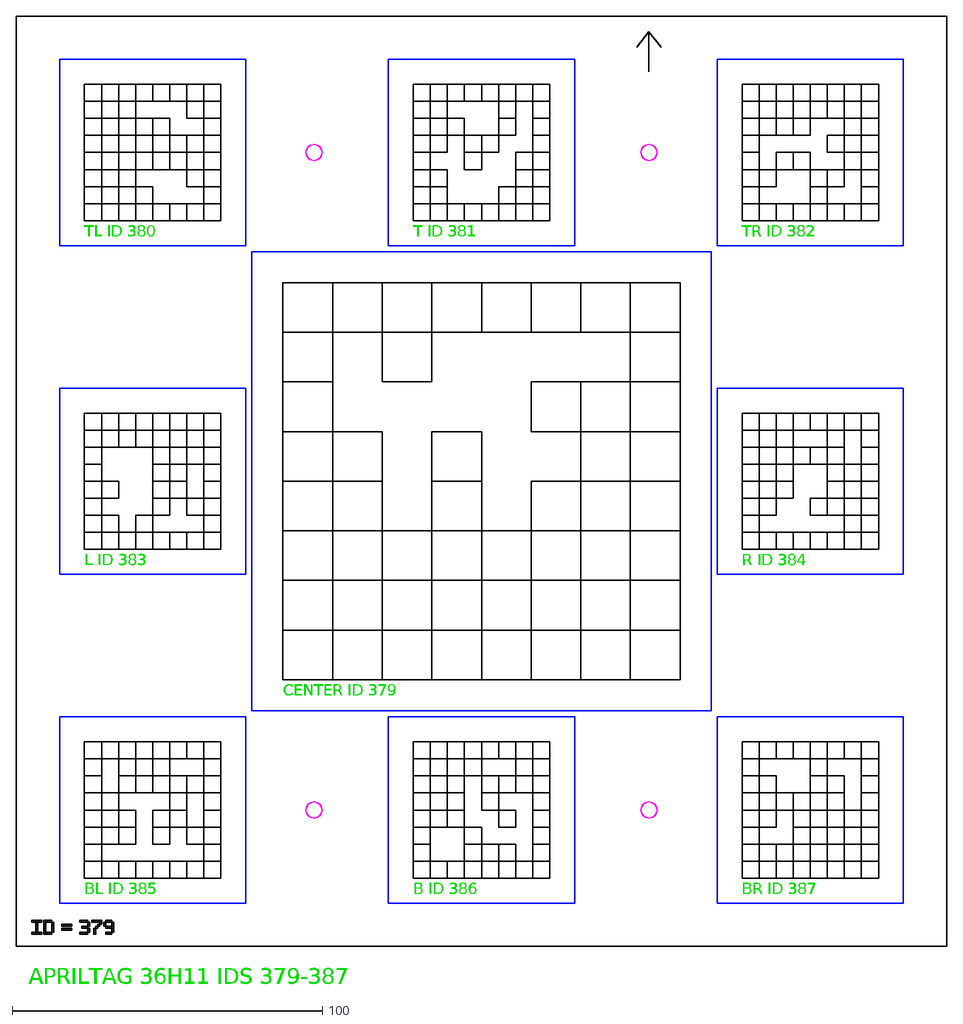
[picture p149: CAD file, 2026-10-02]
Reservoir-AprilTag-Boards-20/batch_02/generated/board_32_ids_379-387_guide.dxf
CENTER ID 379
TL ID 380
T ID 381
TR ID 382
L ID 383
R ID 384
BL ID 385
B ID 386
BR ID 387
APRILTAG 36H11 IDS 379-387
