ShenYuan-sean/Underwater-AprilTag-Board/Reservoir-AprilTag-Boards-20/batch_02/generated/board_22_ids_289-297_guide.dxf

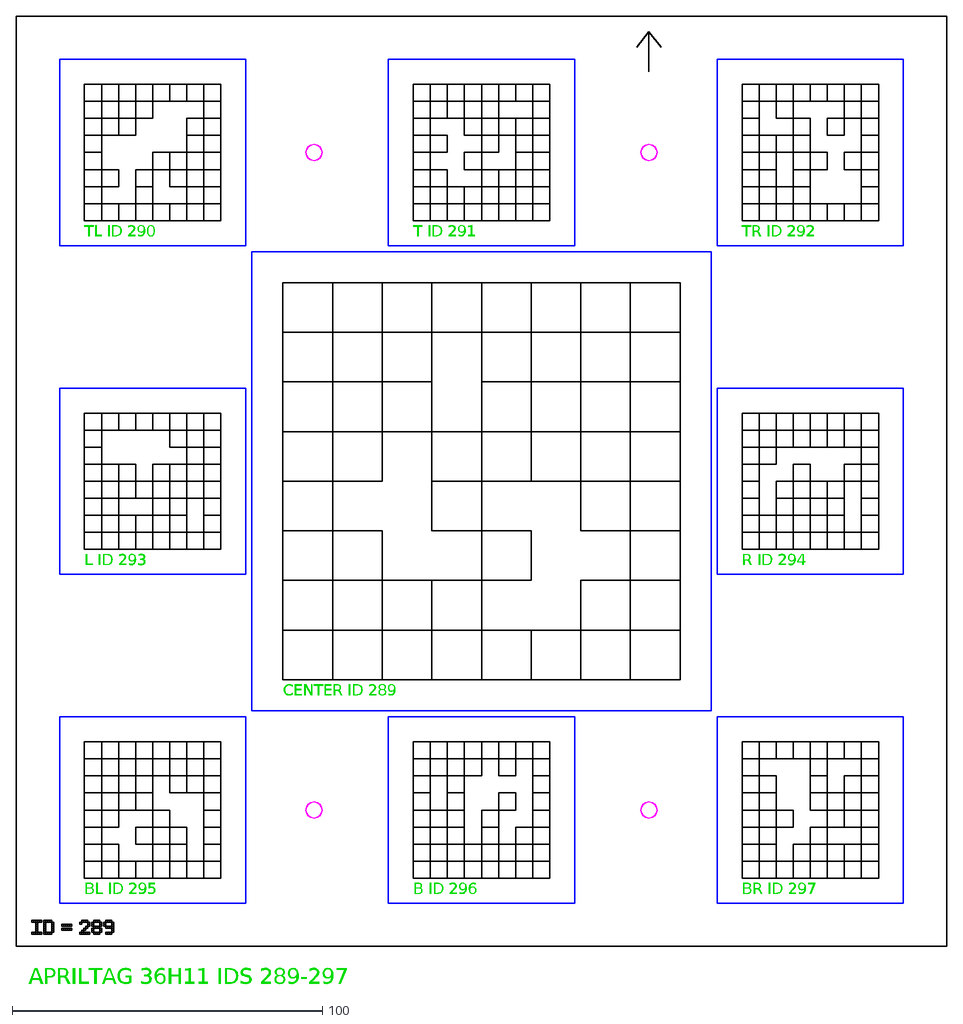
[picture p150: CAD file, 2026-10-02]
Reservoir-AprilTag-Boards-20/batch_02/generated/board_22_ids_289-297_guide.dxf
CENTER ID 289
TL ID 290
T ID 291
TR ID 292
L ID 293
R ID 294
BL ID 295
B ID 296
BR ID 297
APRILTAG 36H11 IDS 289-297
