ShenYuan-sean/Underwater-AprilTag-Board/Reservoir-AprilTag-Boards-20/batch_02/generated/board_26_ids_325-333_guide.dxf

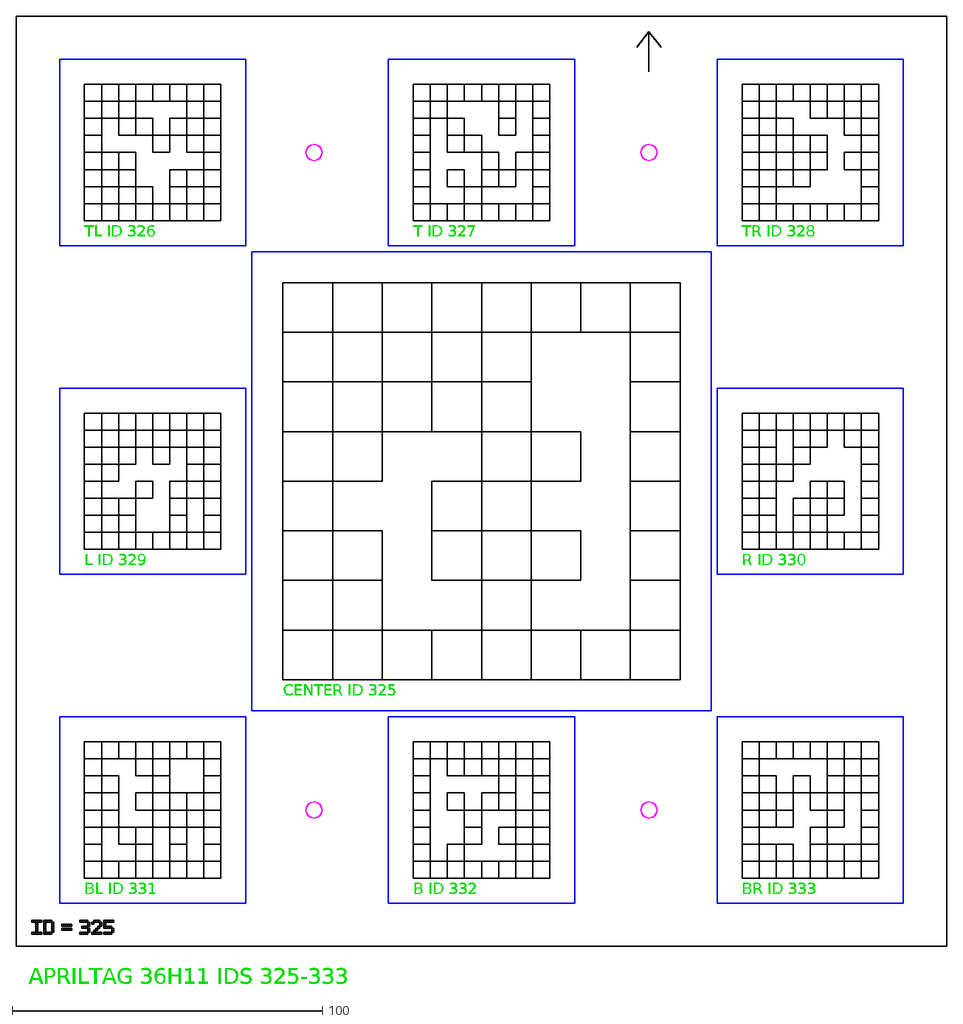
[picture p151: CAD file, 2026-10-02]
Reservoir-AprilTag-Boards-20/batch_02/generated/board_26_ids_325-333_guide.dxf
CENTER ID 325
TL ID 326
T ID 327
TR ID 328
L ID 329
R ID 330
BL ID 331
B ID 332
BR ID 333
APRILTAG 36H11 IDS 325-333
