ShenYuan-sean/Underwater-AprilTag-Board/Reservoir-AprilTag-Boards-20/generated/board_14_ids_217-225_guide.dxf

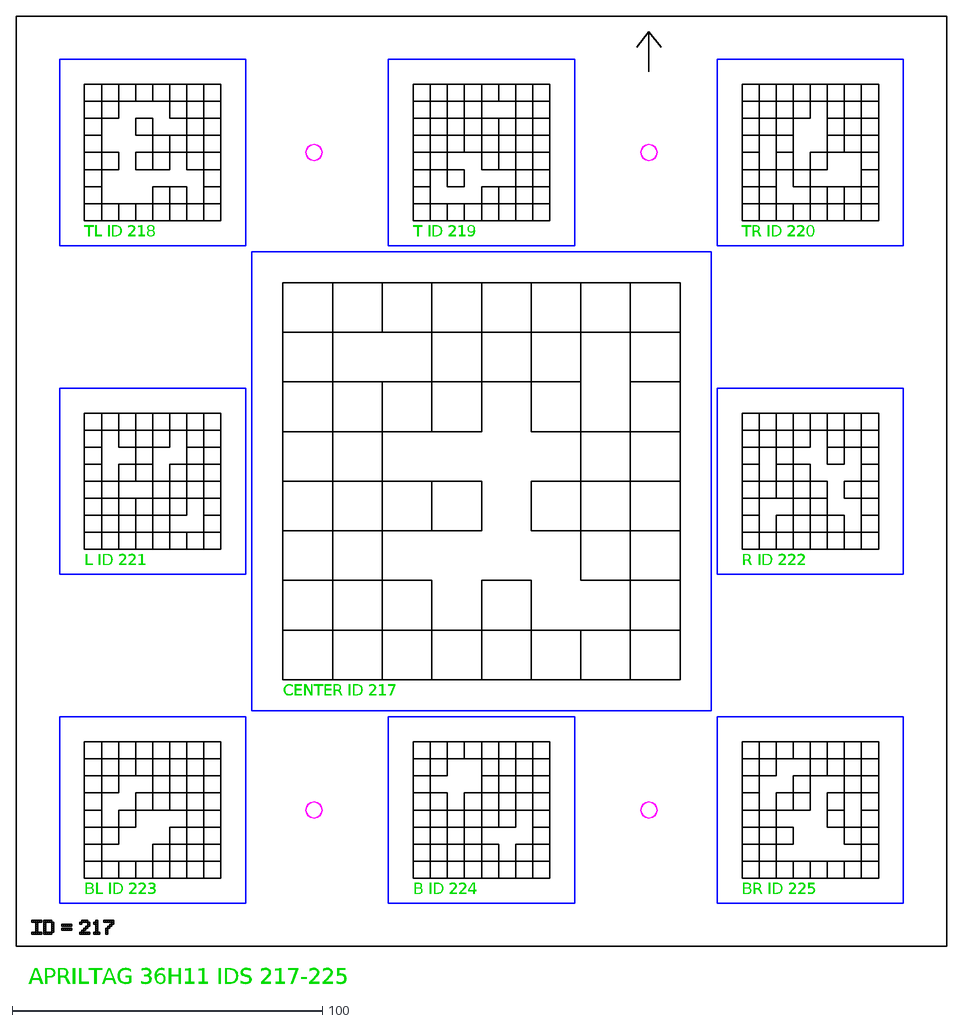
[picture p152: CAD file, 2026-08-25]
Reservoir-AprilTag-Boards-20/generated/board_14_ids_217-225_guide.dxf
CENTER ID 217
TL ID 218
T ID 219
TR ID 220
L ID 221
R ID 222
BL ID 223
B ID 224
BR ID 225
APRILTAG 36H11 IDS 217-225
