ShenYuan-sean/Underwater-AprilTag-Board/Reservoir-AprilTag-Boards-20/batch_02/generated/board_39_ids_442-450_guide.dxf

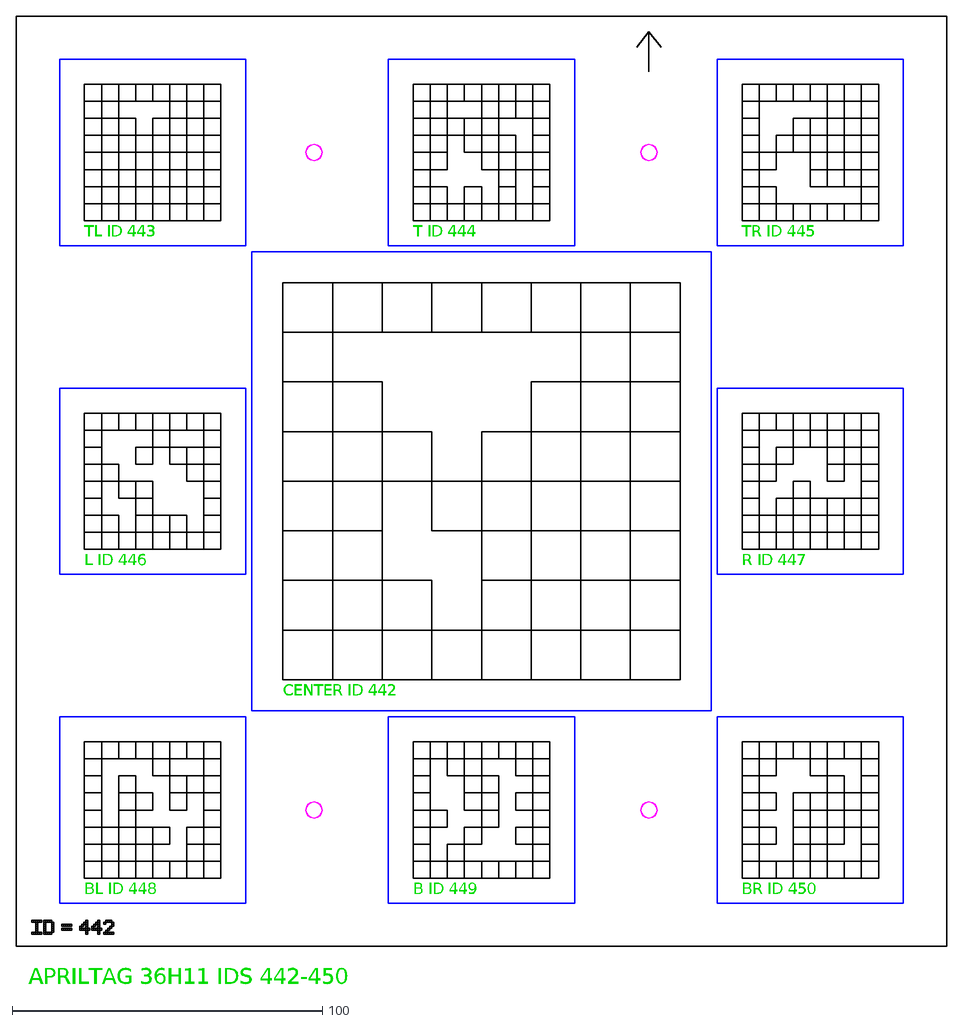
[picture p153: CAD file, 2026-10-02]
Reservoir-AprilTag-Boards-20/batch_02/generated/board_39_ids_442-450_guide.dxf
CENTER ID 442
TL ID 443
T ID 444
TR ID 445
L ID 446
R ID 447
BL ID 448
B ID 449
BR ID 450
APRILTAG 36H11 IDS 442-450
