ShenYuan-sean/Underwater-AprilTag-Board/Reservoir-AprilTag-Boards-20/generated/board_07_ids_154-162_guide.dxf

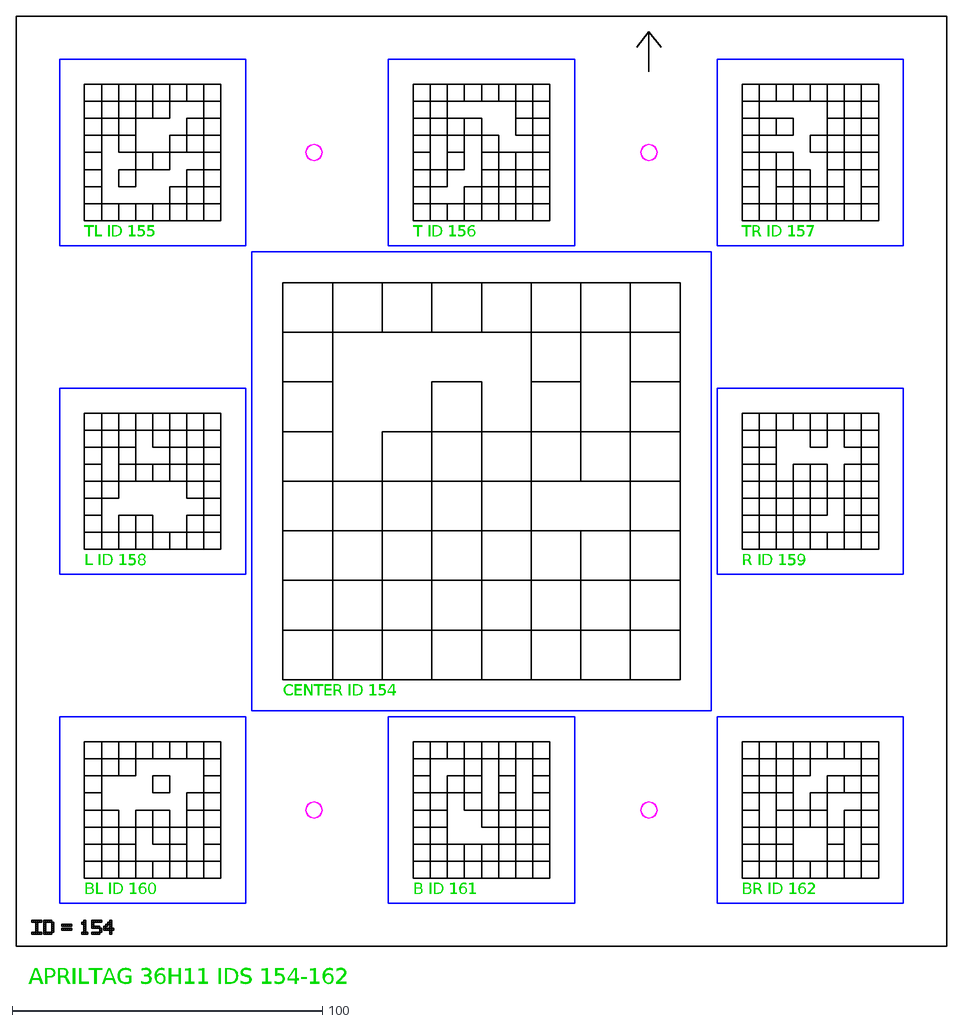
[picture p154: CAD file, 2026-08-25]
Reservoir-AprilTag-Boards-20/generated/board_07_ids_154-162_guide.dxf
CENTER ID 154
TL ID 155
T ID 156
TR ID 157
L ID 158
R ID 159
BL ID 160
B ID 161
BR ID 162
APRILTAG 36H11 IDS 154-162
