ShenYuan-sean/Underwater-AprilTag-Board/Reservoir-AprilTag-Boards-20/generated/board_19_ids_262-270_guide.dxf

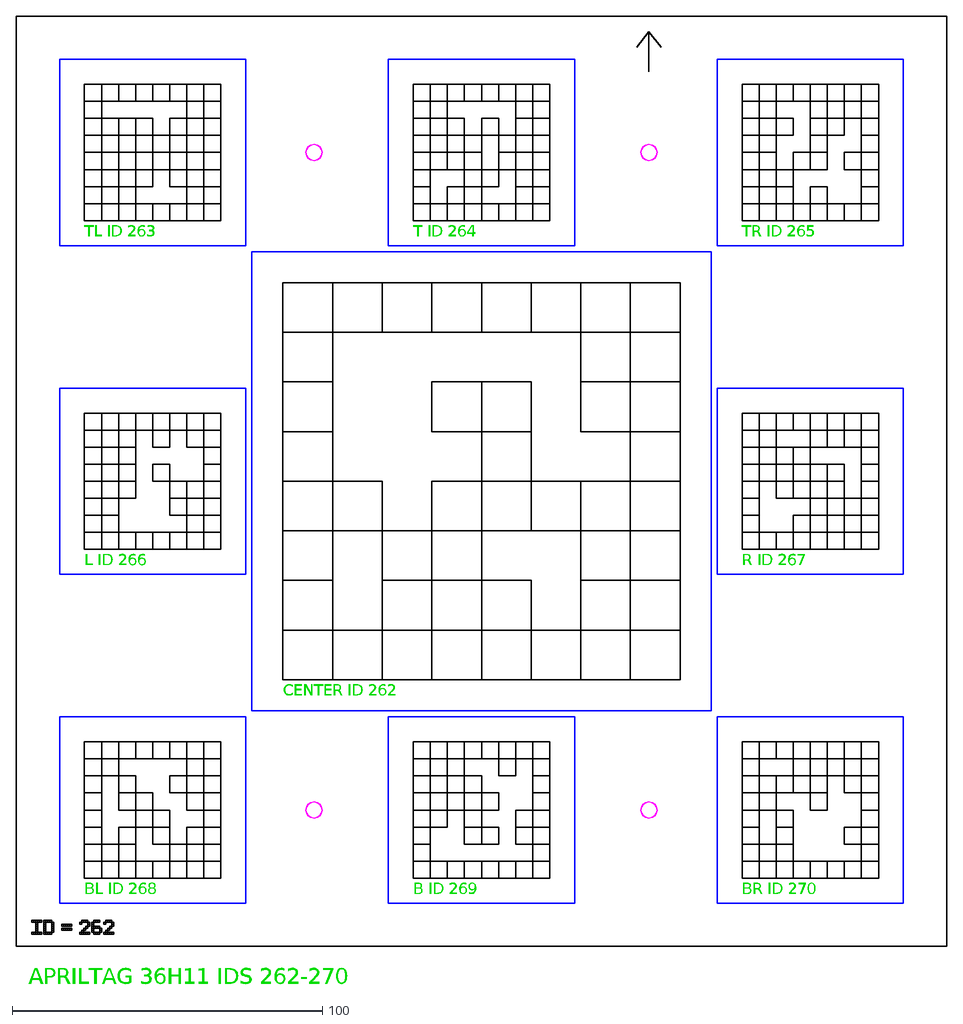
[picture p155: CAD file, 2026-08-25]
Reservoir-AprilTag-Boards-20/generated/board_19_ids_262-270_guide.dxf
CENTER ID 262
TL ID 263
T ID 264
TR ID 265
L ID 266
R ID 267
BL ID 268
B ID 269
BR ID 270
APRILTAG 36H11 IDS 262-270
