ShenYuan-sean/Underwater-AprilTag-Board/Reservoir-AprilTag-Boards-20/generated/board_18_ids_253-261_guide.dxf

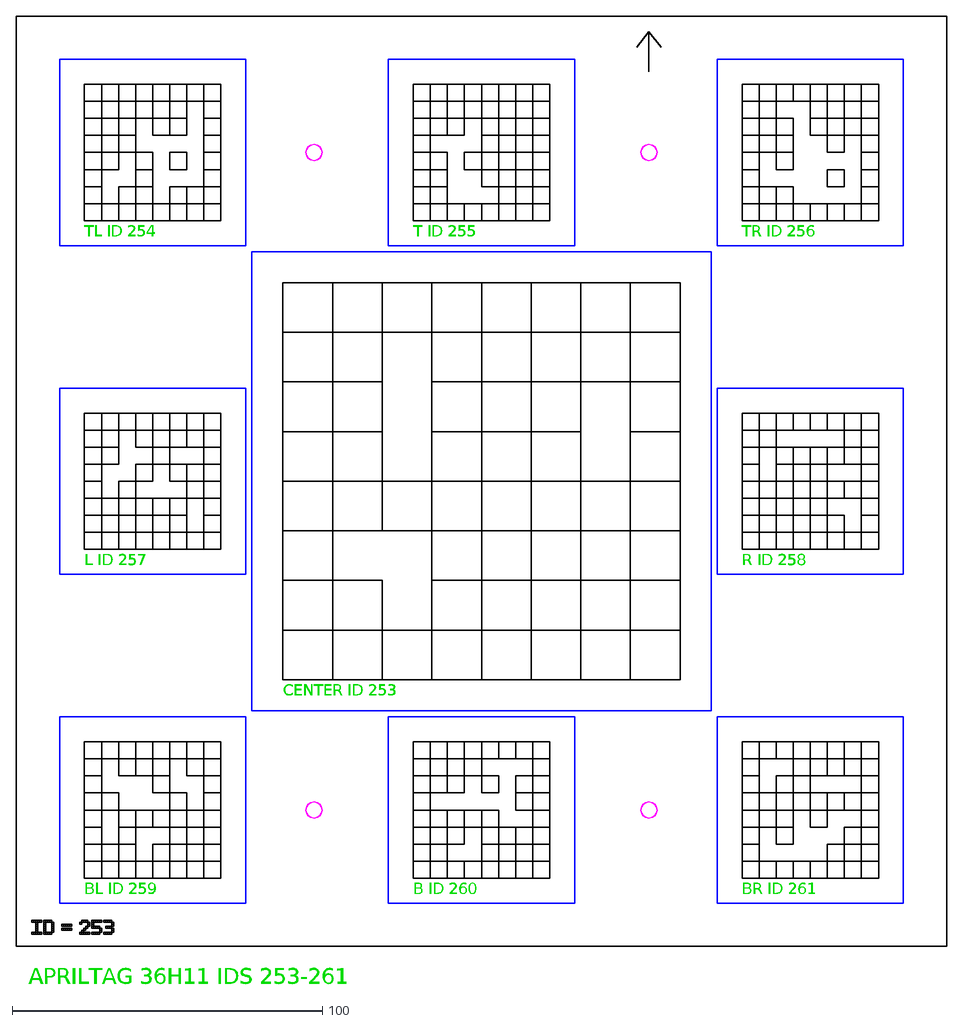
[picture p156: CAD file, 2026-08-25]
Reservoir-AprilTag-Boards-20/generated/board_18_ids_253-261_guide.dxf
CENTER ID 253
TL ID 254
T ID 255
TR ID 256
L ID 257
R ID 258
BL ID 259
B ID 260
BR ID 261
APRILTAG 36H11 IDS 253-261
