ShenYuan-sean/Underwater-AprilTag-Board/Reservoir-AprilTag-Boards-20/batch_02/generated/board_drill_template.dxf

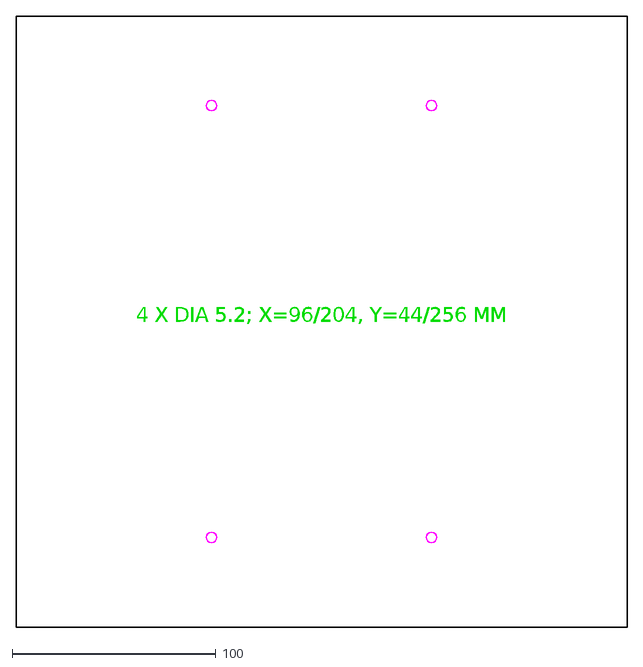
[picture p157: CAD file, 2026-08-25]
Reservoir-AprilTag-Boards-20/batch_02/generated/board_drill_template.dxf
4 X DIA 5.2; X=96/204, Y=44/256 MM
